coleeau/VMC/Software/3rd Party Software/CO2-Pocket-SBC-2.5-main/Software/DOS65/Core OS/C02Constants.asm

;**************************************************************************************************
;*                                                                                                *
;*              C02 Constants used for the 4.0x releases of C02BIOS4 and C02Monitor4              *
;*                                                                                                *
;*                                                                                                *
;*                                  15/02/2023 (Day/Month/Year)                                   *
;*                                                                                                *
;**************************************************************************************************
; C02BIOS / C02Monitor Version is now at 4.02                                                     *
; - All Constants and Variables are now defined in a single source file (this one) for assembling *
; - both the C02BIOS4 and the C02Monitor4. It is also used for the Template for writing code to   *
; - be used for the C02 Pocket SBC and Adapters.                                                  *
;                                                                                                 *
; - Be sure to include this file at the start of any source file that needs it.                   *
;                                                                                                 *
;**************************************************************************************************
;                                                                                                 *
;          - Page Zero locations $00 to $9F (160 bytes) reserved for user applications            * 
;                                                                                                 *
;**************************************************************************************************
;
PGZERO_ST       .EQU    $A0                     ;Start of Monitor Page 0 use ($A0-$CF, 48 bytes)
;
BUFF_PG0        .EQU    PGZERO_ST+00            ;Default Page zero location for Monitor buffers
;
INBUFF          .EQU    BUFF_PG0+00             ;Input Buffer - 4 bytes ($A0-$A3)
DATABUFF        .EQU    BUFF_PG0+04             ;Data Buffer - 6 bytes ($A4-$A9)
;
;       - 16-bit variables:
HEXDATAH        .EQU    PGZERO_ST+10            ;Hexadecimal input
HEXDATAL        .EQU    PGZERO_ST+11
BINVALL         .EQU    PGZERO_ST+12            ;Binary Value for HEX2ASC
BINVALH         .EQU    PGZERO_ST+13
COMLO           .EQU    PGZERO_ST+14            ;User command address
COMHI           .EQU    PGZERO_ST+15
INDEXL          .EQU    PGZERO_ST+16            ;Index for address - multiple routines
INDEXH          .EQU    PGZERO_ST+17
TEMP1L          .EQU    PGZERO_ST+18            ;Index for word temp value used by Memdump
TEMP1H          .EQU    PGZERO_ST+19
TEMP2L          .EQU    PGZERO_ST+20            ;Index for Text entry
TEMP2H          .EQU    PGZERO_ST+21
PROMPTL         .EQU    PGZERO_ST+22            ;Prompt string address
PROMPTH         .EQU    PGZERO_ST+23
SRCL            .EQU    PGZERO_ST+24            ;Source address for memory operations
SRCH            .EQU    PGZERO_ST+25
TGTL            .EQU    PGZERO_ST+26            ;Target address for memory operations
TGTH            .EQU    PGZERO_ST+27
LENL            .EQU    PGZERO_ST+28            ;Length address for memory operations
LENH            .EQU    PGZERO_ST+29
;
;       - 8-bit variables and constants:
BUFIDX          .EQU    PGZERO_ST+30            ;Buffer index
BUFLEN          .EQU    PGZERO_ST+31            ;Buffer length
IDX             .EQU    PGZERO_ST+32            ;Temp Indexing
IDY             .EQU    PGZERO_ST+33            ;Temp Indexing
TEMP1           .EQU    PGZERO_ST+34            ;Temp - Code Conversion routines
TEMP2           .EQU    PGZERO_ST+35            ;Temp - Memory/EEPROM/SREC routines - Disassembler
TEMP3           .EQU    PGZERO_ST+36            ;Temp - EEPROM/SREC routines
CMDFLAG         .EQU    PGZERO_ST+37            ;Command Flag, bit specific, used by many routines
OPXMDM          .EQU    PGZERO_ST+38            ;Saved Opcode/Xmodem Flag variable
;
;       - Xmodem transfer variables
CRCHI           .EQU    PGZERO_ST+39            ;CRC hi byte  (two byte variable)
CRCLO           .EQU    PGZERO_ST+40            ;CRC lo byte - Operand in Disassembler
CRCCNT          .EQU    PGZERO_ST+41            ;CRC retry count - Operand in Disassembler
PTRL            .EQU    PGZERO_ST+42            ;Data pointer lo byte - Mnemonic in Disassembler
PTRH            .EQU    PGZERO_ST+43            ;Data pointer hi byte - Mnemonic in Disassembler
BLKNO           .EQU    PGZERO_ST+44            ;Block number
;
;        - Macro Loop Counter variables
LPCNTL          .EQU    PGZERO_ST+45            ;Loop Count low byte
LPCNTH          .EQU    PGZERO_ST+46            ;Loop Count high byte
;
;       - Spare Monitor byte for future use
SPARE_M0        .EQU    PGZERO_ST+47            ;Spare Monitor page zero byte
;
;       - BIOS variables, pointers, flags located at top of Page Zero
BIOS_PG0        .EQU    PGZERO_ST+48            ;Start of BIOS page 0 use ($D0-$FF, 48 bytes)
;
;       - BRK handler routine
PCL             .EQU    BIOS_PG0+00             ;Program Counter Low index
PCH             .EQU    BIOS_PG0+01             ;Program Counter High index
PREG            .EQU    BIOS_PG0+02             ;Temp Status Reg
SREG            .EQU    BIOS_PG0+03             ;Temp Stack ptr
YREG            .EQU    BIOS_PG0+04             ;Temp Y Reg
XREG            .EQU    BIOS_PG0+05             ;Temp X Reg
AREG            .EQU    BIOS_PG0+06             ;Temp A Reg
;
;       - 28L92 IRQ handler pointers and status
ICNT_A          .EQU    BIOS_PG0+07             ;Input buffer count
IHEAD_A         .EQU    BIOS_PG0+08             ;Input buffer head pointer
ITAIL_A         .EQU    BIOS_PG0+09             ;Input buffer tail pointer
OCNT_A          .EQU    BIOS_PG0+10             ;Output buffer count
OHEAD_A         .EQU    BIOS_PG0+11             ;Output buffer head pointer
OTAIL_A         .EQU    BIOS_PG0+12             ;Output buffer tail pointer
;
ICNT_B          .EQU    BIOS_PG0+13             ;Input buffer count
IHEAD_B         .EQU    BIOS_PG0+14             ;Input buffer head pointer
ITAIL_B         .EQU    BIOS_PG0+15             ;Input buffer tail pointer
OCNT_B          .EQU    BIOS_PG0+16             ;Output buffer count
OHEAD_B         .EQU    BIOS_PG0+17             ;Output buffer head pointer
OTAIL_B         .EQU    BIOS_PG0+18             ;Output buffer tail pointer
UART_IRT        .EQU    BIOS_PG0+19             ;SC28L92 Interrupt Status byte
;
;       - Real-Time Clock variables
; These are repurposed for adding a Realtime clock chip (DS1501/DS1511)
; The Ticks, Seconds, Minutes and Hours remain the same in function.
; The 16-bit Days variable is replaced however.
; - The DAY_DATE is a new variable. To minimize Page Zero usage, it has two functions
;       Bits 0-4 represent the days of the Month 1-31
;       Bits 5-7 represent the Day of the Week, 1-7 (Saturday=1)
; The Months are handled by the upper 4 bits of the MONTH_YEAR variable
; The Century is handled by a the Year (0-255) and the lower 4 bits of the MONTH_YEAR variable
;
TICKS           .EQU    BIOS_PG0+20             ;Number of timer countdowns = 1 second (100)
SECS            .EQU    BIOS_PG0+21             ;Seconds: 0-59
MINS            .EQU    BIOS_PG0+22             ;Minutes: 0-59
HOURS           .EQU    BIOS_PG0+23             ;Hours: 0-23
DAY_DATE        .EQU    BIOS_PG0+24             ;Day: (bits 5-7) Date: (bits 0-4)
MONTH_CENTURY   .EQU    BIOS_PG0+25             ;Month: (bits 4-7) Century: (bits 0-3)
YEAR            .EQU    BIOS_PG0+26             ;Century 0-255 plus 4 bits as noted above
RTC_TEMP        .EQU    BIOS_PG0+27             ;Temp work byte for updating shared variables
;
;       - Delay Timer variables
MSDELAY         .EQU    BIOS_PG0+28             ;Timer delay countdown byte (255 > 0)
SETMS           .EQU    BIOS_PG0+29             ;Set timeout for delay routines - BIOS use only
DELLO           .EQU    BIOS_PG0+30             ;Delay value BIOS use only
DELHI           .EQU    BIOS_PG0+31             ;Delay value BIOS use only
;
;       - Count variables for 10ms benchmark timing
MS10_CNT        .EQU    BIOS_PG0+32             ;10ms Count variable
SECL_CNT        .EQU    BIOS_PG0+33             ;Seconds Low byte count
SECH_CNT        .EQU    BIOS_PG0+34             ;Seconds High byte count
;
;       - Address and pointers for IDE Interface
LBA_ADDR_LOW    .EQU    BIOS_PG0+35             ;LBA Transfer Address low byte
LBA_ADDR_HIGH   .EQU    BIOS_PG0+36             ;LBA Transfer Address high byte
;
LBA_XFER_CNT    .EQU    BIOS_PG0+37             ;LBA Transfer Count 1-xx (check RAM space!)
LBA_LOW_BYTE    .EQU    BIOS_PG0+38             ;LBA Block number bits 0-7
LBA_HIGH_BYTE   .EQU    BIOS_PG0+39             ;LBA Block number bits 8-15
LBA_EXT_BYTE    .EQU    BIOS_PG0+40             ;LBA Block number bits 16-23
;
BIOS_XFERL      .EQU    BIOS_PG0+41             ;BIOS Move Routine low byte
BIOS_XFERH      .EQU    BIOS_PG0+42             ;BIOS Move Routine high byte
BIOS_XFERC      .EQU    BIOS_PG0+43             ;BIOS Block Count moved (needs to be set)
;
IDE_STATUS_RAM  .EQU    BIOS_PG0+44             ;IDE RAM-Based Status
;
SPARE_B0        .EQU    BIOS_PG0+45             ;Spare byte 0
SPARE_B1        .EQU    BIOS_PG0+46             ;Spare byte 1
;
;       - Timer/Counter Match flag for Delay/Benchmark
MATCH           .EQU    BIOS_PG0+47             ;Bit7 used for Delay, Bit6 used for Benchmark
                                                ;Bits 3,2,1 used for IDE Interrupt Handler
;
;       - Default for RTC tick count - number of IRQs for 1 second
DF_TICKS        .EQU    100                     ;Timer is 10 milliseconds (100 x 10ms = 1 second)
;
;**************************************************************************************************
IBUF_A          .EQU    $0200                   ;Console Input Buffer - 128 bytes
OBUF_A          .EQU    $0280                   ;Console Output Buffer - 128 bytes
;
IBUF_B          .EQU    $0400                   ;Alternate Input Buffer - 128 bytes
OBUF_B          .EQU    $0480                   ;Alternate Output Buffer - 128 bytes
;**************************************************************************************************
SOFTVEC         .EQU    $0300                   ;Start of soft vectors
;The Interrupt structure is vector based. During startup, Page $03 is loaded from ROM.
; The soft vectors are structured to allow inserting additional routines either before
; or after the ROM based routines. This allows flexibility and changing of routine priority.
;
;The main set of vectors occupy the first 16 bytes of Page $03. The ROM handler for
; NMI, BRK and IRQ jump to the first 3 vectors. The following 3 vectors are loaded with
; return addresses to the ROM handler for each. The following 2 vectors are the cold and
; warm entry points for the Monitor. After the basic initialization, the monitor is entered.
;
;The following vector set allows inserts, pre or post for NMI/BRK/IRQ. There a total of 8 inserts
; which occupy 16 bytes. They can be used as required.
; Currently, VECINSRT0 will be used if an IDE Controller is detected.
;
NMIVEC0         .EQU    SOFTVEC+00              ;NMI Vector Entry 0
BRKVEC0         .EQU    SOFTVEC+02              ;BRK Vector Entry 0
IRQVEC0         .EQU    SOFTVEC+04              ;IRQ Vector Entry 0
;
NMIRTVEC0       .EQU    SOFTVEC+06              ;NMI Vector Return 0
BRKRTVEC0       .EQU    SOFTVEC+08              ;BRK Vector Return 0
IRQRTVEC0       .EQU    SOFTVEC+10              ;IRQ Vector Return 0
;
CLDMNVEC0       .EQU    SOFTVEC+12              ;Monitor Cold Entry Vector 0
WRMMNVEC0       .EQU    SOFTVEC+14              ;Monitor Warm Entry Vector 0
;
VECINSRT0       .EQU    SOFTVEC+16              ;1st Vector Insert
VECINSRT1       .EQU    SOFTVEC+18              ;2nd Vector Insert
VECINSRT2       .EQU    SOFTVEC+20              ;3rd Vector Insert
VECINSRT3       .EQU    SOFTVEC+22              ;4th Vector Insert
VECINSRT4       .EQU    SOFTVEC+24              ;5th Vector Insert
VECINSRT5       .EQU    SOFTVEC+26              ;6th Vector Insert
VECINSRT6       .EQU    SOFTVEC+28              ;7th Vector Insert
VECINSRT7       .EQU    SOFTVEC+30              ;8th Vector Insert
;
;**************************************************************************************************
;
;Soft Config values below are loaded from ROM and are the default I/O setup Configuration data that
; the INIT_x routines use. As a result, you can write a routine to change the I/O Configuration
; data and use the standard ROM routines to initialize the I/O without restarting or changing ROM
; A Reset (HW or coded) will reinitialize the I/O with the ROM default I/O Configuration.
;
;There are a total of 32 Bytes Configuration data reserved starting at $0320,
; - 22 bytes are reserved for the NXP SC28L92 DUART.
;
SOFTCFG         .EQU    SOFTVEC+32              ;Start of hardware Config parameters
;
LOAD_28L92      .EQU    SOFTCFG+00              ;SC28L92 Soft Config Data
;
; The configuration for the DUART consists of 14 parameters/commands stored in the following
; - memory locations. Note that these are sent in reverse, i.e., $32E thru $320.
;
;       $320    .DB     %00000011       $03     ;Enable OP0/1 for RTS control Port A/B
;       $321    .DB     %00001010       $A0     ;Disable Receiver/Disable Transmitter B
;       $322    .DB     %00001001       $09     ;Enable Receiver/Disable Transmitter A
;       $323    .DB     %00001111       $0F     ;Interrupt Mask Register setup
;       $324    .DB     %11100000       $E0     ;Aux Register setup for Counter/Timer
;       $325    .DB     %01001000       $48     ;Counter/Timer Upper Preset (18432 decimal)
;       $326    .DB     %00000000       $00     ;Counter/Timer Lower Preset
;       $327    .DB     %11001100       $CC     ;Baud Rate clock for B Rcv/Xmt - 115.2K
;       $328    .DB     %11001100       $CC     ;Baud Rate clock for A Rcv/Xmt - 115.2K
;       $329    .DB     %00110000       $30     ;Reset Transmitter B
;       $32A    .DB     %00100000       $20     ;Reset Receiver B
;       $32B    .DB     %00110000       $30     ;Reset Transmitter A
;       $32C    .DB     %00100000       $20     ;Reset Receiver A
;       $32D    .DB     %00000000       $00     ;Interrupt Mask Register setup (clear)
;       $32E    .DB     %11110000       $F0     ;Command Register A - Disable Power Down
;       $32F    .DB     %11111111       $FF     ;Spare Byte
;
; The MR registers of the DUART also have soft config data loaded here, but is separate from the
; - main register config data, as these are all accessed via a single I/O port (auto-indexed).
; - These are also sent in reverse order as above.
;
;       $330    .DB     %00010111       $17     ;Mode Register 2 data
;       $331    .DB     %11010011       $D3     ;Mode Register 1 Data
;       $332    .DB     %11111001       $F9     ;Mode Register 0 Data
;
;       $333    .DB     %00010111       $17     ;Mode Register 2 data
;       $334    .DB     %11010011       $D3     ;Mode Register 1 Data
;       $335    .DB     %11000001       $C1     ;Mode Register 0 Data
;
;       10 additional bytes all reserved as $FF fill up the remaining soft configuration data.
;
; The Microdrive is initialized and the total LBA count is save here during startup.
;  It is used by various utilities and allows drive capacity sensing without sending additional
;  commands to the Microdrive. A total of 4 bytes are used for a 32-bit LBA count. These are saved
;  at addresses $33C - $33F. Order is low-word/high-word. Each word is low-byte/high/byte.
;
LOAD_IDE        .EQU    SOFTCFG+28              ;IDE/CF-Card Soft Config Data
;
;       $33C    .DW                             ;Low order LBA count
;       $33E    .DW                             ;High order LBA count
;
;Search Buffer is 16 bytes in length. Used to hold search string for text or hex data
SRCHBUFF        .EQU    SOFTCFG+32              ;Located in Page $03 following Hardware Config data
;       $340                                    ;Start of search buffer (16 bytes)
;
;Xmodem/CRC Loader also provides Motorola S19 Record sense and load. Designed to handle the S19
; records from the WDC Assembler/Linker package. This requires a 44 byte buffer to parse each valid
; S1 record, located just before the 132 Byte Xmodem frame buffer. Total Buffer space for the
; Xmodem/CRC Loader is 176 bytes
;
;Valid S-record headers are "S1" and "S9". For S1, the maximum length is "$19" hex. The last S1
; record can be less. S9 record is always the last record with no data. WDC Linker also appends
; a CR/LF to the end of each record for a total of 44 bytes.
;
SRBUFF          .EQU    SOFTCFG+48              ;S-Record buffer, up to 44 bytes in length
;       $350                                    ;Start of S-Record buffer
;
;Xmodem frame buffer. The entire Xmodem frame is buffered here and then checked for proper header
; and frame number, CRC-16 on the data, then moved to user RAM.
RBUFF           .EQU    SOFTCFG+92              ;Xmodem temp 132 byte receive buffer
;       $37C                                    ;Start of Receive buffer for Xmodem
;
;Page $03 is completely allocated for Buffers, Config Data and Vector pointers.
; Some of the buffer space can be used as needed, provided any required Monitor functions are NOT
; being used concurrently.
;
;**************************************************************************************************
;
;Page $05 is used for the Realtime Clock NVRAM read and write routines
NVRAM_DATA      .EQU    $0500                   ;NVRAM Data Buffer address
;
;**************************************************************************************************
;
;Pages $06 - $07 are used for the IDE device Block Buffer (512 bytes)
LBA_BUFFER      .EQU    $0600                   ;Default IDE Block Buffer address
BOOT_BUFFER     .EQU    $0800                   ;Default IDE Boot Buffer address
; 
;**************************************************************************************************
;XMODEM Control Character Constants
SOH             .EQU    $01                     ;Start of Block Header
EOT             .EQU    $04                     ;End of Text marker
ACK             .EQU    $06                     ;Good Block Acknowledge
NAK             .EQU    $15                     ;Bad Block Acknowledged
CAN             .EQU    $18                     ;Cancel character
;
;**************************************************************************************************
;RAM location used for the EEPROM Byte Write routine
; EEPROM is the address offset of the AT28BV256 in the hardware memory map and added to the
; EEPROM address locations required to unlock the AT28BV256 for insitu programming. For more
; information, refer to the AT28BV256 Datasheet.
;
BURN_BYTE       .EQU    $0070                   ;Page 0 RAM for EEPROM BYTE write routine
EEPROM          .EQU    $8000                   ;Offset to EEPROM in hardware
;**************************************************************************************************
;DOS/65 can be called from the Monitor via the Ctrl-B command.
;The start location is just added here for convenience, but should be changed if needed.
;
DOS_65          .EQU    $D630                   ;Default location to Boot DOS/65 (optional)
;**************************************************************************************************
IOPAGE          .EQU    $FE00                   ;I/O Page Base Start Address
;**************************************************************************************************
SC28L92_BASE    .EQU    IOPAGE+$80              ;Beginning of Console UART address
;
UART_MODEREG_A  .EQU    SC28L92_BASE+$00        ;MR0/MR1/MR2 Port A sequential (Read/Write)
UART_STATUS_A   .EQU    SC28L92_BASE+$01        ;UART Status Register Port A (READ)
UART_CLKSEL_A   .EQU    SC28L92_BASE+$01        ;UART Clock Select Port A (WRITE)
UART_RES_A      .EQU    SC28L92_BASE+$02        ;UART Reserved Port A (READ)
UART_COMMAND_A  .EQU    SC28L92_BASE+$02        ;UART Command Register Port A (WRITE)
UART_RECEIVE_A  .EQU    SC28L92_BASE+$03        ;UART Receive Register Port A (READ)
UART_TRANSMIT_A .EQU    SC28L92_BASE+$03        ;UART Transmit Register Port A (WRITE)
;
UART_PORT_CHG   .EQU    SC28L92_BASE+$04        ;UART Input Port Change Register (READ)
UART_AUXCR      .EQU    SC28L92_BASE+$04        ;UART Aux Command Register (WRITE)
UART_ISR        .EQU    SC28L92_BASE+$05        ;UART Interrupt Status Register (READ)
UART_IMR        .EQU    SC28L92_BASE+$05        ;UART Interrupt Mask Register (WRITE)
;
UART_CNTU       .EQU    SC28L92_BASE+$06        ;Counter/Timer Upper Register (READ)
UART_CNTUP      .EQU    SC28L92_BASE+$06        ;Counter/Timer Upper Preset Register (WRITE)
UART_CNTL       .EQU    SC28L92_BASE+$07        ;Counter/Timer Lower Register (READ)
UART_CNTLP      .EQU    SC28L92_BASE+$07        ;Counter/Timer Lower Preset Register (WRITE)
;
UART_MODEREG_B  .EQU    SC28L92_BASE+$08        ;MR0/MR1/MR2 Port B sequential Read/Write
UART_STATUS_B   .EQU    SC28L92_BASE+$09        ;UART Status Register Port B (READ)
UART_CLKSEL_B   .EQU    SC28L92_BASE+$09        ;UART Clock Select Port B (WRITE)
UART_RES_B      .EQU    SC28L92_BASE+$0A        ;UART Reserved Port B (READ)
UART_COMMAND_B  .EQU    SC28L92_BASE+$0A        ;UART Command Register Port B (WRITE)
UART_RECEIVE_B  .EQU    SC28L92_BASE+$0B        ;UART Receive Register Port B (READ)
UART_TRANSMIT_B .EQU    SC28L92_BASE+$0B        ;UART Transmit Register Port B (WRITE)
;
UART_MISC       .EQU    SC28L92_BASE+$0C        ;UART Miscellaneous Register Intel (Read/Write)
UART_INPUT_PORT .EQU    SC28L92_BASE+$0D        ;UART Input Port Register (READ)
UART_OUT_CFG    .EQU    SC28L92_BASE+$0D        ;UART Ouput Port Config Register (WRITE)
UART_START_CNT  .EQU    SC28L92_BASE+$0E        ;UART Start Counter Command (READ)
UART_SOPR_CMD   .EQU    SC28L92_BASE+$0E        ;UART Set Output Port Bits Register (WRITE)
UART_STOP_CNT   .EQU    SC28L92_BASE+$0F        ;UART Stop Counter Command (READ)
UART_ROPR_CMD   .EQU    SC28L92_BASE+$0F        ;UART Reset Output Port Bits Register (WRITE)
;
;Additional Hardware
; Adding BIOS definitions for Realtime Clock chip - DS1511
; uses the first 16 addresses for RTC registers and basic operation
; uses two addresses for extended RAM of 256 bytes
;
; upper addresses are used for a 16-bit IDE interface (below)
; NOTE: offset $11 and $12 are unused (reserved per the datasheet).
;
RTC_IDE_BASE    .EQU    IOPAGE+$60              ;Beginning of Realtime Clock address
;
RTC_SECONDS     .EQU    RTC_IDE_BASE+$00        ;Seconds in BCD 00-59
RTC_MINUTES     .EQU    RTC_IDE_BASE+$01        ;Minutes in BCD 00-59
RTC_HOURS       .EQU    RTC_IDE_BASE+$02        ;Hours in BCD 00-23
RTC_DAY         .EQU    RTC_IDE_BASE+$03        ;Day in BCD 1-7
RTC_DATE        .EQU    RTC_IDE_BASE+$04        ;Date in BCD 1-31
RTC_MONTH       .EQU    RTC_IDE_BASE+$05        ;Month in BCD 1-12
RTC_YEAR        .EQU    RTC_IDE_BASE+$06        ;Year in BCD 00-99
RTC_CENTURY     .EQU    RTC_IDE_BASE+$07        ;Century in BCD 00-39
;
RTC_ALARM_SEC   .EQU    RTC_IDE_BASE+$08        ;Alarm Seconds in BCD 00-59
RTC_ALARM_MIN   .EQU    RTC_IDE_BASE+$09        ;Alarm Minutes in BCD 00-59
RTC_ALARM_HRS   .EQU    RTC_IDE_BASE+$0A        ;Alarm Hours in BCD 00-23
RTC_ALARM_DYDT  .EQU    RTC_IDE_BASE+$0B        ;Alarm Day/Date in BCD 0-7 1-31
RTC_WTCHDOG_01  .EQU    RTC_IDE_BASE+$0C        ;Watchdog 0.1 / 0.01 Seconds in BCD 00-99
RTC_WTCHDOG_10  .EQU    RTC_IDE_BASE+$0D        ;Watchdog 10 / 1 Seconds in BCD 00-99
;
RTC_CONTROL_A   .EQU    RTC_IDE_BASE+$0E        ;Control A
RTC_CONTROL_B   .EQU    RTC_IDE_BASE+$0F        ;Control B
RTC_RAM_ADDR    .EQU    RTC_IDE_BASE+$10        ;Extended RAM address
RTC_RAM_DATA    .EQU    RTC_IDE_BASE+$13        ;Extended RAM data
;
; Adding BIOS definitions for 16-bit IDE interface
; uses two addresses for Upper Byte Latch read / write
; uses eight addresses for Command Block Registers
; uses two addresses for Control Block Registers
;
IDE_16_READ     .EQU    RTC_IDE_BASE+$14        ;Upper byte Read address
IDE_16_WRITE    .EQU    RTC_IDE_BASE+$15        ;Upper byte Write address
;
; Adding BIOS definitions for IDE Controller (HARD DISK, Flash Module, etc.)
; Hardware Adapter provides a 16-bit IDE Port per:
;  Seagate ATA Interface Reference Manual 36111-001, Rev. C (21st May 1993)
;
; Control Block Registers
IDE_ALT_STATUS  .EQU    RTC_IDE_BASE+$16        ;Alternate Status Register (READ)
IDE_DEV_CTRL    .EQU    RTC_IDE_BASE+$16        ;Device Control Register (WRITE)
IDE_DRV_ADDR    .EQU    RTC_IDE_BASE+$17        ;Drive Address Register (READ)
;
; Command Block Registers
IDE_DATA        .EQU    RTC_IDE_BASE+$18        ;Data Register (R/W)
IDE_ERROR       .EQU    RTC_IDE_BASE+$19        ;Error Register (READ)
IDE_FEATURE     .EQU    RTC_IDE_BASE+$19        ;Feature Register (WRITE)
IDE_SCT_CNT     .EQU    RTC_IDE_BASE+$1A        ;Sector Count Register
IDE_SCT_NUM     .EQU    RTC_IDE_BASE+$1B        ;Sector Number Register
IDE_CYL_LOW     .EQU    RTC_IDE_BASE+$1C        ;Cylinder Low Register
IDE_CYL_HIGH    .EQU    RTC_IDE_BASE+$1D        ;Cylinder High Register
IDE_DRV_HEAD    .EQU    RTC_IDE_BASE+$1E        ;Drive/Head Register
IDE_STATUS      .EQU    RTC_IDE_BASE+$1F        ;Status Register (READ)
IDE_COMMAND     .EQU    RTC_IDE_BASE+$1F        ;Command Register (WRITE)
;
;**************************************************************************************************
        .END
