coleeau/VMC/Software/3rd Party Software/CO2-Pocket-SBC-2.5-main/Software/ROM Code/BIOS/C02BIOS4.asm

;**************************************************************************************************
;*    C02BIOS 4.02 - Release version for Pocket SBC  (c)2013-2023 by Kevin E. Maier 03/04/2023    *
;*                                                                                                *
;* BIOS Version 4.02 supports the following 3.3V hardware specification:                          *
;*                                                                                                *
;*  - W65C02S with clock rate up to 8.0 MHz                                                       *
;*  - AS6C66256 32KB Static RAM                                                                   *
;*  - AT28BV256 32KB EEPROM ROM                                                                   *
;*  - ATF22LV10C Single Glue Logic                                                                *
;*  - NXP SC28L92 DUART for Console Port / Aux Serial Port / Timer                                *
;*  - TL7533 Reset Circuit (positive & negative Reset signals)                                    *
;*  - DS1233A Reset Circuit for NMI Panic Trigger                                                 *
;*                                                                                                *
;* Hardware map is flexible via Glue logic                                                        *
;*  - 5 I/O selects @ 32-bytes wide             $FE00 - $FE9F                                     *
;*  - 1 I/O select used by SC28L92 DUART        $FE80 - $FE9F                                     *
;*  - 4 I/O selects available on expansion bus  $FE00 - $FE7F                                     *
;*                                                                                                *
;* Additional Hardware support:                                                                   *
;* - Modified CF-Card/RTC adapter card                                                            *
;*  - ATF16LV8C Glue Logic used for I/O decoding and Latch Selection                              *
;*  - MicroDrive IDE PATA interface                                                               *
;*    - 16-bit upper latch for data read/write                                                    *
;*  - DS15x1W Realtime Clock/Calendar                                                             *
;*                                                                                                *
;* BIOS Functions are divided into groups as follows:                                             *
;*                                                                                                *
;* SC28L92 DUART functions:                                                                       *
;* - Full duplex interrupt-driven/buffered I/O for both DUART Channels                            *
;* - Precision timer services with 10ms accuracy                                                  *
;* - RTC based Jiffy Clock, Sec, Min, Hour, Date                                                  *
;* - Accurate delays from 10ms to ~46 hours                                                       *
;* - 10ms Benchmark Timing to 65535.99 seconds                                                    *
;*                                                                                                *
;* IDE Controller Functions supporting PATA 16-bit Data Transfers:                                *
;* - Multiple Block transfers are now supported for Read/Write/Verify Block commands              *
;* - Reset IDE (recalibrate command)                                                              *
;* - Get IDE Status and Extended Error codes                                                      *
;* - Get IDE Identification Block                                                                 *
;* - Read a Block from IDE device                                                                 *
;* - Write a Block to IDE device                                                                  *
;* - Verify the last Block from IDE device                                                        *
;* - Set the LBA Block ID for Read/Write/Verify                                                   *
;* - Set the Memory Address to transfer Block data to/from                                        *
;* - Enable the Write Cache on IDE controller                                                     *
;* - Disable the Write Cache on IDE controller                                                    *
;*                                                                                                *
;* Maxim Realtime Clock functions:                                                                *
;* - Detect RTC (signature in NVRAM) and Load software RTC variables                              *
;* - Read and Write NVRAM block                                                                   *
;*                                                                                                *
;* BIOS Features:                                                                                 *
;* - Extendable BIOS structure with soft vectors                                                  *
;* - Soft config parameters for I/O devices                                                       *
;* - Monitor cold/warm start soft vectored                                                        *
;* - Panic Routine to restore Vectors and Reinitialize Console                                    *
;* - Fully relocatable code (sans page $FF)                                                       *
;* - JUMP Table at $FF00 - 32 functions                                                           *
;* - Default memory allocation of 2KB (includes 160 bytes of I/O mapping)                         *
;**************************************************************************************************
        PL      66      ;Page Length
        PW      132     ;Page Width (# of char/line)
        CHIP    W65C02S ;Enable WDC 65C02 instructions
        PASS1   OFF     ;Set ON when used for debug
        INCLIST ON      ;Set ON for listing Include files
;**************************************************************************************************
;
; C02BIOS Version 4.0x is based on C02BIOS Version 3.04.
;
; - Main changes are to support the NXP SC28L92 DUART.
; - Minor changes to Page Zero to include required pointers, etc. for the second serial port.
; - IDE support now focused on IBM/Hitachi Microdrive with 35-pin PATA interface.
; - Removal of Compact Flash specific code, as no longer required for standard IDE.
; - Minor change for testing IDE busy, no more JSR, integrated test into each routine.
;
;**************************************************************************************************
;
; This BIOS and Monitor version also use a common source file for constants and variables used by
; both. This just simplifies keeping both code pieces in sync.
;
        INCLUDE         C02Constants4.asm
;
;**************************************************************************************************
;       - Monitor JUMP table: 32 JUMP calls are Defined, with one Call (02) currently Reserved.
;
M_COLD_MON      .EQU    $E000           ;Call 00        Monitor Cold Start
M_WARM_MON      .EQU    $E003           ;Call 01        Monitor Warm Start
;
M_RESERVE2      .EQU    $E006           ;Call 02        Reserved
;
M_MOVE_RAM      .EQU    $E009           ;Call 03        Move Memory
M_FILL_LP       .EQU    $E00C           ;Call 04        Fill Memory
M_BSOUT         .EQU    $E00F           ;Call 05        Send Backspace
M_XMDM_SAVE     .EQU    $E012           ;Call 06        Xmodem Save Entry
M_XMDM_LOAD     .EQU    $E015           ;Call 07        Xmodem Load Entry
M_BENCH         .EQU    $E018           ;Call 08        Benchmark Start
M_QUITB         .EQU    $E01B           ;Call 09        Benchmark Stop/End
M_TIME          .EQU    $E01E           ;Call 10        System Date/Time
M_PRSTAT1       .EQU    $E021           ;Call 11        CPU Status Display
M_DIS_LINE      .EQU    $E024           ;Call 12        Disassemble Line of Code
M_INCINDEX      .EQU    $E027           ;Call 13        Increment Index by 1
M_DECINDEX      .EQU    $E02A           ;Call 14        Decrement Index by 1
M_RDLINE        .EQU    $E02D           ;Call 15        Read Line from Terminal
M_RDCHAR        .EQU    $E030           ;Call 16        Read Character from Terminal
M_HEXIN2        .EQU    $E033           ;Call 17        Hex input 2 characters
M_HEXIN4        .EQU    $E036           ;Call 18        Hex input 4 characters
M_HEX2ASC       .EQU    $E039           ;Call 19        Convert Hex to ASCII
M_BIN2ASC       .EQU    $E03C           ;Call 20        Convert Binary to ASCII
M_ASC2BIN       .EQU    $E03F           ;Call 21        Convert ASCII to Binary
M_BEEP          .EQU    $E042           ;Call 22        Send BEEP to Terminal
M_DOLLAR        .EQU    $E045           ;Call 23        Send $ to Terminal
M_CROUT         .EQU    $E048           ;Call 24        Send C/R to Terminal
M_SPC           .EQU    $E04B           ;Call 25        Send ASCII Space to Terminal
M_PRBYTE        .EQU    $E04E           ;Call 26        Print Byte to Terminal
M_PRWORD        .EQU    $E051           ;Call 27        Print Word to Terminal
M_PRASC         .EQU    $E054           ;Call 28        Print ASCII to Terminal
M_PROMPT        .EQU    $E057           ;Call 29        Send Message by number to Terminal
M_PROMPTR       .EQU    $E05A           ;Call 30        Send Message by address to Terminal
M_CONTINUE      .EQU    $E05D           ;Call 31        Y/N Prompt to Continue Command
;
;**************************************************************************************************
        .ORG    $F800   ;2KB reserved for BIOS, I/O device selects (160 bytes)                    *
;**************************************************************************************************
;                               START OF BIOS CODE                                                *
;**************************************************************************************************
;C02BIOS version used here is 4.02 (updated release)
; Contains the base BIOS routines in top 2KB of EEPROM
; - Input/Feedback from "BDD" - modified CHRIN/CHROUT I/O routines - saves 12 bytes
; - $F800 - $F9FF 512 bytes for BIOS SC28L92, NMI Panic routine
; - $FA00 - $FDFF reserved for BIOS expansion (1KB)
; - $FE00 - $FE7F reserved for HW (4-I/O selects, 32 bytes wide)
; - $FE80 - $FE9F SC28L92 DUART (32 bytes wide, only 16 bytes used)
; - $FEA0 - $FEFF used for Vector and Hardware configuration data
; - $FF00 - $FFFF JMP table, CPU startup, NMI/BRK/IRQ pre-post routines, Page $03 init, BIOS msg
;
; UPDATES:
; Note: C02BIOS 3.04 is the base for 4.0x.
;
; Fixed IRQ enable for IDE controller. Also streamlined some startup routines. 11th Oct 2020
; Eliminates IDE byte swapping to ensure compatibility with standard formats. 20th January 2021
; Allocate $0400-$04FF for second UART buffer space. 5th February 2021
; Default RTC NVRAM buffer space at $0500-$05FF. 5th February 2021
; Default IDE Block buffer at $0600-$07FF. 5th February 2021
; Panic Routine changed, no longer saves multiple pages, just restores system. 5th February 2021
; New routine to Start Benchmark Counter. Allows counter Start/Stop (pause). 5th February 2021
; Some minor cleanup and fixed a few bugs in the RTC and IDE routines. 14th May 2021
; Update Init and ISR routines to support NXP SC28L92 DUART, both ports and timer. 31st August 2021
; Update Character I/O routines for Serial Ports. Supports on-chip FIFOs Rcv/Xmt. 14th October 2021
; Updates to support IDE as Hitachi MicroDrive (3.3V prototype). 9th August 2021
; Bios 4.00 and later now support multiple block transfers to/from IDE device. 13th September 2021
; Removed Extended Delay (XLdelay) routine, not ever used except for testing. 
;
; Note: C02BIOS 4.01 Updates 17th October, 2021
;
; Streamlined IDE Detection, Initialize and Reset routines.
; - Recalibrate Command removed from Detection, Diagnostics only are run.
; - Likewise, Diagnositcs removed from Reset command, Recalibrate only is done.
; - Removed detection for LBA support, as the Hitachi 3K8 Microdrive supports this natively.
;
; Added support for Receive/Transmit FIFOs for SC28L92 DUART.
;
; Note: C02BIOS 4.02 Updates 31st May, 2022
;
; Rearranged the ISR for the DUART, the two comm ports are now shorter handlers by a few clock
; cycles and the code itself is 12 bytes shorter. The Counter/Timer handler is increased by
; 3 clock cycles. Minor change to RTC ISR, saves a byte and 2 clock cycles ;-)
;
; Minor change to RTC/IDE Inits... saves another 4 bytes ;-)

; NOTE: C02BIOS 4.02 Updates 15th August, 2022
; - No actual code changes!
; - Slight restructuring of routines to minimze any page boundary impacts on clock cycles!
;
; NOTE: C02BIOS 4.02 Updates 15th February, 2023
; - No actual code changes!
; - Slight changes in Page Zero locations. As two bytes were freed up for the SC28L92 BIOS,
;   the two free locations have been moved and labeled near the top of Page Zero, now marked as:
;   SPARE_B0 and SPARE_B1
;**************************************************************************************************
; The following 32 functions are provided by BIOS via the JMP Table
; $FF48 - Reserved for future expansion (1 available)
;
; $FF00 IDE_RESET       ;Reset IDE Controller (Recalibrate Command)
; $FF03 IDE_GET_STAT    ;Get Status and Error code
; $FF06 IDE_IDENTIFY    ;Load IDE Identity Data at $0600
; $FF09 IDE_READ_LBA    ;Read LBA into memory
; $FF0C IDE_WRITE_LBA   ;Write LBA from memory
; $FF0F IDE_VERFY_LBA   ;Verify LBA from last Read/Write
; $FF12 IDE_SET_LBA     ;Set LBA number (24-bit support only)
; $FF15 IDE_SET_ADDR    ;Set LBA transfer address (16-bit plus block count)
; $FF18 IDE_EN_CACHE    ;Enable IDE Write Cache
; $FF1B DIS_CACHE JMP   ;Disable IDE Write Cache
;
; $FF1E RTC_NVRD        ;Read NVRAM (256 bytes) from RTC to memory (16-bit)
; $FF21 RTC_NVWR        ;Write NVRAM (256 bytes) from memory to RTC (16-bit)
; $FF24 RTC_INIT        ;Initialize software RTC from hardware RTC
;
; $FF27 CHRIN2          ;Data input from aux port
; $FF2A CHROUT2         ;Data output to aux port
;
; $FF2D CNT_INIT        ;Reset Benchmark timing counters/Start 10ms benchmark timer
; $FF30 CNT_STRT        ;Start 10ms benchmark timing counter
; $FF33 CNT_STOP        ;Stop 10ms benchmark timing counter
;
; $FF36 CHRIN_NW        ;Data input from console, no waiting, clear carry if none
; $FF39 CHRIN           ;Data input from console
; $FF3C CHROUT          ;Data output to console
;
; $FF3F SET_DLY         ;Set delay value for milliseconds and 16-bit counter
; $FF42 EXE_MSDLY       ;Execute millisecond delay 1-256 * 10 milliseconds
; $FF45 EXE_LGDLY       ;Execute long delay; millisecond delay * 16-bit count

; $FF48 Reserved        ;Reserved for future expansion
;
; $FF4B INIT_VEC        ;Initialize soft vectors at $0300 from ROM
; $FF4E INIT_CFG        ;Initialize soft config values at $0320 from ROM
;
; $FF51 INIT_28L92      ;Initialize SC28L92 - Port A as console at 115.2K, 8-N-1 RTS/CTS
; $FF54 RESET_28L92     ;Reset SC28L92 - called before INIT_28L92
;
; $FF57 MONWARM         ;Monitor warm start - jumps to page $03
; $FF5A MONCOLD         ;Monitor cold start - jumps to page $03
; $FF5D COLDSTRT        ;System cold start - RESET vector for 65C02
;**************************************************************************************************
;               Data In and Out routines for Console I/O buffer                                   *
;**************************************************************************************************
;Data Input A routines
;CHRIN_NW uses CHRIN, returns if data is not available from the buffer with carry flag clear,
; else returns with data in A Reg and carry flag set. CHRIN waits for data to be in the buffer,
; then returns with carry flag set. Receive is IRQ driven/buffered with a size of 128 bytes.
; Note: CHRIN_NW is only on Port A, which is used for a Console.
;
CHRIN_NW        CLC                     ;Clear Carry flag for no data (2)
                LDA     ICNT_A          ;Get buffer count (4)
                BNE     GET_CH          ;Branch if buffer is not empty (2/3)
                RTS                     ;Or return to caller (6)
;
CHRIN           LDA     ICNT_A          ;Get data count (3)
                BEQ     CHRIN           ;If zero (no data, loop back) (2/3)
;
GET_CH          PHY                     ;Save Y Reg (3)
                LDY     IHEAD_A         ;Get the buffer head pointer (3)
                LDA     IBUF_A,Y        ;Get the data from the buffer (4)
                INC     IHEAD_A         ;Increment head pointer (5)
                RMB7    IHEAD_A         ;Strip off bit 7, 128 bytes only (5)
                DEC     ICNT_A          ;Decrement the buffer count (5)
;
                PLY                     ;Restore Y Reg (4)
                SEC                     ;Set Carry flag for data available (2)
                RTS                     ;Return to caller with data in A Reg (6)
;
;Data Output A routine: puts the data in the A Reg into the xmit buffer, data in
; A Reg is preserved on exit. Transmit is IRQ driven/buffered with a size of 128 bytes.
;
CHROUT          PHY                     ;Save Y Reg (3)
OUTCH           LDY     OCNT_A          ;Get data output count in buffer (3)
                BMI     OUTCH           ;Check buffer full, if yes, check Xmit on (2/3)
;
                LDY     OTAIL_A         ;Get the buffer tail pointer (3)
                STA     OBUF_A,Y        ;Place data in the buffer (5)
                INC     OTAIL_A         ;Increment Tail pointer (5)
                RMB7    OTAIL_A         ;Strip off bit 7, 128 bytes only (5)
                INC     OCNT_A          ;Increment data count (5)
;
                LDY     #%00000100      ;Get mask for xmit on (2)
                STY     UART_COMMAND_A  ;Turn on xmit (4)
;
                PLY                     ;Restore Y Reg (4)
                RTS                     ;Return to caller (6)
;
;Data Input B routine
; CHRIN waits for data to be in the buffer, then returns with data in A reg.
; Receive is IRQ driven/buffered with a size of 128 bytes.
;
CHRIN2          LDA     ICNT_B          ;Get data count (3)
                BEQ     CHRIN2          ;If zero (no data, loop back) (2/3)
;
                PHY                     ;Save Y Reg (3)
                LDY     IHEAD_A         ;Get the buffer head pointer (3)
                LDA     IBUF_B,Y        ;Get the data from the buffer (4)
                INC     IHEAD_B         ;Increment head pointer (5)
                RMB7    IHEAD_B         ;Strip off bit 7, 128 bytes only (5)
                DEC     ICNT_B          ;Decrement the buffer count (5)
;
                PLY                     ;Restore Y Reg (4)
                RTS                     ;Return to caller with data in A Reg (6)
;
;Data Output B routine: puts the data in the A Reg into the xmit buffer, data in
; A Reg is preserved on exit. Transmit is IRQ driven/buffered with a size of 128 bytes.
;
CHROUT2         PHY                     ;Save Y Reg (3)
OUTCH2          LDY     OCNT_B          ;Get data output count in buffer (3)
                BMI     OUTCH2          ;Check against limit, loop back if full (2/3)
;
                LDY     OTAIL_B         ;Get the buffer tail pointer (3)
                STA     OBUF_B,Y        ;Place data in the buffer (5)
                INC     OTAIL_B         ;Increment Tail pointer (5)
                RMB7    OTAIL_B         ;Strip off bit 7, 128 bytes only (5)
                INC     OCNT_B          ;Increment data count (5)
;
                LDY     #%00000100      ;Get mask for xmit on (2)
                STY     UART_COMMAND_B  ;Turn on xmit (4)
;
                PLY                     ;Restore Y Reg (4)
                RTS                     ;Return to caller (6)
;
;**************************************************************************************************
;START of IDE Routines for Hitachi 3K8 MicroDrive                                                 *
;**************************************************************************************************
;
IDE_READ_LBA                            ;Read a Block of data from IDE device
;
; This routine requires loading the requested LBA into the appropriate registers and
; issuing the READ command 20h. The LBA limit supported for the BIOS are bits 0-23,
; so bits 24-27 are always set to 0. This provides access to IDE devices up to 8GB.
;
; Once the registers/parameters are setup, the Read Block command is issued.
; This results in an interrupt being generated. The ISR handles the transfer of LBA
; data from the IDE Drive to memory.
;
; BIOS 4.00 and later supports multiple block transfers, increasing performance.
;
; The registers used are the same for read/write/verify. These are:
;
;       IDE_COMMAND = function requested (20h = READ LBA command)
;       IDE_DRV_HEAD = (Upper 4 bits) used as:
;               bit 7 = 1 per Seagate documentation
;               bit 6 = 1 for LBA mode
;               bit 5 = 1 per Seagate documentation
;               bit 4 = 0 for Drive 0
;       IDE_DRV_HEAD = LBA Address bits 27-24 (lower 4 bits) - not used, always 0000
;       IDE_CYL_HIGH = LBA Address bits 23-16
;       IDE_CYL_LOW = LBA Address bits 15-8
;       IDE_SCT_NUM = LBA Address bits 7-0
;       IDE_SCT_CNT = number of blocks to read
;
                JSR     IDE_SET_PARMS   ;Setup required parameters (6)
                LDA     #$20            ;Get Read LBA command (2)
IDENT_READ                              ;Identify Command jumps here to complete
                SMB3    MATCH           ;Set Read LBA bit (5)
                STA     IDE_COMMAND     ;Send command to IDE Controller (4)
;
LBA_RD_CMD
                LDA     IDE_ALT_STATUS  ;Get IDE Alternate Status register (4)
                BMI     LBA_RD_CMD      ;Loop until IDE controller not Busy (2/3)
;
LBA_RD_WAIT
                LDA     IDE_ALT_STATUS  ;Get IDE Alternate Status register (4)
                CMP     #$50            ;Compare for ready (2)
                BNE     LBA_RD_ERR      ;If not, check for error condition (2/3)
LBA_RD_OK
                BBS3    MATCH,LBA_RD_OK ;Wait for Read completed via ISR (5/6)
                RTS                     ;Return to caller (status in A Reg) (6)
LBA_RD_ERR
                LSR     A               ;Shift error bit to carry (2)
                BCC     LBA_RD_WAIT     ;If clear, loop back and continue waiting (2/3)
;
                RMB3    MATCH           ;Reset Read LBA bit (no ISR invoked) (5)
IDE_RWV_FIN
                LDA     IDE_ALT_STATUS  ;Get IDE Alternate Status register (4)
                STA     IDE_STATUS_RAM  ;Update RAM Status Register (3)
                RTS                     ;Return to caller (6)
;
IDE_WRITE_LBA                           ;Write a block of data to LBA
;
; This routine requires loading the requested LBA into the appropriate registers and
; issuing the WRITE command 30h. The LBA limit supported for the BIOS are bits 0-23,
; so bits 24-27 are always set to 0. This provides access to IDE devices up to 8GB.
;
; The registers used are the same for read/write/verify. These are:
;
;       IDE_COMMAND = function requested (30h = WRITE LBA command)
;       IDE_DRV_HEAD = (Upper 4 bits) used as:
;               bit 7 = 1 per Seagate documentation
;               bit 6 = 1 for LBA mode
;               bit 5 = 1 per Seagate documentation
;               bit 4 = 0 for Drive 0
;       IDE_DRV_HEAD = LBA Address bits 27-24 (lower 4 bits) - not used, always 0000
;       IDE_CYL_HIGH = LBA Address bits 23-16
;       IDE_CYL_LOW = LBA Address bits 15-8
;       IDE_SCT_NUM = LBA Address bits 7-0
;       IDE_SCT_CNT = number of blocks to write
;
                JSR     IDE_SET_PARMS   ;Setup required parameters (6)
;
                SMB2    MATCH           ;Set Write LBA bit (5)
                LDA     #$30            ;Get Write LBA command (2)
                STA     IDE_COMMAND     ;Send command to IDE Controller (4)
LBA_WR_CMD
                LDA     IDE_ALT_STATUS  ;Get IDE Alternate Status register (4)
                BMI     LBA_WR_CMD      ;Loop until IDE controller not Busy (2/3)
                LSR     A               ;Shift Error bit into Carry flag (2)
                BCS     IDE_WRITE_ERR   ;If Carry set, IDE error (2/3)
;
; Write Block routine integrated into IDE_WRITE_LBA
;
; - High byte needs to be loaded into the latch before the
;   low byte is loaded into the Data Register!
;
IDE_WRITE_BLK                           ;Write a block of data
                PHY                     ;Save Y reg (3)
                LDY     #$01            ;Set offset for high byte latch (2)
;
IDE_WRITE_LOOP
                LDA     IDE_ALT_STATUS  ;Get IDE Alternate Status register (4)
                AND     #%00001000      ;Check for DRQ active (2)
                BEQ     IDE_WR_FIN      ;If not active, exit (below) (2/3)
IDE_WR_WBLK
                LDA     (BIOS_XFERL),Y  ;Get first byte of buffer+1 (5)
                STA     IDE_16_WRITE    ;Place into high byte latch (4)
                LDA     (BIOS_XFERL)    ;Get first byte of buffer (5)
                STA     IDE_DATA        ;Write buffer to IDE (writes a word) (4)
;
; - Buffer index needs to be incremented twice
;
                INC     BIOS_XFERL      ;Increment pointers once (5)
                BNE     IDE_WR_BLK1     ; (2/3)
                INC     BIOS_XFERH      ; (5)
IDE_WR_BLK1
                INC     BIOS_XFERL      ;Increment pointers again (5)
                BNE     IDE_WRITE_LOOP  ; (2/3)
                INC     BIOS_XFERH      ; (5)
                BRA     IDE_WRITE_LOOP  ;Loop back for 256 words (3)
;
IDE_WR_FIN
; when DRQ ends, 512 bytes have been sent to IDE controller. Controller then sets BUSY,
; when finished processing data, controller clears BUSY and generates an interrupt.
; So, we test for BUSY first and wait until the block is written.
;
                LDA     IDE_ALT_STATUS  ;Get IDE Alternate Status register (4)
                BMI     IDE_WR_FIN      ;Loop until BUSY bit is clear (2/3)
;
                DEC     BIOS_XFERC      ;Decrement Block Count to transfer (5)
                BNE     IDE_WRITE_LOOP  ;If not zero, branch back to write next LBA (2/3)
;
WR_WAIT
                BBS2    MATCH,WR_WAIT   ;Wait for Write completed via ISR (5,6)
                PLY                     ;Restore Y reg (4)
                RTS                     ;Return to caller (6)
IDE_WRITE_ERR
                RMB2    MATCH           ;Reset Write LBA bit (no ISR) (5)
                BRA     IDE_RWV_FIN     ;Branch and finish up (3)
;
IDE_VERIFY_LBA                          ;Verify LBA after write
;
; This routine requires loading the requested LBA into the appropriate registers and
; issuing the VERIFY command 40h. The LBA limit supported for the BIOS are bits 0-23,
; so bits 24-27 are always set to 0. This provides access to IDE devices up to 8GB.
;
; It is identical to a Read Block command except no Data is transferred, only verified.
; Also, no DRQ is set, but an interrupt is generated after the Verify is completed.
;
; The registers used are the same for read/write/verify. These are:
;
;       IDE_COMMAND = function requested (40h = Verify LBA command)
;       IDE_DRV_HEAD = (Upper 4 bits) used as:
;               bit 7 = 1 per Seagate documentation
;               bit 6 = 1 for LBA mode
;               bit 5 = 1 per Seagate documentation
;               bit 4 = 0 for Drive 0
;       IDE_DRV_HEAD = LBA Address bits 27-24 (lower 4 bits) - not used, always 0000
;       IDE_CYL_HIGH = LBA Address bits 23-16
;       IDE_CYL_LOW = LBA Address bits 15-8
;       IDE_SCT_NUM = LBA Address bits 7-0
;       IDE_SCT_CNT = number of blocks to verify
;
                JSR     IDE_SET_PARMS   ;Setup required parameters (6)
;
                SMB1    MATCH           ;Set Verify LBA bit (5)
                LDA     #$40            ;Get Verify LBA command (2)
                STA     IDE_COMMAND     ;Send command to IDE Controller (4)
LBA_VF_CMD
                LDA     IDE_ALT_STATUS  ;Get IDE Alternate Status register (4)
                BMI     LBA_VF_CMD      ;Loop until IDE controller not Busy (2/3)
                LSR     A               ;Shift Error bit into Carry flag (2)
                BCC     VF_FINISH       ;If Carry clear, no error (2/3)
;
                RMB1    MATCH           ;Reset Verify LBA bit (no ISR) (5)
                BRA     IDE_RWV_FIN     ;Branch and finish up (3)
;
VF_FINISH
                JSR     TST_IDE_RDY     ;Wait for IDE Controller ready (6)
VF_WAIT
                BBS1    MATCH,VF_WAIT   ;Wait for Verify to complete via ISR (5,6)
                RTS                     ;Return to caller (6)
;
IDE_SET_ADDRESS                         ;Set Address for LBA (read/write)
;
; This routine uses the A,Y,X registers to setup the address in memory that a block
; will be read to or written from (16-bit address), along with the block count.
; The Register usage is as follows:
;       A Register = Memory address low byte
;       Y Register = Memory address high byte
;       X Register = Block count to transfer (device dependent)
                STA     LBA_ADDR_LOW    ;Set LBA low byte address (3)
                STY     LBA_ADDR_HIGH   ;Set LBA high byte address (3)
                STX     LBA_XFER_CNT    ;Set LBA Block count for xfer (3)
                RTS                     ;Return to caller (6)
;
IDE_SET_LBA                             ;Set LBA block for transfer (read/write)
;
; This routine sets the variables used to select the starting LBA for transfer.
; The Register usage is as follows:
;       A Register = LBA Address bits 7-0
;       Y Register = LBA Address bits 15-8
;       X Register = LBA Address bits 23-16
                STA     LBA_LOW_BYTE    ;Store Address bits 0-7 (3)
                STY     LBA_HIGH_BYTE   ;Store Address bits 8-15 (3)
                STX     LBA_EXT_BYTE    ;Store Address bits 16-23 (3)
                RTS                     ;Return to caller (6)
;
IDE_SET_PARMS                           ;Set All parameters for LBA transfers
;
; This routine sets the LBA number used for all transfers.
; - The IDE Controller is checked first to ensure it's ready to receive parameters
; - then the requested LBA (stored in Page Zero variables) are loaded into the
; - IDE Controller registers, followed by the required Mode parameters.
; - Last, the transfer address is setup which points to the location in memory that
; - will be used to transfer Data to or from.
;
                LDA     IDE_ALT_STATUS  ;Get IDE Alternate Status register (4)
                BMI     IDE_SET_PARMS   ;Loop until BUSY bit is clear (2/3)
;
; The following code loop saves space for transferring parameter data over to the
; working memory locations. However, the savings in ROM space incures a penalty in
; clock cycles (64 vs 28) for execution. This does impact the actual data transfer
; rate acheived. It's commented out here and can be used if ROM space becomes
; too tight, otherwise just use the inline code below to set the parameters.
;
;                PHX                     ;Save X register (3)
;                LDX     #$04            ;Set Index count for 4 (2)
;PARM_XFER_LP
;                LDA     LBA_XFER_CNT-1,X        ;Get the parameters (4)
;                STA     IDE_SCT_CNT-1,X ;Store to IDE registers (5)
;                DEX                     ;Decrement count (2)
;                BNE     PARM_XFER_LP    ;Loop back till done (2/3)
;                PLX                     ;Restore X register (4)
;
; Fastest code to transfer parameters to working memory!
;
                LDA     LBA_EXT_BYTE    ;Set LBA bits 23-16 (3)
                STA     IDE_CYL_HIGH    ;Send to IDE (4)
                LDA     LBA_HIGH_BYTE   ;Set LBA bits 15-8 (3)
                STA     IDE_CYL_LOW     ;Send to IDE (4)
                LDA     LBA_LOW_BYTE    ;Get LBA bits 7-0 (3)
                STA     IDE_SCT_NUM     ;Send to IDE (4)
                LDA     LBA_XFER_CNT    ;Get Block count to read (3)
                STA     IDE_SCT_CNT     ;Send to IDE (4)
;
IDE_SET_PARMS2                          ;Set partial parameters (non LBA xfer commands)
;
                LDA     #%11100000      ;Set Drive 0, LBA mode, LBA bits 27-24 as 0 (2)
                STA     IDE_DRV_HEAD    ;Send to IDE controller (4)
;
                LDA     LBA_ADDR_LOW    ;Setup buffer address (3)
                STA     BIOS_XFERL      ;Store low byte (3)
                LDA     LBA_ADDR_HIGH   ;Block Buffer Address (3)
                STA     BIOS_XFERH      ;Store high byte (3)
                LDA     LBA_XFER_CNT    ;Get Block count to read (3)
                STA     BIOS_XFERC      ;Set BIOS Block count to Xfer (3)
                STZ     IDE_STATUS_RAM  ;Clear RAM Status Register, ISR updates it (3)
                RTS                     ;Return to caller (6)
;
TST_IDE_RDY
;
;Test for IDE Controller Ready
; This routine tests that the IDE Controller is ready and can accept a command for execution.
; There are two bits in the status to qualify this:
; Bit 6 is for Ready and bit 4 is for Seek Complete. Both should be active to qualify the
; drive as being ready (per Hitachi Microdrive documentation).
; Note: It's also possible that bit 0 might be set, which indicates an error condition.
; If an error has occurred, we should test for this as well, and set the carry flag to
; ensure proper drive sensing.
;
                LDA     IDE_ALT_STATUS  ;Get IDE Alternate Status register (4)
                CMP     #$51            ;Test for Ready and Error bits on (2)
                BEQ     TST_IDE_ERR     ;If yes, branch to exit (2/3)
                CMP     #$50            ;Test for Ready bits on (2)
                BNE     TST_IDE_RDY     ;If not, loop back until ready (2/3)
                CLC                     ;Safety to ensure Carry is not set (2)
                RTS                     ;Return to Caller (6)
TST_IDE_ERR     SEC                     ;Set Carry to indicate Error bit set (2)
                RTS                     ;Return to Caller (6)
;
;**************************************************************************************************
;Delay Routines: SET_DLY sets up the MSDELAY value and also sets the 16-bit Long Delay
; On entry, A Reg = 10-millisecond count, X Reg = High multiplier, Y Reg = Low multiplier
; these values are used by the EXE_MSDLY and EXE_LGDLY routines. Minimum delay is 10ms
; values for MSDELAY are $00-$FF ($00 = 256 times)
; values for Long Delay are $0000-$FFFF (0-65535 times MSDELAY)
; longest delay is 65,535*256*10ms = 16,776,960 * 0.01 = 167,769.60 seconds
;
;NOTE: All delay execution routines preserve registers (EXE_MSDLY, EXE_LGDLY, EXE_XLDLY)
;
SET_DLY         STA     SETMS           ;Save Millisecond count (3)
                STY     DELLO           ;Save Low multiplier (3)
                STX     DELHI           ;Save High multiplier (3)
                RTS                     ;Return to caller (6)
;
;EXE MSDELAY routine is the core delay routine. It sets the MSDELAY count value from the
; SETMS variable, enables the MATCH flag, then waits for the MATCH flag to clear.
;
EXE_MSDLY       PHA                     ;Save A Reg (3)
                SMB7    MATCH           ;Set MATCH flag bit (5)
                LDA     SETMS           ;Get delay seed value (3)
                STA     MSDELAY         ;Set MS delay value (3)
;
MATCH_LP        BBS7    MATCH,MATCH_LP  ;Test MATCH flag, loop until cleared (5,6)
                PLA                     ;Restore A Reg (4)
                RTS                     ;Return to caller (6)
;
;EXE LONG Delay routine is the 16-bit multiplier for the MSDELAY routine.
; It loads the 16-bit count from DELLO/DELHI, then loops the MSDELAY routine
; until the 16-bit count is decremented to zero.
;
EXE_LGDLY       PHX                     ;Save X Reg (3)
                PHY                     ;Save Y Reg (3)
                LDX     DELHI           ;Get high byte count (3)
                INX                     ;Increment by one (checks for $00 vs $FF) (2)
                LDY     DELLO           ;Get low byte count (3)
                BEQ     SKP_DLL         ;If zero, skip to high count (2/3)
DO_DLL          JSR     EXE_MSDLY       ;Call millisecond delay (6)
                DEY                     ;Decrement low count (2)
                BNE     DO_DLL          ;Branch back until done (2/3)
;
SKP_DLL         DEX                     ;Decrement high byte index (2)
                BNE     DO_DLL          ;Loop back to D0_DLL (will run 256 times) (2/3)
                PLY                     ;Restore Y Reg (4)
                PLX                     ;Restore X Reg (4)
                RTS                     ;Return to caller (6)
;
;**************************************************************************************************
;COUNTER BENCHMARK TIMING ROUTINES
; To enable a level of benchmarking, three routines are part of C02BIOS version 4.0x
; Using the existing 10ms Jiffy Clock, three bytes of Page zero are used to hold variables;
; MS10_CNT - a 10ms count variable for 0.01 resolution of timing - resets at 100 counts (1 second)
; SECL_CNT - a low byte seconds count
; SECH_CNT - a high byte seconds count
; This provides up to 65,535.99 seconds of timing with 0.01 seconds resolution
; - NOTE: the count variables reset to zero after 65,535.99 seconds!
;
;CNT_INIT is used to zero the timing pointers and start the benchmark timer
;CNT_STRT is used to start the timing by setting bit 6 of the MATCH flag
;CNT_STOP is used to stop the timing by clearing bit 6 of the MATCH flag
; the interrupt handler for the DUART timer increments the timing variables when bit 6 of the
; MATCH flag is active.
;
CNT_INIT        RMB6    MATCH           ;Clear bit 6 of MATCH flag, ensure timing is disabled (5)
                STZ     MS10_CNT        ;Zero 10ms timing count (3)
                STZ     SECL_CNT        ;Zero low byte of seconds timing count (3)
                STZ     SECH_CNT        ;Zero high byte of seconds timing count (3)
;
CNT_STRT        SMB6    MATCH           ;Set bit 6 of MATCH flag to enable timing (5)
                RTS                     ;Return to caller (6)
;
CNT_STOP        RMB6    MATCH           ;Clear bit 6 of MATCH flag to disable timing (5)
                RTS                     ;Return to caller (6)
;
;**************************************************************************************************
;START of Realtime Clock Routines to access NVRAM                                                 *
;**************************************************************************************************
;
;RTC Routines to Read and Write Non-Volatile RAM - 256 Bytes
; To use either routine, the starting memory address needs to be
; loaded into the A/Y registers. A reg = low byte, Y reg = high byte
;
RTC_NVRD        JSR     RTC_NVSET       ;Setup for transfer (6)
RTC_RD_LOOP     LDA     RTC_RAM_DATA    ;Get NVRAM Data (4)
                STA     (BIOS_XFERL),Y  ;Save into RAM (6)
                INY                     ;Increment Y Index (2)
                BNE     RTC_RD_LOOP     ;Loop back reading NVRAM (2/3)
                BRA     CLEAR_BMI       ;Clear Burst Mode, exit (3)
;
RTC_NVWR        JSR     RTC_NVSET       ;Setup for transfer (6)
RTC_WR_LOOP     LDA     (BIOS_XFERL),Y  ;Get RAM Data (5)
                STA     RTC_RAM_DATA    ;Write to NVRAM (4)
                INY                     ;Increment Y Index (2)
                BNE     RTC_WR_LOOP     ;Loop back writing NVRAM (2/3)
CLEAR_BMI       LDA     #%00100000      ;Get Burst Mode Increment bit (2)
                TRB     RTC_CONTROL_B   ;Clear Burst Mode for NVRAM (6)
                RTS                     ;Return to caller (6)
;
RTC_NVSET       STA     BIOS_XFERL      ;Save Low Address location (3)
                STY     BIOS_XFERH      ;Save High Address location (3)
                LDA     #%00100000      ;Get Burst Mode Increment bit (2)
                TSB     RTC_CONTROL_B   ;Set Burst Mode for NVRAM (6)
                STZ     RTC_RAM_ADDR    ;Set NVRAM Address to Zero (4)
                LDY     #$00            ;Zero Y reg - Index (2)
                RTS                     ;Return to caller (6)
;
;**************************************************************************************************
;Initializing the SC28L92 DUART as a Console.
;An anomaly in the W65C02 processor requires a different approach in programming the SC28L92
; for proper setup/operation. The SC28L92 uses three Mode Registers which are accessed at the same
; register in sequence. There is a command that Resets the Mode Register pointer (to MR0) that is
; issued first. Then MR0/1/2 are loaded in sequence. The problem with the W65C02 is a false read of
; the register when using indexed addressing (i.e., STA UART_REGISTER,X). This results in the Mode
; Register pointer being moved to the next register, so the write to next MRx never happens. While
; the indexed list works fine for all other register functions/commands, the loading of the
; Mode Registers need to be handled separately.
;
;NOTE: the W65C02 will function normally "if" a page boundary is crossed as part of the STA
; (i.e., STA $FDFF,X) where the value of the X Register is high enough to cross the page boundary.
; Programming in this manner would be confusing and require modification if the base I/O address
; is changed for a different hardware I/O map.
;
;There are two routines called to setup the 28L92 DUART:
;
;The first routine is a RESET of the DUART.
; It issues the following sequence of commands:
;  1- Reset Break Change Interrupts
;  2- Reset Receivers
;  3- Reset Transmitters
;  4- Reset All errors
;
;The second routine initializes the 28L92 DUART for operation. It uses two tables of data; one for
; the register offset and the other for the register data. The table for register offsets is
; maintained in ROM. The table for register data is copied to page $03, making it soft data. If
; needed, operating parameters can be altered and the DUART re-initialized via the ROM routine.
;
; Note: A hardware reset will reset the SC28L92 and the default ROM config will be initialized.
; Also note that the Panic routine invoked by a NMI trigger will also reset the DUART to the
; default ROM config.
;
INIT_IO         JSR     RESET_28L92     ;Reset of SC28L92 DUART (both channels) (6)
                LDA     #DF_TICKS       ;Get divider for jiffy clock (100x10ms = 1 second) (2)
                STA     TICKS           ;Preload TICK count (3)
;
;This routine sets the initial operating mode of the DUART
;
INIT_28L92      SEI                     ;Disable interrupts (2)
;
                LDX     #INIT_DUART_E-INIT_DUART ;Get the Init byte count (2)
28L92_INT       LDA     LOAD_28L92-1,X  ;Get Data for 28L92 Register (4)
                LDY     INIT_OFFSET-1,X ;Get Offset for 28L92 Register (4)
                STA     SC28L92_BASE,Y  ;Store Data to selected register (5)
                DEX                     ;Decrement count (2)
                BNE     28L92_INT       ;Loop back until all registers are loaded (2/3)
;
; Mode Registers are NOT reset to MR0 by above INIT_28L92!
; The following resets the MR pointers for both channels, then sets the MR registers
; for each channel. Note: the MR index is incremented to the next location after the write.
; NOTE: These writes can NOT be done via indexed addressing modes!
;
                LDA     #%10110000      ;Get mask for MR0 Reset (2)
                STA     UART_COMMAND_A  ;Reset Pointer for Port A (4)
                STA     UART_COMMAND_B  ;Reset Pointer for Port B (4)
;
                LDX     #$03            ;Set index for 3 bytes to xfer (2)
MR_LD_LP        LDA     LOAD_28L92+15,X ;Get MR data for Port A (4)
                STA     UART_MODEREG_A  ;Send to 28L92 Port A (4)
                LDA     LOAD_28L92+18,X ;Get MR data for Port B (4)
                STA     UART_MODEREG_B  ;Send to 28L92 Port B (4)
                DEX                     ;Decrement index to next data (2)
                BNE     MR_LD_LP        ;Branch back till done (2/3)
;
                CLI                     ;Enable interrupts (2)
;
; Start Counter/Timer
;
                LDA     UART_START_CNT  ;Read register to start counter/timer (4)
                RTS                     ;Return to caller (6)
;
; This routine does a Reset of the SC28L92
;
RESET_28L92     LDX     #UART_RDATAE-UART_RDATA1 ;Get the Reset commands byte count (2)
UART_RES1       LDA     UART_RDATA1-1,X ;Get Reset commands (4)
                STA     UART_COMMAND_A  ;Send to UART A CR (4)
                STA     UART_COMMAND_B  ;Send to UART B CR (4)
                DEX                     ;Decrement the command list index (2)
                BNE     UART_RES1       ;Loop back until all are sent (2/3)
                RTS                     ;Return to caller (6)
;
;**************************************************************************************************
;START OF PANIC ROUTINE
;The Panic routine is for debug of system problems, i.e., a crash. The hardware design requires a
; debounced NMI trigger button which is manually operated when the system crashes or malfunctions.
;
;User presses the NMI (panic) button. The NMI vectored routine will perform the following tasks:
; 1- Save CPU registers in page zero locations
; 2- Reset the MicroDrive and disable interrupts
; 3- Clear all Console I/O buffer pointers
; 4- Call the ROM routines to init the vectors and config data (page $03)
; 5- Call the ROM routines to reset/init the DUART (SC28L92)
; 6- Enter the Monitor via the warm start vector
;
; Note: The additional hardware detection (RTC/IDE) are NOT executed with the Panic routine!
; The interrupt vectors are restored without including the additional ISR for the IDE controller.
;
; Note: no memory is cleared except the required pointers/vectors to restore the system.
;
NMI_VECTOR      SEI                     ;Disable interrupts (2)
                STA     AREG            ;Save A Reg (3)
                STX     XREG            ;Save X Reg (3)
                STY     YREG            ;Save Y Reg (3)
                PLA                     ;Get Processor Status (4)
                STA     PREG            ;Save in PROCESSOR STATUS preset/result (3)
                TSX                     ;Get Stack pointer (4)
                STX     SREG            ;Save STACK POINTER (3)
                PLA                     ;Pull RETURN address from STACK (4)
                STA     PCL             ;Store Low byte (3)
                PLA                     ;Pull high byte (4)
                STA     PCH             ;Store High byte (3)
;
                LDA     #%00000110      ;Get mask for MicroDrive Reset/IRQ disable (2)
                STA     IDE_DEV_CTRL    ;Send to MicroDrive (4)
;
                STZ     UART_IMR        ;Disable ALL interrupts from UART (4)
;
                LDX     #$0C            ;Set count for 12 (2)
PAN_LP1         STZ     ICNT_A-1,X      ;Clear DUART I/O pointers (3)
                DEX                     ;Decrement index (2)
                BNE     PAN_LP1         ;Branch back till done (2/3)
;
                JSR     INIT_PG03       ;Xfer default Vectors/HW Config to $0300 (6)
                JSR     INIT_IO         ;Reset and Init the UART for Console (6)
;
                LDA     #%00000010      ;Get mask for MicroDrive Reset off (2)
                STA     IDE_DEV_CTRL    ;Send to MicroDrive (4)
;
DO_NMI0         JMP     (NMIRTVEC0)     ;Jump to NMI Return Vector (Monitor Warm Start) (6)
;
;**************************************************************************************************
;
;BRK/IRQ Interrupt service routines
;The pre-process routine located in page $FF soft-vectors to INTERUPT0/BRKINSTR0 below
;       These are the routines that handle BRK and IRQ functions
;       The BRK handler saves CPU details for register display
;       - A Monitor can provide a disassembly of the last executed instruction
;       - A Received Break is also handled here (ExtraPutty/Windows or Serial/OSX)
;
; SC28L92 handler
;       The 28L92 IRQ routine handles Transmit, Receive, Timer and Received-Break interrupts
;       - Transmit and Receive each have a 128 byte circular FIFO buffer in memory per channel
;       - Xmit IRQ is controlled (On/Off) by the handler and the CHROUT(2) routine
;
; The 28L92 Timer resolution is 10ms and used as a Jiffy Clock for RTC, delays and benchmarking
;
;**************************************************************************************************
;
;BIOS routines to handle interrupt-driven I/O for the SC28L92
;NOTE: IP0 Pin is used for RTS, which is automatically handled in the chip. As a result,
; the upper 2 bits of the ISR are not used in the handler. The Lower 5 bits are used, but
; the lower two are used to determine when to disable transmit after the buffer is empty.
;
;The DUART_ISR bits are defined as follows:

; Bit7          ;Input Change Interrupt
; Bit6          ;Change Break B Interrupt
; Bit5          ;RxRDY B Interrupt
; Bit4          ;TxRDY B Interrupt
; Bit3          ;Counter Ready Interrupt
; Bit2          ;Change Break A Interrupt
; Bit1          ;RxRDY A Interrupt
; Bit0          ;TxRDY A Interrupt
;
; SC8L92 uses all bits in the Status Register!
; - for Receive Buffer full, we set a bit in the SC28L92 Misc. Register, one for each Port.
; Note that the Misc. Register in the SC28L92 is a free byte for storing the flags, as it's
; not used when the DUART is configured in Intel mode! Freebie Register for us to use ;-)
;
; BOTE: The entry point for the BRK/IRQ handler is below at label INTERUPT0
;
;**************************************************************************************************
;
;ISR Routines for SC28L92 Port B
;
; The operation is the same as Port A below, sans the fact that the Break detection only resets
; the DUART channel and returns, while Port A uses Break detection for other functions within
; the BIOS structure, and processes the BRK routine shown further down.
;
UARTB_RCV       LDY     ICNT_B          ;Get input buffer count (3)
                BMI     BUFFUL_B        ;Check against limit ($80), branch if full (2/3)
;
UARTB_RCVLP     LDA     UART_STATUS_B   ;Get Status Register (4)
                BIT     #%00000001      ;Check RxRDY active (2)
                BEQ     UARTB_CXMT      ;If RxRDY not set, FIFO is empty, check Xmit (2/3)

                LDA     UART_RECEIVE_B  ;Else, get data from 28L92 (4)
                LDY     ITAIL_B         ;Get the tail pointer to buffer (3)
                STA     IBUF_B,Y        ;Store into buffer (5)
                INC     ITAIL_B         ;Increment tail pointer (5)
                RMB7    ITAIL_B         ;Strip off bit 7, 128 bytes only (5)
                INC     ICNT_B          ;increment data count (5)
                BPL     UARTB_RCVLP     ;If input buffer not full, check for more FIFO data (2/3)
;
UARTB_CXMT      LDA     UART_ISR        ;Get 28L92 ISR Reg (4)
                BIT     #%00010000      ;Check for Xmit B active (2)
                BEQ     REGEXT_B        ;Exit if inactive (2/3)
;
; To take advantage of the onboard FIFO, we test the TxRDY bit in the Status Register.
; If the bit is set, then there is more room in the FIFO. The ISR routine here will
; attempt to fill the FIFO from the Output Buffer. This saves processing time in the
; ISR itself.
;
UARTB_XMT       LDA     OCNT_B          ;Get output buffer count, any data to xmit? (3)
                BEQ     NODATA_B        ;If zero, no data left, turn off xmit (2/3)
;
UARTB_XMTLP     LDA     UART_STATUS_B   ;Get Status Register (4)
                BIT     #%00000100      ;Check TxRDY active (2)
                BEQ     REGEXT_B        ;If TxRDY not set, FIFO is full, exit ISR (2/3)
;
                LDY     OHEAD_B         ;Get the head pointer to buffer (3)
                LDA     OBUF_B,Y        ;Get the next data (4)
                STA     UART_TRANSMIT_B ;Send the data to 28L92 (4)
                INC     OHEAD_B         ;Increment head pointer (5)
                RMB7    OHEAD_B         ;Strip off bit 7, 128 bytes only (5)
                DEC     OCNT_B          ;Decrement counter (5)
                BNE     UARTB_XMTLP     ;If more data, loop back to send it (2/3)
;
;No more buffer data to send, check SC28L92 TxEMT and disable transmit if empty.
; Note: If the TxEMT bit is set, then the FIFO is empty and all data has been sent.
;
NODATA_B        LDY     #%00001000      ;Else, get mask for xmit off (2)
                STY     UART_COMMAND_B  ;Turn off xmit (4)
REGEXT_B        JMP     (IRQRTVEC0)     ;Return to Exit/ROM IRQ handler (6)
;
BUFFUL_B        LDY     #%00010000      ;Get Mask for Buffer full (2)
                STY     UART_MISC       ;Save into 28L92 Misc. Register (4)
                BRA     REGEXT_B        ;Exit IRQ handler (3)
;
;Received Break handler for Port B
;
UARTB_BRK       LDA     UART_STATUS_B   ;Get DUART Status Register (4)
                BMI     BREAKEY_B       ;If bit 7 set, received Break was detected (2/3)
;
; If a received Break was not the cause, we should reset the DUART Port as the cause
; could have been a receiver error, i.e., parity or framing
;
                LDX     #UART_RDATAE-UART_RDATA ;Get index count (2)
UARTB_RST1      LDA     UART_RDATA-1,X  ;Get Reset commands (4)
                STA     UART_COMMAND_B  ;Send to DUART CR (4)
                DEX                     ;Decrement the command list (2)
                BNE     UARTB_RST1      ;Loop back until all are sent (2/3)
                BRA     REGEXT_B        ;Exit (3)
;
; A received Break was the cause. Just reset the receiver and return.
;
BREAKEY_B       LDA     #%01000000      ;Get Reset Received Break command (2)
                STA     UART_COMMAND_B  ;Send to DUART to reset (4)
                LDA     #%01010000      ;Get Reset Break Interrupt command (2)
                STA     UART_COMMAND_B  ;Send to DUART to reset (4)
                BRA     REGEXT_B        ;Exit (3)
;
;**************************************************************************************************
;
;This is the IRQ handler entry point for the SC28L92 DUART.
; This is the first IRQ handler unless an IDE device is found during cold start.
; By default, it will take 25 clock cycles to arrive here after an interrupt is
; generated. If an IDE device is present, the IDE handler will be processed
; first. If no IDE interrupt is active, it will take an additional 33 cycles to
; arrive here.
;
; C02BIOS 4.02 has re-arranged the interrupt handler for the SC28L92 DUART.
; - The second port is checked first for active data, as it could be used for a
; - high-speed transfer from another device. The first port is used for the
; - console (which can also be used for data transfer) and is checked second.
; - The Counter/Timer is checked first, to maintain benchmark and delay accuracy.
;
INTERUPT0                               ;Interrupt 0 to handle the SC28L92 DUART
                LDA     UART_ISR        ;Get the UART Interrupt Status Register (4)
                BEQ     REGEXT_0        ;If no bits are set, exit handler (2/3)
;
                BIT     #%00001000      ;Test for Counter ready (RTC) (2)
                BNE     UART_RTC        ;If yes, go increment RTC variables (2/3)
;
                BIT     #%01000000      ;Test for Break on B (2)
                BNE     UARTB_BRK       ;If yes, Reset the DUART receiver (2/3)
;
                BIT     #%00100000      ;Test for RHR B having data (2)
                BNE     UARTB_RCV       ;If yes, put the data in the buffer (2/3)
;
                BIT     #%00010000      ;Test for THR B ready to receive data (2)
                BNE     UARTB_XMT       ;If yes, get data from the buffer (2/3)
;
                BIT     #%00000100      ;Test for Break on A (2)
                BNE     UARTA_BRK       ;If yes, Reset the DUART receiver (2/3)
;
                BIT     #%00000010      ;Test for RHR A having data (2)
                BNE     UARTA_RCV       ;If yes, put the data in the buffer (2/3)
;
                BIT     #%00000001      ;Test for THR A ready to receive data (2)
                BNE     UARTA_XMT       ;If yes, get data from the buffer (2/3)
;
; if none of the above bits caused the IRQ, the only bit left is the change input port.
; just save it in the temp IRT register in page zero and exit.
;
                STA     UART_IRT        ;Save the 28L92 ISR for later use (3)
REGEXT_0        JMP     (IRQRTVEC0)     ;Return to Exit/ROM IRQ handler (6)
;
UART_RTC        JMP     UART_RTC0       ;Jump to RTC handler (3)
;
;**************************************************************************************************
;
;ISR Routines for SC28L92 Port A
;
; The Receive Buffer is checked first to ensure there is open space in the buffer.
; By loadng the input count, bit7 will be set if it is full, which will set the "N"
; flag in the CPU status register. If this is the case, we exit to BUFFUL_A and set
; a bit the SC28L92 Misc. Register. If the buffer has space, we continue.
; 
; To take advantage of the onboard FIFO, we test the RxRDY bit in the Status Register.
; If the bit is set, the FIFO has data and the routine moves data from the FIFO into
; the Receive buffer. We loop back and contnue moving data from the FIFO to the buffer
; until the RxRDY bit is cleared (FIFO empty). If the FIFO is empty, we branch and
; check for a pending Transmit interrupt, just to save some ISR time.
;
; NOTE: the receiver is configured to use the Watchdog function. This will generate a
; receiver interrupt within 64 bit times once data is received (and the FIFO has not
; reached it's configured fill level). This provides the required operation for use
; as a console, as single character commands are common and would not fill the FIFO,
; which generates an interrupt based on the configured FIFO fill level.
;
UARTA_RCV       LDY     ICNT_A          ;Get input buffer count (3)
                BMI     BUFFUL_A        ;Check against limit ($80), branch if full (2/3)
;
UARTA_RCVLP     LDA     UART_STATUS_A   ;Get Status Register (4)
                BIT     #%00000001      ;Check RxRDY active (2)
                BEQ     UARTA_CXMT      ;If RxRDY not set, FIFO is empty, check Xmit (2/3)

                LDA     UART_RECEIVE_A  ;Else, get data from 28L92 (4)
                LDY     ITAIL_A         ;Get the tail pointer to buffer (3)
                STA     IBUF_A,Y        ;Store into buffer (5)
                INC     ITAIL_A         ;Increment tail pointer (5)
                RMB7    ITAIL_A         ;Strip off bit 7, 128 bytes only (5)
                INC     ICNT_A          ;Increment input bufffer count (5)
                BPL     UARTA_RCVLP     ;If input buffer not full, check for more FIFO data (2/3)
;
UARTA_CXMT      LDA     UART_ISR        ;Get 28L92 ISR Reg (4)
                BIT     #%00000001      ;Check for Xmit A active (2)
                BEQ     REGEXT_A        ;Exit if inactive, else drop into Xmit code (2/3)
;
;To take advantage of the onboard FIFO, we test the TxRDY bit in the Status Register.
; If the bit is set, then there is more room in the FIFO. The ISR routine here will
; attempt to fill the FIFO from the Output Buffer. This saves processing time in the
; ISR itself.
;
UARTA_XMT       LDA     OCNT_A          ;Get output buffer count, any data to xmit? (3)
                BEQ     NODATA_A        ;If zero, no data left, turn off xmit (2/3)
;
UARTA_XMTLP     LDA     UART_STATUS_A   ;Get Status Register (4)
                BIT     #%00000100      ;Check TxRDY active (2)
                BEQ     REGEXT_A        ;If TxRDY not set, FIFO is full, exit ISR (2/3)
;
                LDY     OHEAD_A         ;Get the head pointer to buffer (3)
                LDA     OBUF_A,Y        ;Get the next data (4)
                STA     UART_TRANSMIT_A ;Send the data to 28L92 (4)
                INC     OHEAD_A         ;Increment head pointer (5)
                RMB7    OHEAD_A         ;Strip off bit 7, 128 bytes only (5)
                DEC     OCNT_A          ;Decrement output buffer count (5)
                BNE     UARTA_XMTLP     ;If more data, loop back to send it (2/3)
;
;No more buffer data to send, check SC28L92 TxEMT and disable transmit if empty.
; Note: If the TxEMT bit is set, then the FIFO is empty and all data has been sent.
;
NODATA_A        LDY     #%00001000      ;Else, get mask for xmit off (2)
                STY     UART_COMMAND_A  ;Turn off xmit (4)
REGEXT_A        JMP     (IRQRTVEC0)     ;Return to Exit/ROM IRQ handler (6)
;
BUFFUL_A        LDY     #%00000001      ;Get Mask for Buffer full (2)
                STY     UART_MISC       ;Save into 28L92 Misc. Register (4)
                BRA     REGEXT_A        ;Exit IRQ handler (3)
;
;Received Break handler for Port A
;
UARTA_BRK       LDA     UART_STATUS_A   ;Get DUART Status Register (4)
                BMI     BREAKEY_A       ;If bit 7 set, received Break was detected (2/3)
;
; If a received Break was not the cause, we should reset the DUART Port as the cause
; could have been a receiver error, i.e., parity or framing
;
                LDX     #UART_RDATAE-UART_RDATA ;Get index count (2)
UARTA_RST1      LDA     UART_RDATA-1,X  ;Get Reset commands (4)
                STA     UART_COMMAND_A  ;Send to DUART CR (4)
                DEX                     ;Decrement the command list (2)
                BNE     UARTA_RST1      ;Loop back until all are sent (2/3)
                BRA     REGEXT_A        ;Exit (3)
;
; A received Break was the cause. Reset the receiver and process the BRK routine.
;
BREAKEY_A       LDA     #%01000000      ;Get Reset Received Break command (2)
                STA     UART_COMMAND_A  ;Send to DUART to reset (4)
                LDA     #%01010000      ;Get Reset Break Interrupt command (2)
                STA     UART_COMMAND_A  ;Send to DUART to reset (4)
;
BREAKEY         CLI                     ;Enable IRQ, drop into BRK handler (2)
;
;**************************************************************************************************
;
; BRK Vector defaults to here
;
BRKINSTR0       PLY                     ;Restore Y Reg (4)
                PLX                     ;Restore X Reg (4)
                PLA                     ;Restore A Reg (4)
                STA     AREG            ;Save A Reg (3)
                STX     XREG            ;Save X Reg (3)
                STY     YREG            ;Save Y Reg (3)
                PLA                     ;Get Processor Status (4)
                STA     PREG            ;Save in PROCESSOR STATUS preset/result (3)
                TSX                     ;Xfer STACK pointer to X Reg (2)
                STX     SREG            ;Save STACK pointer (3)
;
                PLX                     ;Pull Low RETURN address from STACK then save it (4)
                STX     PCL             ;Store program counter Low byte (3)
                STX     INDEXL          ;Seed Indexl for DIS_LINE (3)
                PLY                     ;Pull High RETURN address from STACK then save it (4)
                STY     PCH             ;Store program counter High byte (3)
                STY     INDEXH          ;Seed Indexh for DIS_LINE (3)
                BBR4    PREG,DO_NULL    ;Check for BRK bit set (5,6)
;
; The following three subroutines are contained in the base C02 Monitor code. These calls
; do a register display and disassembles the line of code that caused the BRK to occur
;
                JSR     M_PRSTAT1       ;Display CPU status (6)
                JSR     M_DECINDEX      ;Decrement Index to BRK ID Byte (6)
                JSR     M_DECINDEX      ;Decrement Index to BRK instruction (6)
                JSR     M_DIS_LINE      ;Disassemble BRK instruction (6)
;
; Note: This routine only clears Port A, as it is used for the Console
;
DO_NULL         LDA     #$00            ;Clear all Processor Status Register bits (2)
                PHA                     ;Push it to Stack (3)
                PLP                     ;Pull it to Processor Status (4)
                STZ     ITAIL_A         ;Clear input buffer pointers (3)
                STZ     IHEAD_A         ; (3)
                STZ     ICNT_A          ; (3)
                JMP     (BRKRTVEC0)     ;Done BRK service process, re-enter monitor (6)
;
;**************************************************************************************************
;
;Entry for ISR to service the timer/counter interrupt.
;
; NOTE: Stop timer cmd resets the interrupt flag, counter continues to generate interrupts.
; NOTE: 38 clock cycles to here from INTERUPT0 - 68 in total
;
UART_RTC0       LDA     UART_STOP_CNT   ;Get Command mask for stop timer (4)
;
; Check the MATCH flag bit7 to see if a Delay is active. If yes, decrement the MSDELAY
; variable once each pass until it is zero, then clear the MATCH flag bit7
;
                BBR7    MATCH,SKIP_DLY  ;Skip Delay if bit7 is clear (5,6)
                DEC     MSDELAY         ;Decrement Millisecond delay variable (5)
                BNE     SKIP_DLY        ;If not zero, skip (2/3)
                RMB7    MATCH           ;Else clear MATCH flag (5)
;
; Check the MATCH flag bit6 to see if Benchmarking is active. If yes, increment the
; variables once each pass until the MATCH flag bit6 is inactive.
;
SKIP_DLY        BBR6    MATCH,SKIP_CNT  ;Skip Count if bit6 is clear (5,6)
                INC     MS10_CNT        ;Else, increment 10ms count (5)
                LDA     MS10_CNT        ;Load current value (3)
                CMP     #100            ;Compare for 1 second elapsed time (2)
                BCC     SKIP_CNT        ;If not, skip to RTC update (2/3)
                STZ     MS10_CNT        ;Else, zero 10ms count (3)
                INC     SECL_CNT        ;Increment low byte elapsed seconds (5)
                BNE     SKIP_CNT        ;If no overflow, skip to RTC update (2/3)
                INC     SECH_CNT        ;Else, increment high byte elapsed seconds (5)
;
SKIP_CNT        DEC     TICKS           ;Decrement RTC tick count (5)
                BNE     REGEXT_RTC      ;Exit if not zero (2/3)
                LDA     #DF_TICKS       ;Get default tick count (2)
                STA     TICKS           ;Reset tick count (3)
;
                INC     SECS            ;Increment seconds (5)
                LDA     SECS            ;Load it to A reg (3)
                CMP     #60             ;Check for 60 seconds (2)
                BCC     REGEXT_RTC      ;If not, exit (2/3)
                STZ     SECS            ;Else, reset seconds, inc Minutes (3)
;
                INC     MINS            ;Increment Minutes (5)
                LDA     MINS            ;Load it to A reg (3)
                CMP     #60             ;Check for 60 minutes (2)
                BCC     REGEXT_RTC      ;If not, exit (2/3)
                STZ     MINS            ;Else, reset Minutes, inc Hours (3)
;
                INC     HOURS           ;Increment Hours (5)
                LDA     HOURS           ;Load it to A reg (3)
                CMP     #24             ;Check for 24 hours (2)
                BCC     REGEXT_RTC      ;If not, exit (2/3)
                STZ     HOURS           ;Else, reset hours, inc Days (3)
;
;This is the tricky part ;-)
; One variable holds the Day of the week and the Date of the Month!
; First, update the Day of the Week, which is the upper 3 bits of the variable
; Valid days are 1 to 7. Mask off the upper 3 bits, and add #%00100000 to it,
; if the result is zero, it was #%11100000, so start over by making the Day
; #%00100000, then save it to RTC_TEMP variable.
;
;Once that's done, load the variable again, mask off the Date and increase by
; one, then check against days of the month, update as required and check for
; Leap year and February 29th stuff. When all updated, OR in the Day from the
; RTC_TEMP variable and finish updating the DAY_DATE variable.
;
                LDA     DAY_DATE        ;Get Day and Date variable (3)
                AND     #%11100000      ;Mask off for Day of Week (1-7) (2)
                CLC                     ;Clear carry for add (2)
                ADC     #%00100000      ;Add effective "1" to Day of week (2)
                BNE     NO_DAY_ADD      ;If non-zero, don't reset to "1" (2/3)
                LDA     #%00100000      ;Else, reset Day to "1" (2)
NO_DAY_ADD      STA     RTC_TEMP        ;Store the updated Day into temp (3)
;
;Get the Month and Year variable, move the upper 4-bits down to get the
; current Month. Xfer it the X reg, then get the Date, increment by one
; and check against the number of days in that month.
;
                LDA     MONTH_CENTURY   ;Get Month and Year variable (3)
                LSR     A               ;Shift Month to lower 4 bits (2)
                LSR     A               ; (2)
                LSR     A               ; (2)
                LSR     A               ; (2)
                TAX                     ;Move to X reg (2)
                LDA     DAY_DATE        ;Get Day and Date variable (3)
                AND     #%00011111      ;Mask off for Date of Month (1-31) (2)
                INC     A               ;Increment by one (2)
                CMP     MAX_DATE-1,X    ;Check for Max Day per Month+1 (4)
                BCS     MONTH_ADD       ;Branch if we need to update the Month (2/3)
DO_29           ORA     RTC_TEMP        ;Else OR in updated Day to updated Date (3)
                STA     DAY_DATE        ;Update Day and Date variable (3)
REGEXT_RTC      JMP     (IRQRTVEC0)     ;Then exit IRQ handler (6)
;
MONTH_ADD       CPX     #$02            ;Check for Month = February (2)
                BNE     MONTH_INC       ;If not, increment Month (2/3)
                LDA     YEAR            ;Else, Get current year low byte (3)
                AND     #%00000011      ;Mask off lower 2 bits (2)
                BNE     MONTH_INC       ;If not a Leap Year, continue on (2/3)
                LDA     DAY_DATE        ;Get Day and Date variable (3)
                AND     #%00011111      :Mask off Date (2)
                INC     A               ;Increment by one (2)
                CMP     #30             ;Check for 29th+1 Day for Leap Year (2)
                BCC     DO_29           ;Save Date as 29th and exit IRQ handler (2/3)
;
MONTH_INC       LDA     RTC_TEMP        ;Get updated Day (Date is effective zero) (3)
                ORA     #%00000001      ;OR in the 1st Day of the Month (2)
                STA     DAY_DATE        ;Save updated Day and Date of the Month (3)
;
                LDA     MONTH_CENTURY   ;Get Month and Year variable (3)
                CLC                     ;Clear Carry for add (2)
                ADC     #$10            ;Add "1" to Month (upper 4 bits) (2)
                STA     RTC_TEMP        ;Save it to work temp (3)
                AND     #%11110000      ;Mask off Century (lower 4 bits) (2)
                CMP     #$D0            ;Check for "13" (December + 1) (2)
                BCS     YEAR_ADD        ;If 13 go add to YEAR (2/3)
                LDA     RTC_TEMP        ;Else, Get updated Month and Century (3)
                STA     MONTH_CENTURY   ;Save it (3)
                BRA     REGEXT_RTC      ;Exit IRQ Handler (3)
;
YEAR_ADD        LDA     MONTH_CENTURY   ;Get Month and Century (3)
                AND     #%00001111      ;Mask off old month (2)
                ORA     #%00010000      ;OR in $10 for January (2)
                STA     MONTH_CENTURY   ;Save updated Month and existing upper 4 bits (3)
                INC     YEAR            ;Increment Year low byte (0-255) (5)
                BNE     REGEXT_RTC      ;If no rollover, exit ISR (2/3)
                LDA     MONTH_CENTURY   ;Get Month and Year variable (3)
                TAX                     ;Save to X reg (2)
                AND     #%11110000      ;Mask off upper 4-bits for year (2)
                STA     RTC_TEMP        ;Save it in the temp area (3)
                TXA                     ;Get the Month and Year back (2)
                AND     #%00001111      ;Mask off the month (2)
                CLC                     ;Clear carry for add (2)
                ADC     #$01            ;Add 1 to upper 4 bits (2)
                ORA     RTC_TEMP        ;OR in the Month (3)
                STA     MONTH_CENTURY   ;Update Month and Century variable (3)
                BRA     REGEXT_RTC      ;If no rollover, then exit IRQ handler (3)
;
;**************************************************************************************************
;
;Core routines that are used to detect and configure additional I/O devices.
; The I/O adapter supported by the 4.0x Release of C02BIOS contains two I/O devices:
; - A Maxim DS15x1 Realtime Clock
; - An IDE Device, i.e., IBM/Hitachi MicroDrive
;
; The first routine is to detect the DS15x1 RTC. This is done by reading the NVRAM section
; and testing for the Signature at the end of NVRAM. Obviously, this is something that needs
; to be setup before it can be detected. There is a separate utility that is used to configure
; the RTC for Time/Date, NVRAM usage and the two-byte signature. This utility must be run first
; to properly configure the RTC. Once completed, the BIOS will detect the RTC and read the
; Date and Time to set the BIOS variables accordingly.
;
; The second routine is to detect the IDE device. This can be a bit tricky...
; The first step is to load the status register and check it's contents. If there is no device
; attached, the contents will be a "phantom" I/O address, which is $FE.
; If this happens, simply bypass any additional testing and setup.
; If the contents are other than the "phantom" I/O address, we take additional steps to sense
; the IDE Controller, run Diagnostics, initialize it and add it's ISR into the chain.
;
;**************************************************************************************************
;
;This routine detects the DS15x1 RTC.
; While there's really no standard method to detect the RTC, the NVRAM is initialized
; during the configuration for Date, Time, etc. The last two bytes of the NVRAM will
; contain a 2-byte signature of "KM", in honor of the author ;-)
; If the signature is found, the INIT_RTC routine is called, which will setup the
; RTC variables in Page Zero, where the current Date and Time will be maintained.
;
DETECT_RTC
                LDX     #$FF            ;Load NVRAM Offset (2)
                STX     RTC_RAM_ADDR    ;Set index to 2nd byte of signature (4)
                LDA     RTC_RAM_DATA    ;Get NVRAM Data (4)
                CMP     #"M"            ;Check for "M" (2)
                BNE     SET_EPOCH       ;If not found, set EPOCH as default (2/3)
                DEC     RTC_RAM_ADDR    ;Decrement index to 1st signature byte (5)
                LDA     RTC_RAM_DATA    ;Get NVRAM Data (4)
                CMP     #"K"            ;Check for "K" (2)
                BEQ     FOUND_RTC       ;If good, go Init RTC and return (2/3)
;
;If RTC not found, preload Date variables as EPOCH time (Thursday, 1st January, 1970)
; Note: all Time variables default to zero from a cold start.
;
SET_EPOCH
                LDX     #$03            ;Get Index of 3 (2)
EPOCH_LP        LDA     EPOCH-1,X       ;Get Preload data (4)
                STA     DAY_DATE-1,X    ;Store in RTC variables (4)
                DEX                     ;Decrement Index (2)
                BNE     EPOCH_LP        ;Loop back until done (2/3)
                RTS                     ;Return, no RTC found (6)
;
FOUND_RTC
                INX                     ;Increment Index ($FF -> $00) (2)
                LDA     RTC_MSG,X       ;Get BIOS init msg (4)
                BEQ     INIT_RTC        ;If zero, msg done, go Init RTC (2/3)
                JSR     CHROUT          ;Send to console (6)
                BRA     FOUND_RTC       ;Loop back until done (3)
;
;This routine reads the BCD registers from the DS15x1 RTC, converts BCD to Binary and loads the
; BIOS RTC variables. Note that some of the variables are shared to conserve Page Zero space.
; Note: Buffer area used for init is also used by C02 Monitor for hex input and code conversion,
; but is initialized as needed before usage, so we can clobber it here when configuring the BIOS.
;
;As there is a period of time required to get the data from the RTC, convert from BCD, then format
; into the Page Zero locations used, we need to manage the existing Timer/Counter status to ensure
; the best accuracy in time once the routine finishes. In short, the best we can manage accuracy
; is within one second, as the RTC internal update of the registers we read are halted.
;
;To help minimize the timing transfer, we first set the BIOS tick count to it's default value
; to ensure that the software RTC values are not updated during loading from the hardware RTC.
;
; The time to detect and load the current time/date is less than 5000 clock cycles. However, the
; overall accuracy can only be within one second. After the RTC values are transferred, the
; software RTC tick count will not have reached zero, as the entire timing is less than 1ms to
; to read the RTC, convert the BCD data and load the software clock variable in Page Zero. This
; results in software RTC timing starting a 1 second countdown from when the RTC is detected.
; - Note: A Coldstart wouldn't need to reset the Tick Count, but this routine can also be called
;         via the BIOS JMP table, so we reset it here as a safety.
;
INIT_RTC
                LDX     #DF_TICKS       ;Get BIOS default Tick count (2)
                STX     TICKS           ;Reset the Tick count (3)
                LDX     #$00            ;Set X reg to zero for indexing below (2)
                LDA     #%10000000      ;Get TE Bit mask (2)
                TRB     RTC_CONTROL_B   ;Turn off TE Bit to disable update (6)
;
RTC_LOAD_LOOP
                LDA     RTC_SECONDS,X   ;Get Data from RTC (4)
                STA     BUFF_PG0,X      ;Store into RAM (4)
                INX                     ;Increment register count (2)
                CPX     #$08            ;Check for all 8 moved (2)
                BNE     RTC_LOAD_LOOP   :Loop back until all registers are read (2/3)
;
                LDA     #%10000000      ;Get TE Bit mask (2)
                TSB     RTC_CONTROL_B   ;Turn on TE Bit to enable update (6)
;
;Now convert BCD to Binary (X reg = $08)
;
BCD_LOOP        LDA     BUFF_PG0-1,X    ;Get BCD Data from Buffer (4)
;
                TAY                     ;Save BCD value (2)
                AND     #$F0            ;Mask for high nibble (2)
                LSR     A               ;Shift right (/2) (2)
                STA     RTC_TEMP        ;Save in temp (3)
                LSR     A               ;Shift over (/4) (2)
                LSR     A               ;Shift over (/8) -Carry is clear (2)
                ADC     RTC_TEMP        ;Add in temp (3)
                STA     RTC_TEMP        ;Store it back (3)
                TYA                     ;Get BCD back (2)
                AND     #$0F            ;Mask for low nibble (2)
                ADC     RTC_TEMP        ;Add in temp (upper converted nibble) (3)
;
                STA     BUFF_PG0-1,X    ;Save Binary Data back to Buffer (4)
                DEX                     ;Decrement Index (2)
                BNE     BCD_LOOP        ;Loop back until done (2/3)
;
;Now take the binary data for the RTC, and format it for the BIOS RTC variables:
; Seconds, Minutes and Hours are fine as they are, so they simply move over.
; The Day (of the week) and the Date (of the Month) are combined into a single variable.
; Note: Day (of the week) is variable and decided by the user. In honor of my past, I'm
; declaring Saturday as the 1st day of the week, an IBM tradition.
; The Month is also kept in the upper 4 bits of the Century variable.
; Note: The Century and Year are two BCD digits each. As 4 BCD digits, these need to be
; converted to a 16-bit binary integer. Only 12-bits are needed, which frees the upper
; 4-bits to be used for the Month.
;
                LDA     BUFF_PG0+3      ;Get the Day count (3)
                ASL     A               ;Shift to upper 3 bits (2)
                ASL     A               ; (2)
                ASL     A               ; (2)
                ASL     A               ; (2)
                ASL     A               ; (2)
                ORA     BUFF_PG0+4      ;OR in the Date variable (3)
                STA     BUFF_PG0+3      ;Save to the Day variable (3)
;
                LDA     BUFF_PG0+5      ;Get the Month variable (3)
                ASL     A               ;Shift to upper 4 bits (2)
                ASL     A               ; (2)
                ASL     A               ; (2)
                ASL     A               ; (2)
                STA     BUFF_PG0+4      ;Save it (lower nibble = 0) (3)
;
; The easiest way to create the 16-bit Year is to take the high binary digit
; and multiply it by 100, then add the low binary digit. We do the multiply
; by adding it to the 16-bit variable 100 times ;-)
;
                LDX     #100            ;Get the index count for 100 (2)
                STZ     BUFF_PG0+8      ;Zero Temp low byte (3)
                STZ     BUFF_PG0+9      ;Zero Temp high byte (3)
;
RTC_ADD         LDA     BUFF_PG0+7      ;Get Year value (3)
                JSR     ADD_16          ;Go add it... (6)
                DEX                     ;Decrement count (2)
                BNE     RTC_ADD         ;Loop back until done (2/3)
;
                LDA     BUFF_PG0+6      ;Get Year lower digit (3)
                JSR     ADD_16          ;Add it into the Temp (6)
;
                LDA     BUFF_PG0+8      ;Get lower byte for year (3)
                STA     BUFF_PG0+5      ;Save it (3)
                LDA     BUFF_PG0+9      ;Get upper byte for year (3)
                ORA     BUFF_PG0+4      ;OR in Month (upper 4 bits) (3)
                STA     BUFF_PG0+4      ;Save it (3)
;
; Now transfer the buffer contents to the Page Zero RTC variables
;
                LDX     #$06            ;Set count for 6 (2)
RTC_XFER        LDA     BUFF_PG0-1,X    ;Get the buffer data (4)
                STA     SECS-1,X        ;Save to RTC variables (4)
                DEX                     ;Decrement count (2)
                BNE     RTC_XFER        ;Loop back till done (2/3)
                RTS                     ;Return to caller (6)
;
ADD_16          CLC                     ;Clear carry flag (2)
                ADC     BUFF_PG0+8      ;Add to Temp low byte (3)
                STA     BUFF_PG0+8      ;And save it (3)
                LDA     BUFF_PG0+9      ;Get high byte (3)
                ADC     #$00            ;Add carry to Temp high byte (2)
                STA     BUFF_PG0+9      ;And save it (3)
                RTS                     ;Return to caller (6)
;
;**************************************************************************************************
;
;This routine detects the IDE Port
; To detect the IDE controller, it can be a bit tricky. It might take several seconds
; from a physical Reset of the IDE Controller before the Busy flag goes off.
; During this time, any commands sent to the IDE controller will fail. As I like to say,
; "timing is everything". After quite a bit of testing, the easy way to detect the IDE
; controller present is to load the IDE_STATUS register. If an IDE Controller is not
; present, the A Reg will show a phantom address of $FE (high order IDE hardware address)
; and any initialization can be bypassed.
;
; If the IDE controller is present, the IDE_STATUS read may be invalid, so it's necessary
; to test the BUSY flag of the status register. Once the IDE Controller is no longer busy,
; the controller can be initialized. This does create an obvious pause in the startup, but
; ensures that the IDE controller can be reliably detected and initialized at boot time.
;
; A change has been made in the IDE_SETUP routine. As the interrupts were disabled on the
; IDE Controller initially, it needs to be re-enabled before the setup is completed. The short
; bit of code that does this is also called by the Reset-Diag function (JMP $FF00).
;
DETECT_IDE
                LDA     IDE_STATUS      ;Get the IDE Status (4)
                CMP     #$FE            ;Check for an empty (phantom) address (2)
                BNE     IDE_INIT        ;If not #$FE, try to Init the IDE controller (2/3)
NO_IDE          RTS                     ;Return to caller, no IDE controller found (6)
;
;Init the IDE controller
; First, test for the IDE controller ready. If that works, execute the IDE device
; Diagnostics and check for successful completion. If it fails, exit without linking
; the IDE controller into the IRQ chain. Else, link IRQ chain and show message that
; the IDE device is found.
;
IDE_INIT
                LDA     IDE_ALT_STATUS  ;Get IDE Alternate Status register (4)
                BMI     IDE_INIT        ;Loop until BUSY bit is clear (2/3)

                JSR     IDE_DIAG        ;Run the self diagnostic (6)
                CMP     #$50            ;Check for $50 on A reg (drive ready) (2)
                BNE     NO_IDE          ;If not, no IDE present (2/3)
                CPX     #$01            ;X Reg will show #$01 if diags successful (2)
                BNE     NO_IDE          ;If failed, exit (2/3)
;
; IDE Controller found and passed initial self diagnostics test.
; Send IDE Found message to terminal, note: X reg = $01.
;
IDE_MSG_LP      LDA     IDE_MSG-1,X     ;Get BIOS init msg (minus 1 for X reg=1) (4)
                BEQ     IDE_SETUP       ;If zero, msg done, go setup IDE (2/3)
                JSR     CHROUT          ;Send to console (6)
                INX                     ;Increment Index (2)
                BRA     IDE_MSG_LP      ;Loop back until done (3)
;
;IDE Setup
; This will insert the IDE Controller ISR into the Interrupt Handler chain.
;
; First, disable interrupts, capture the current IRQ exit vector address
; and save it to the first Insert Vector. Second, load the IDE ISR routine
; address and store it to the main IRQ exit vector, then re-enable interrupts.
;
; Second, this routine will execute an Identify IDE command to load the Soft
; Config Data for the maximum LBA Count accessible by the current IDE device.
;
; Note: Two routines are below, use only one! They allow a choice to insert
; the IDE ISR before or after the main Interrupt Handler. By default, loading
; is before the main ISR. Despite the high speed of the data transfers, the
; interrupt rate is not that high.
;
IDE_SETUP       SEI                     ;Disable interrupts (2)
;
; To load the IDE ISR Handler BEFORE the existing DUART ISR Handler:
;
                LDA     IRQVEC0         ;Get low byte of current IRQ Exit (4)
                LDY     IRQVEC0+1       ;Get high byte of current IRQ Exit (4)
                STA     VECINSRT0       ;Save low byte of IRQ Exit to insert 0 (4)
                STY     VECINSRT0+1     ;Save high byte of IRQ Exit to insert 0 (4)
;
                LDA     #<INTERUPT1     ;Get low byte of IDE ISR (2)
                LDY     #>INTERUPT1     ;Get high byte of IDE ISR (2)
                STA     IRQVEC0         ;Save low byte of IRQ Exit (4)
                STY     IRQVEC0+1       ;Save high byte of IRQ Exit (4)
;
; To load the IDE ISR Handler AFTER the existing DUART ISR Handler:
;
;                LDA     IRQRTVEC0       ;Get low byte of IRQ Exit
;                LDY     IRQRTVEC0+1     ;Get high byte of IRQ Exit
;                STA     VECINSRT0       ;Save low byte of IRQ Exit
;                STY     VECINSRT0+1     ;Save high byte of IRQ Exit
;
;                LDA     #<INTERUPT1     ;Get low byte of IDE ISR
;                LDY     #>INTERUPT1     ;Get high byte of IDE ISR
;                STA     IRQRTVEC0       ;Save low byte of IRQ Exit
;                STY     IRQRTVEC0+1     ;Save high byte of IRQ Exit
;
                CLI                     ;Enable interrupts (2)
                JSR     IDE_EN_IRQ      ;Enable IDE Controller interrupt (6)
;
; Drop into Identify Drive routine
;
IDE_IDENTIFY                            ;Identify Device
;
; This requests a 512-byte block of data that shows capabilities, CHS (not used), LBA Count, etc.
; The format is similar to Read LBA, except no LBA parameter is required. It effectively works as
; a Read Block operation and the data transferred is handled by the ISR for a Read Block.
; NOTE: The Identify Command is coded to load into LBA_BUFFER (address $0600).
;
                LDA     #<LBA_BUFFER    ;Set Address low byte (2)
                LDY     #>LBA_BUFFER    ;Set Address high byte (2)
                LDX     #$01            ;Set Block count to 1 (2)
                JSR     IDE_SET_ADDRESS ;Set Xfer address and block count (6)
IDENT_WAIT
                LDA     IDE_ALT_STATUS  ;Get IDE Alternate Status register (4)
                BMI     IDENT_WAIT      ;Loop until BUSY bit is clear (2/3)


                JSR     IDE_SET_PARMS2  ;Setup required parameters (no LBA parameter) (6)
;
                LDA     #$EC            ;Get Identify Command (2)
                JSR     IDENT_READ      ;Use READ_LBA routine to finish (6)
;
; Identify data loaded in buffer. Now extract LBA count and store to Soft Config Data for usage
; by access routines (Read/Write/Verify). Four bytes are used and the format from the Identify
; Command are Low-order Word / High-order Word, where each word is in Big Endian. We will store
; the LBA count as Little Endian, Low-order Word / High-order Word.
; The offset from the buffer are Words 60-61 (decimal).
;
; A table is used to index the offset of bytes to move into consecutive soft data.
;
                LDX     #$04            ;Set count for 4 bytes (2)
LBA_SIZE        LDY     LBA_OFFSET-1,X  ;Get Offset to LBA count (4)
                LDA     (LBA_ADDR_LOW),Y        ;Load LBA Data (5)
                STA     LOAD_IDE-1,X    ;Store to Soft Config Data (5)
                DEX                     ;Decrement count (2)
                BNE     LBA_SIZE        ;Loop back until done (2/3)
;
; Enable Write Cache for Microdrive, performance improvement ;-)
IDE_EN_CACHE
                LDA     #$02            ;Get Enable Write Cache Feature (2)
IDE_CACHE_CMD
                STA     IDE_FEATURE     ;Send to IDE controller (4)
                LDA     #%11100000      ;Get Drive 0, LBA. mode, etc. (2)
                STA     IDE_DRV_HEAD    ;Send to IDE controller (4)
                LDA     #$EF            ;Get Set Features Command (2)
                STA     IDE_COMMAND     ;Send Command to set feature (4)
                JSR     TST_IDE_RDY     ;Test for Drive ready (6)
                LDA     IDE_STATUS      ;Get Status (4)
                LDX     IDE_ERROR       ;Get Error (if any) (4)
                RTS                     ;Return to Caller (6)
;
; Disable Write Cache for Microdrive, NO performance improvement;-(
IDE_DIS_CACHE
                LDA     #$82            ;Get Disable Write Cache Feature (2)
                BRA     IDE_CACHE_CMD   ;Finish Command above (3)
;
; Reset IDE Controller and run Diagnostics
; The RECAL routine disables the IRQ function, so the routine to enable the IRQ
; is called, then drops into the get status routine before returning.
;
IDE_RESET                               ;Do a Reset of IDE device
                JSR     IDE_RECAL       ;Call IDE_RESET (set LBA mode) (6)
                JSR     IDE_EN_CACHE    ;Enable Write Cache (6)
                JSR     TST_IDE_RDY     ;Wait until Drive ready (6)
                JSR     IDE_EN_IRQ      ;Re-enable IDE Controller interrupt (6)
;
; Drop into Get Status routine after Diagnostics are run
;
IDE_GET_STATUS                          ;Get Status/Error registers from the IDE controller
;
; This routine gets the current status of the IDE Controller and can be issued at any time.
; It does not rely on any interrupt capability as it's a simple read of the Status and the
; Error registers from the IDE Controller.
;
; Note: This routine should be called whenever an Error has occurred, as it returns the
; contents of the Error Register in the X Register and the contents of the Status Register
; in the A Register.
;
; Details for the Registers are:
;
; Error Register:
;Bit 7 - CRC Error or Bad Block error
;Bit 6 - Uncorrectable Data Error
;Bit 5 - 0 (not used) MC (used for Removable-Media drives)
;Bit 4 - ID Not Found
;Bit 3 - 0 (not used) MCR (used for Removable-Media drives)
;Bit 2 - Aborted Command error
;Bit 1 - Track Zero not found error
;Bit 0 - Data Address Mark Not Found
;
; Status Register:
;Bit 7 - Busy - IDE Controller is Busy (all other bits invalid)
;Bit 6 - Drive Ready (IDE Controller Ready to accept Commands)
;Bit 5 - Drive Write Fault - Write Fault error has occurred
;Bit 4 - Drive Seek Complete - is active when the drive is not seeking
;Bit 3 - Data Request - bit set when the IDE Controller has Data to transfer (R/W)
;Bit 2 - Correctable Data - bit set when bad data was found and corrected (ECC)
;Bit 1 - Index - bit toggled from 0 to 1 once per disk revolution
;Bit 0 - Error - bit set when previous command ended with some sort of error
;
                LDA     IDE_ALT_STATUS  ;Get IDE Alternate Status register (4)
                BMI     IDE_GET_STATUS  ;Loop until BUSY bit is clear (2/3)

                LDA     IDE_STATUS      ;Get IDE Status Register (4)
                LDX     IDE_ERROR       ;Get IDE Error Register (4)
                RTS                     ;Return to Caller (6)
;
IDE_DIAG                                ;Run internal Diagnostics on the IDE controller
;
; This is a basic self test within the IDE controller.
; This runs some internal tests for the IDE controller and returns with drive ready bits
; active ($50) and the error register as $01 if successful.
; For Diagnostics, the Error Register contains unique codes as follows:
;
;01h - No error Detected
;02h - Formatter device error
;03h - Sector Buffer error
;04h - ECC Circuitry error
;05h - Controller Microprocessor error
;8xH - Device 1 failed (not valid with a single drive system)
;       Note: 80h OR’ed in for the Slave Drive, lower bit definitions are the same!
;
; To send this command, a common routine is used to save ROM space.
;
                LDA     #$90            ;Get Diagnostic Command (2)
                BRA     IDE_SEND_CMD    ;Branch and send Command to IDE (3)
;
IDE_RECAL                               ;Recalibrate Command
;
;This is the Recalibrate Command ($1x). Upon issue the IDE controller will move the heads to
; Cylinder 0 and read Head 0, Sector 1. If unsuccessful, an error will be posted.
;
                LDA     #$10            ;Get Recalibrate Command (2)
;
; Drop into Send Command routine
;
IDE_SEND_CMD                            ;Send a Command to the IDE controller
;
;Accepts a Command code via the A reg and sets up the necessary IDE Controller
; registers to accept it. It also tests to ensure the controller is ready
; to accept the command and get the Status and Error registers on return.
;
; NOTE: this routine turns off the interrupt capability as it is called
; during initial setup, where the interrupt handler has not been setup yet.
; A separate routine is called to enable the interrupt capability.
;
                SEI                     ;Disable Interrupts (2)
                TAX                     ;Save Command to X Reg (2)
                JSR     TST_IDE_RDY     ;Wait for IDE to be ready (6)
                LDA     #%00001010      ;Get Mask to disable IRQ (2)
                STA     IDE_DEV_CTRL    ;Send to control register (4)
                LDA     #%11100000      ;Get Select Mask (LBA Mode, Drive 0) (2)
                STA     IDE_DRV_HEAD    ;Select Drive 0 (4)
;
                STX     IDE_COMMAND     ;Send command to IDE (4)
SEND_CMD_LP
                LDA     IDE_ALT_STATUS  ;Get IDE Alternate Status register (4)
                BMI     SEND_CMD_LP     ;Loop until BUSY bit is clear (2/3)
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
