coleeau/VMC/Software/3rd Party Software/CO2-Pocket-SBC-2.5-main/Software/ROM Code/Monitor/C02Monitor4.asm

;**************************************************************************************************
;*   C02Monitor 4.02 - Release version for Pocket SBC  (c)2013-2023 by Kevin E. Maier 15/02/2023  *
;*                                                                                                *
;*  Monitor Functions are divided into groups as follows:                                         *
;*   1. Memory Operations:                                                                        *
;*      - Fill Memory: Source, Length, Value (prompts for commit)                                 *
;*      - Move Memory: Source, Target, Length (prompts for commit)                                *
;*      - Compare Memory: Source, Target, Length                                                  *
;*      - Examine/Edit: Address, Data (edit) sequential memory                                    *
;*      - Input ASCII Text into memory: Address, Data (ESC quits)                                 *
;*      - Hex Data Search: Hex data up to 16 bytes                                                *
;*      - Text String Search: ASCII data up to 16 characters                                      *
;*      - Display Memory as Hex/ASCII: Address start - 256 consecutive bytes displayed            *
;*      - Execute from Memory: Start address                                                      *
;*                                                                                                *
;*   2. Register Operations:                                                                      *
;*      - Display All Registers                                                                   *
;*      - Display/Edit A, X, Y, (S)tack Pointer, (P)rocessor Status                               *
;*                                                                                                *
;*   3. Timer/Counter Functions:                                                                  *
;*      - Set delay time: 8-bit 10-millisecond count and 16-bit multiplier count                  *
;*      - Execute Millisecond Delay 1-256 times 10ms (Jiffy Clock)                                *
;*      - Execute Millisecond Delay times 16-bit multiplier count (0-65535)                       *
;*      - RTC function based on 10ms Jiffy Clock: Ticks, Seconds, Minutes, Hours, Date            *
;*      - Benchmark timing up to 65535.99 seconds with 10ms resolution                            *
;*                                                                                                *
;*   4. Keyboard Macro Facility:                                                                  *
;*      - Provides up to 127 byte keyboard buffer loop capability                                 *
;*      - Optional 16-bit Loop Counter (1-65,535)                                                 *
;*      - Send Break command (from Terminal program) exits Macro function                         *
;*                                                                                                *
;*   5. Control-Key Functions:                                                                    *
;*      - CTRL-A: Starts Assembler for simple code entry based on Mnemonics (not completed yet)   *
;*      - CTRL-B: Starts Rich Leary's DOS/65 ROM Version 3                                        *
;*      - CTRL-D: Table-Driven Disassembler - Supports Full WDC Opcodes/Addressing modes          *
;*      - CTRL-E: Edit single byte in the EEPROM - uses BurnByte routine to ensure proper write   *
;*      - CTRL-L: Xmodem Loader w/CRC-16 Support, auto detect S19 Records from WDC Linker         *
;*      - CTRL-P: Program EEPROM - Source, Target, Length (Source must be RAM based)              *
;*      - CTRL-Q: Query Commands - Shows all available Monitor functions                          *
;*      - CTRL-R: Reset System - Initiates Cold Start of BIOS and Monitor                         *
;*      - CTRL-S: Xmodem Save w/CRC-16 Support                                                    *
;*      - CTRL-T: Date and Time - values loaded during boot from RTC                              *
;*      - CTRL-V: Shows Version for BIOS and Monitor                                              *
;*      - CTRL-Z: Zeros out ALL RAM and initiates Cold Start of BIOS and Monitor                  *
;*                                                                                                *
;*   6. Panic Button (NMI Support Routine in C02BIOS)                                             *
;*      - Re-initializes Vector and Configuration Data in Page $03                                *
;*      - Clears Console Buffer pointers in Page $00 and restarts Console only                    *
;**************************************************************************************************
        PL      66      ;Page Length
        PW      132     ;Page Width (# of char/line)
        CHIP    W65C02S ;Enable WDC 65C02 instructions
        PASS1   OFF     ;Set ON for debugging
        INCLIST ON      ;Set ON for listing Include files
;**************************************************************************************************
; Page Zero definitions $00 to $9F reserved for user routines
; NOTES:- Locations $00 and $01 are used to zero RAM (calls CPU reset)
;       - EEPROM Byte Write routine loaded into Page Zero at $88-$9C
;       - Enhanced Basic uses locations $00 - $85
;**************************************************************************************************
;
; This BIOS and Monitor version also use a common source file for constants and variables used by
; both. This just simplifies keeping both code pieces in sync.
;
        INCLUDE         C02Constants4.asm
;
;**************************************************************************************************
;
; Note: No code changes, just updated version and date to mimic the recent BIOS changes/updates.
;
; The Assembler is not yet implemented.... but there is some initial development code included.
; - this does some pre-processing and then JUMPs to $0800 to the current development code.
; - Needless to say, don't get excited thinking it works... sorry ;-)
;
; Note: The hardware configuration has been changed to increase the available RAM in the system!
;       This change (PLD reconfig) results in 56KB of RAM and reduced EEPROM to 8KB. This is done
;       to provide a larger TEA for the bootable RAM version of DOS/65. This change results in the
;       code to write to the EEPROM insitu no longer working. This is due to the unlock sequence
;       needed, as it requires a minimum of 22KB addressable memory space. For now, any EEPROM
;       changes required must be done by using a programmer.
;**************************************************************************************************
;The following 32 functions are provided by BIOS via the JMP Table below
; $FF48 is Reserved for future expansion (1 available)
;
; $FF00 IDE_RES_DIAG    ;Reset IDE and Run Diagnostics
; $FF03 IDE_GET_STATUS  ;Get IDE Status and Extended Error codes
; $FF06 IDE_IDENTIFY    ;Get IDE Identification Block
; $FF09 IDE_READ_LBA    ;Read a Block from IDE device
; $FF0C IDE_WRITE_LBA   ;Write a Block to IDE device
; $FF0F IDE_VERIFY_LBA  ;Verify the last Block from IDE device
; $FF12 IDE_SET_LBA     ;Set the LBA Block ID for Read/Write/Verify
; $FF15 IDE_SET_ADDRESS ;Set the Memory Address to transfer Block data to/from
; $FF18 IDE_EN_CACHE    ;Enable the Write Cache on IDE controller
; $FF1B IDE_DIS_CACHE   ;Disable the Write Cache on IDE controller
;
; $FF1E RTC_NVRD        ;Read the NVRAM from the RTC
; $FF21 RTC_NVWR        ;Write the NVRAM to the RTC
; $FF24 RTC_INIT        ;Initialize the Software RTC from the hardware RTC
;
; $FF27 CHRIN2          ;Data input from serial port (Port B)
; $FF2A CHROUT2         ;Data output to serial port (Port B)
;
; $FF2D CNT_INIT        ;Reset counters and Start Benchmark Counter
; $FF30 CNT_STRT        ;Start Benchmark Counter
; $FF33 CNT_STOP        ;Stop Benchmark Counter
;
; $FF36 CHRIN_NW        ;Data input from console, no waiting, clear carry if none
; $FF39 CHRIN           ;Data input from console, carry set if data
; $FF3C CHROUT          ;Data output to console, sent data preserved
;
; $FF3F SET_DLY         ;Set delay value for milliseconds and 16-bit counter
; $FF42 EXE_MSDLY       ;Execute millisecond delay 1-256 * 10 milliseconds
; $FF45 EXE_LGDLY       ;Execute long delay; millisecond delay * 16-bit count
;
; $FF48 Reserved        ;Reserved BIOS call for future expansion
;
; $FF4B INIT_VEC        ;Initialize soft vectors at $0300 from ROM
; $FF4E INIT_CFG        ;Initialize soft config values at $0320 from ROM
; $FF51 INIT_28L92      ;Initialize SC28L92 console 115.2K, 8-N-1 RTS/CTS
; $FF54 RESET_28L92     ;Reset SC28L92 - called before INIT_28L92
;
; $FF57 MON_WARM        ;Monitor warm start - jumps to page $03
; $FF5A MON_COLD        ;Monitor cold start - jumps to page $03
; $FF5D COLDSTRT        ;System cold start - RESET vector for 65C02
;
;**************************************************************************************************
;BIOS JUMP Table starts here:
;       - BIOS calls are listed below - total of 32
;       - Reserved calls are for future hardware support
;
B_IDE_RESET             .EQU    $FF00   ;Call 00
B_IDE_GET_STAT          .EQU    $FF03   ;Call 01
B_IDE_IDENTIFY          .EQU    $FF06   ;Call 02
B_IDE_READ_LBA          .EQU    $FF09   ;Call 03
B_IDE_WRITE_LBA         .EQU    $FF0C   ;Call 04
B_IDE_VERFY_LBA         .EQU    $FF0F   ;Call 05
B_IDE_SET_LBA           .EQU    $FF12   ;Call 06
B_IDE_SET_ADDR          .EQU    $FF15   ;Call 07
B_IDE_EN_CACHE          .EQU    $FF18   ;Call 08
B_IDE_DIS_CACHE         .EQU    $FF1B   ;Call 09
;
B_RTC_NVRD              .EQU    $FF1E   ;Call 10
B_RTC_NVWR              .EQU    $FF21   ;Call 11
B_RTC_INIT              .EQU    $FF24   ;Call 12
;
B_CHRIN2                .EQU    $FF27   ;Call 13
B_CHROUT2               .EQU    $FF2A   ;Call 14
;
B_CNT_INIT              .EQU    $FF2D   ;Call 15
B_CNT_STRT              .EQU    $FF30   ;Call 16
B_CNT_STOP              .EQU    $FF33   ;Call 17
;
B_CHRIN_NW              .EQU    $FF36   ;Call 18
B_CHRIN                 .EQU    $FF39   ;Call 19
B_CHROUT                .EQU    $FF3C   ;Call 20
;
B_SET_DLY               .EQU    $FF3F   ;Call 21
B_EXE_MSDLY             .EQU    $FF42   ;Call 22
B_EXE_LGDLY             .EQU    $FF45   ;Call 23
;
B_RESERVE               .EQU    $FF48   ;Call 24
;
B_INIT_VEC              .EQU    $FF4B   ;Call 25
B_INIT_CFG              .EQU    $FF4E   ;Call 26
B_INIT_28L92            .EQU    $FF51   ;Call 27
B_RESET_28L92           .EQU    $FF54   ;Call 28
;
B_WRMMNVEC0             .EQU    $FF57   ;Call 29
B_CLDMNVEC0             .EQU    $FF5A   ;Call 30
B_COLDSTRT              .EQU    $FF5D   ;Call 31
;
BIOS_MSG                .EQU    $FFD0   ;BIOS Startup Message is hard-coded here
;**************************************************************************************************
        .ORG $E000                      ;6KB reserved for Monitor ($E000 through $F7FF)
;**************************************************************************************************
;Monitor JUMP Table starts here:
;       - Monitor calls are listed below - total of 32
;       - Reserved calls are for future Monitor functions
;
M_COLD_MON      JMP     COLD_MON        ;Call 00 $E000
M_WARM_MON      JMP     WARM_MON        ;Call 01 $E003
;
M_RESERVE2      JMP     RESERVED        ;Call 02 $E006
;
M_MOVE_RAM      JMP     MOVER+3         ;Call 03 $E009
M_FILL_LP       JMP     FILL_LP         ;Call 04 $E00C
M_BSOUT         JMP     BSOUT           ;Call 05 $E00F
M_XMDM_SAVE     JMP     XMDM_SAVE       ;Call 06 $E012
M_XMDM_LOAD     JMP     XMDM_LOAD       ;Call 07 $E015
M_BENCH         JMP     BENCH           ;Call 08 $E018
M_QUITB         JMP     QUITB           ;Call 09 $E01B
M_TIME          JMP     TIME            ;Call 10 $E01E
M_PRSTAT1       JMP     PRSTAT1         ;Call 11 $E021
M_DIS_LINE      JMP     DIS_LINE        ;Call 12 $E024
M_INCINDEX      JMP     INCINDEX        ;Call 13 $E027
M_DECINDEX      JMP     DECINDEX        ;Call 14 $E02A
M_RDLINE        JMP     RDLINE          ;Call 15 $E02D
M_RDCHAR        JMP     RDCHAR          ;Call 16 $E030
M_HEXIN2        JMP     HEXIN2          ;Call 17 $E033
M_HEXIN4        JMP     HEXIN4          ;Call 18 $E036
M_HEX2ASC       JMP     HEX2ASC         ;Call 19 $E039
M_BIN2ASC       JMP     BIN2ASC         ;Call 20 $E03C
M_ASC2BIN       JMP     ASC2BIN         ;Call 21 $E03F
M_BEEP          JMP     BEEP            ;Call 22 $E042
M_DOLLAR        JMP     DOLLAR          ;Call 23 $E045
M_CROUT         JMP     CROUT           ;Call 24 $E048
M_SPC           JMP     SPC             ;Call 25 $E04B
M_PRBYTE        JMP     PRBYTE          ;Call 26 $E04E
M_PRWORD        JMP     PRWORD          ;Call 27 $E051
M_PRASC         JMP     PRASC           ;Call 28 $E054
M_PROMPT        JMP     PROMPT          ;Call 29 $E057
M_PROMPTR       JMP     PROMPTR         ;Call 30 $E05A
M_CONTINUE      JMP     CONTINUE        ;Call 31 $E05D
;
;START OF MONITOR CODE
;**************************************************************************************************
;*                      This is the Monitor Cold start vector                                     *
;**************************************************************************************************
COLD_MON        LDA     #$15            ;Get version msg
                JSR     PROMPT          ;Send to Console
                LDA     #$14            ;Get intro msg / BEEP
                JSR     PROMPT          ;Send to Console
;
;**************************************************************************************************
;*                              Command input loop                                                *
;**************************************************************************************************
;*                      This is the Monitor Warm start vector                                     *
;**************************************************************************************************
WARM_MON        LDX     #$FF            ;Initialize Stack pointer
                TXS                     ;Xfer to stack
                RMB7    CMDFLAG         ;Clear bit7 of command flag
                LDA     #$16            ;Get prompt msg
                JSR     PROMPT          ;Send to terminal
;
CMON            JSR     RDCHAR          ;Wait for keystroke (converts to upper-case)
                LDX     #MONTAB-MONCMD-1        ;Get command list count
CMD_LP          CMP     MONCMD,X        ;Compare to command list
                BNE     CMD_DEC         ;Check for next command and loop
                PHA                     ;Save keystroke
                TXA                     ;Xfer Command index to A Reg
                ASL     A               ;Multiply keystroke value by 2 (command offset)
                TAX                     ;Xfer Command offset address to table MONTAB
                PLA                     ;Restore keystroke (some commands send to terminal)
                JSR     DOCMD           ;Call Monitor command processor as a subroutine
                BRA     WARM_MON        ;Command processed, branch / wait for next command
DOCMD           JMP     (MONTAB,X)      ;Execute command from Table
;
CMD_DEC         DEX                     ;Decrement index count
                BPL     CMD_LP          ;If more to check, loop back
                JSR     BEEP            ;Beep for error, not valid command character
                BRA     CMON            ;Branch back and re-enter Monitor
;
;**************************************************************************************************
;*                      Basic Subroutines used by multiple routines                               *
;**************************************************************************************************
;
;ASC2BIN subroutine: Convert 2 ASCII HEX digits to a binary (byte) value
; Enter: A Register = high digit, Y Register = low digit
; Return: A Register = binary value
; Updated routine via Mike Barry... saves 3 bytes, 10 clock cycles
ASC2BIN         STZ     TEMP1           ;Clear TEMP1
                JSR     BINARY          ;Convert high digit to 4-bit nibble
                ASL     A               ;Shift to high nibble
                ASL     A
                ASL     A
                ASL     A
                STA     TEMP1           ;Store it in temp area
                TYA                     ;Get Low digit
;
BINARY          EOR     #$30            ;ASCII -> HEX nibble
                CMP     #$0A            ;Check for result < 10
                BCC     BNOK            ;Branch if 0-9
                SBC     #$67            ;Else subtract for A-F
BNOK            ORA     TEMP1           ;OR into temp value
RESERVED        RTS                     ;Return to caller
;
;BIN2ASC subroutine: Convert single byte to two ASCII HEX digits
; Enter: A Register contains byte value to convert
; Return: A Register = high digit, Y Register = low digit
BIN2ASC         PHA                     ;Save A Reg on stack
                AND     #$0F            ;Mask off high nibble
                JSR     ASCII           ;Convert nibble to ASCII HEX digit
                TAY                     ;Move to Y Reg
                PLA                     ;Get character back from stack
                LSR     A               ;Shift high nibble to lower 4 bits
                LSR     A
                LSR     A
                LSR     A
;
ASCII           CMP     #$0A            ;Check for 10 or less
                BCC     ASCOK           ;Branch if less than 10
                ADC     #$06            ;Add $06+CF ($07) for A-F
ASCOK           ADC     #$30            ;Add $30 for ASCII
                RTS                     ;Return to caller
;
;HEX8ASC - Accepts 8-bit Hexadecimal value (00-99 decimal) and converts to ASCII numeric values.
; A Register contains the single byte value on entry and outputs the two ASCII numeric values.
; leading zero is output as it is used for showing hundredths of a second after a decimal point.
HEX8ASC         LDY     #$FF            ;Load Y Reg with "-1"
                SEC                     ;Set carry for subtraction
HEX8LP1         INY                     ;Increment 10's count (starts at zero)
                SBC     #10             ;Subtract 10 decimal
                BCS     HEX8LP1         ;Branch back if >10
                ADC     #$3A            ;Add the last 10 back plus $30 (ASCII "0")
                PHA                     ;Save 1's count to the Stack
                TYA                     ;Get the 10's count
                CLC                     ;Clear carry for add
                ADC     #$30            ;Add $30 for ASCII digit
                JSR     B_CHROUT        ;Print the first digit (10's)
                PLA                     ;Get 1's count from the Stack
                JMP     B_CHROUT        ;Print the second digit, return
;
;HEX2ASC - Accepts 16-bit Hexadecimal value and converts to an ASCII decimal string. Input is
; via the A and Y Registers and output is up to 5 ASCII digits in DATABUFF. The High Byte is in
; the Y Register and Low Byte is in the A Register. Output data is placed in variable DATABUFF
; and terminated with a null character.
; Note: leading zeros are suppressed. PROMPTR routine is used to print the ASCII decimal value.
; Core routine based on Michael Barry's code. Saves many bytes with two updates/changes ;-)
HEX2ASC         STA     BINVALL         ;Save Low byte
                STY     BINVALH         ;Save High byte
                LDX     #5              ;Get ASCII buffer offset
                STZ     DATABUFF,X      ;Zero last buffer byte for null end
;
CNVERT          LDA     #$00            ;Clear remainder
                LDY     #16             ;Set loop count for 16-bits
;
DVLOOP          CMP     #$05            ;Partial remainder >= 10/2
                BCC     DVLOOP2         ;Branch if less
                SBC     #$05            ;Update partial (carry set)
;
DVLOOP2         ROL     BINVALL         ;Shift carry into dividend
                ROL     BINVALH         ;Which will be quotient
                ROL     A               ;Rotate A Reg
                DEY                     ;Decrement count
                BNE     DVLOOP          ;Branch back until done
                ORA     #$30            ;OR in $30 for ASCII
;
                DEX                     ;Decrement buffer offset
                STA     DATABUFF,X      ;Store digit into buffer
;
                LDA     BINVALL         ;Get the Low byte
                ORA     BINVALH         ;OR in the High byte (check for zero)
                BNE     CNVERT          ;Branch back until done
;
;Conversion is complete, get the string address, add offset, then call prompt routine and return
; note DATABUFF is fixed location in Page 0, carry flag need not be cleared as result can never
; set flag after ADC instruction.
                TXA                     ;Get buffer offset
                ADC     #<DATABUFF      ;Add Low byte address
                LDY     #>DATABUFF      ;Get High byte address
                BRA     PROMPTR         ;Branch to PROMPTR to Print numeric string
;
;PROMPT routine: Send indexed text string to terminal. Index is contained in A Reg.
; String buffer address is stored in variable PROMPTL/PROMPTH.
PROMPT          ASL     A               ;Multiply by two for msg table index
                TAX                     ;Xfer to X Reg - index
                LDA     MSG_TABLE,X     ;Get low byte address
                LDY     MSG_TABLE+1,X   ;Get high byte address
;
;PROMPTR routine: takes message address in Y/A and prints via PROMPT2 routine
PROMPTR         STA     PROMPTL         ;Store low byte
                STY     PROMPTH         ;Store high byte
;
;PROMPT2 routine: prints message at address (PROMPTL) till null character found
PROMPT2         LDA     (PROMPTL)       ;Get string data (5)
                BEQ     HINEXIT         ;If null character, exit (borrowed RTS) (2/3)
                JSR     B_CHROUT        ;Send character to terminal (6)
                INC     PROMPTL         ;Increment low byte index (5)
                BNE     PROMPT2         ;Loop back for next character (2/3)
                INC     PROMPTH         ;Increment high byte index (5)
                BRA     PROMPT2         ;Loop back and continue printing (3)
;
;SETUP subroutine: Request HEX address input from terminal
SETUP           JSR     B_CHROUT        ;Send command keystroke to terminal
                JSR     SPC             ;Send [SPACE] to terminal
                BRA     HEXIN4          ;Request a 0-4 digit HEX address input from terminal
;
;HEX input subroutines: Request 1 to 4 ASCII HEX digits from terminal, then convert digits into
; a binary value. For 1 to 4 digits entered, HEXDATAH and HEXDATAL contain the output.
; Variable BUFIDX will contain the number of digits entered
; HEXIN2 - returns value in A Reg and Y Reg only (Y Reg always $00)
; HEXIN4 - returns values in A Reg, Y Reg and INDEXL/INDEXH
; HEX2 - Prints MSG# in A Reg then calls HEXIN2, HEX4 - Prints MSG# in A Reg then calls HEXIN4
HEX4            JSR     PROMPT          ;Print MSG # from A Reg
HEXIN4          LDX     #$04            ;Set for number of characters allowed
                JSR     HEXINPUT        ;Convert digits
                STY     INDEXH          ;Store to INDEXH
                STA     INDEXL          ;Store to INDEXL
                RTS                     ;Return to caller
;
HEX2            JSR     PROMPT          ;Print MSG # from A Reg
HEXIN2          LDX     #$02            ;Set for number of characters allowed
;
;HEXINPUT subroutine: request 1 to 4 HEX digits from terminal, then convert ASCII HEX to HEX
; minor update from Mike Barry, saves a byte.
; Setup RDLINE subroutine parameters:
HEXINPUT        JSR     DOLLAR          ;Send "$" to console
                JSR     RDLINE          ;Request ASCII HEX input from terminal
                BEQ     HINEXIT         ;Exit if none (Z flag already set)
                STZ     HEXDATAH        ;Clear Upper HEX byte, Lower HEX byte will be updated
                LDY     #$02            ;Set index for 2 bytes
ASCLOOP         PHY                     ;Save it to stack
                LDA     INBUFF-1,X      ;Read ASCII digit from buffer
                TAY                     ;Xfer to Y Reg (LSD)
                DEX                     ;Decrement input count
                BEQ     NO_UPNB         ;Branch if no upper nibble
                LDA     INBUFF-1,X      ;Read ASCII digit from buffer
                BRA     DO_UPNB         ;Branch to include upper nibble
NO_UPNB         LDA     #$30            ;Load ASCII "0" (MSD)
DO_UPNB         JSR     ASC2BIN         ;Convert ASCII digits to binary value
                PLY                     ;Get index from stack
                STA     HEXDATAH-1,Y    ;Write byte to indexed buffer location
                TXA                     ;Check for zero, (no digits left)
                BEQ     HINDONE         ;If not, exit
                DEY                     ;Else, decrement to next byte set
                DEX                     ;Decrement index count
                BNE     ASCLOOP         ;Loop back for next byte
HINDONE         LDY     HEXDATAH        ;Get High Byte
                LDA     HEXDATAL        ;Get Low Byte
                LDX     BUFIDX          ;Get input count (set Z flag)
HINEXIT         RTS                     ;And return to caller
;
;RDLINE subroutine: Store keystrokes into buffer until [RETURN] key is struck
; Used for Hex entry, so only (0-9,A-F) are accepted entries. Lower-case alpha characters
; are converted to upper-case. On entry, X Reg = buffer length. On exit, X Reg = buffer count
; [BACKSPACE] key removes keystrokes from buffer. [ESCAPE] key aborts then re-enters monitor.
RDLINE          STX     BUFLEN          ;Store buffer length
                STZ     BUFIDX          ;Zero buffer index
RDLOOP          JSR     RDCHAR          ;Get character from terminal, convert LC2UC
                CMP     #$1B            ;Check for ESC key
                BEQ     RDNULL          ;If yes, exit back to Monitor
NOTESC          CMP     #$0D            ;Check for C/R
                BEQ     EXITRD          ;Exit if yes
                CMP     #$08            ;Check for Backspace
                BEQ     RDBKSP          ;If yes handle backspace
                CMP     #$30            ;Check for '0' or higher
                BCC     INPERR          ;Branch to error if less than '0'
                CMP     #$47            ;Check for 'G' ('F'+1)
                BCS     INPERR          ;Branch to error if 'G' or higher
                LDX     BUFIDX          ;Get the current buffer index
                CPX     BUFLEN          ;Compare to length for space
                BCC     STRCHR          ;Branch to store in buffer
INPERR          JSR     BEEP            ;Else, error, send Bell to terminal
                BRA     RDLOOP          ;Branch back to RDLOOP
STRCHR          STA     INBUFF,X        ;Store keystroke in buffer
                JSR     B_CHROUT        ;Send keystroke to terminal
                INC     BUFIDX          ;Increment buffer index
                BRA     RDLOOP          ;Branch back to RDLOOP
RDBKSP          LDA     BUFIDX          ;Check if buffer is empty
                BEQ     INPERR          ;Branch if yes
                DEC     BUFIDX          ;Else, decrement buffer index
                JSR     BSOUT           ;Send Backspace to terminal
                BRA     RDLOOP          ;Loop back and continue
EXITRD          LDX     BUFIDX          ;Get keystroke count (Z flag)
                BNE     UCOK            ;If data entered, normal exit
                BBS7    CMDFLAG,UCOK    ;Branch if bit7 of command flag active
RDNULL          JMP     (WRMMNVEC0)     ;Quit to Monitor warm start
;
;RDCHAR subroutine: Waits for a keystroke to be entered.
; if keystroke is a lower-case alphabetical, convert it to upper-case
RDCHAR          JSR     B_CHRIN         ;Request keystroke input from terminal
                CMP     #$61            ;Check for lower case value range
                BCC     UCOK            ;Branch if < $61, control code/upper-case/numeric
                SBC     #$20            ;Subtract $20 to convert to upper case
UCOK            RTS                     ;Character received, return to caller
;
;Routines to update pointers for memory operations. UPD_STL subroutine: Increments Source
; and Target pointers. UPD_TL subroutine: Increments Target pointers only, then drops into
; decrement Length pointer. Used by multiple Memory operation commands.
UPD_STL         INC     SRCL            ;Increment source low byte
                BNE     UPD_TL          ;Check for rollover
                INC     SRCH            ;Increment source high byte
UPD_TL          INC     TGTL            ;Increment target low byte
                BNE     DECLEN          ;Check for rollover
                INC     TGTH            ;Increment target high byte
;
;DECLEN subroutine: decrement 16-bit variable LENL/LENH
DECLEN          LDA     LENL            ;Get length low byte
                BNE     SKP_LENH        ;Test for LENL = zero
                DEC     LENH            ;Else decrement length high byte
SKP_LENH        DEC     LENL            ;Decrement length low byte
                RTS                     ;Return to caller
;
;DECINDEX subroutine: decrement 16 bit variable INDEXL/INDEXH
DECINDEX        LDA     INDEXL          ;Get index low byte
                BNE     SKP_IDXH        ;Test for INDEXL = zero
                DEC     INDEXH          ;Decrement index high byte
SKP_IDXH        DEC     INDEXL          ;Decrement index low byte
                RTS                     ;Return to caller
;
;INCINDEX subroutine: increment 16 bit variable INDEXL/INDEXH
INCINDEX        INC     INDEXL          ;Increment index low byte
                BNE     SKP_IDX         ;If not zero, skip high byte
                INC     INDEXH          ;Increment index high byte
SKP_IDX         RTS                     ;Return to caller
;
;Output routines for formatting, backspace, CR/LF, BEEP, etc.
; all routines preserve the A Reg on exit.
;
;BEEP subroutine: Send ASCII [BELL] to terminal
BEEP            PHA                     ;Save A Reg on Stack
                LDA     #$07            ;Get ASCII [BELL] to terminal
                BRA     SENDIT          ;Branch to send
;
;BSOUT subroutine: send a Backspace to terminal
BSOUT           JSR     BSOUT2          ;Send an ASCII backspace
                JSR     SPC             ;Send space to clear out character
BSOUT2          PHA                     ;Save character in A Reg
                LDA     #$08            ;Send another Backspace to return
BRCHOUT         BRA     SENDIT          ;Branch to send
;
BSOUT3T         JSR     BSOUT2          ;Send a Backspace 3 times
BSOUT2T         JSR     BSOUT2          ;Send a Backspace 2 times
                BRA     BSOUT2          ;Send a Backspace and return
;
;SPC subroutines: Send a Space to terminal 1,2 or 4 times
SPC4            JSR     SPC2            ;Send 4 Spaces to terminal
SPC2            JSR     SPC             ;Send 2 Spaces to terminal
SPC             PHA                     ;Save character in A Reg
                LDA     #$20            ;Get ASCII Space
                BRA     SENDIT          ;Branch to send
;
;DOLLAR subroutine: Send "$" to terminal
DOLLAR          PHA                     ;Save A Reg on STACK
                LDA     #$24            ;Get ASCII "$"
                BRA     SENDIT          ;Branch to send
;
;Send 2 CR/LFs to terminal
CR2             JSR     CROUT           ;Send CR/LF to terminal
;Send CR/LF to terminal
CROUT           PHA                     ;Save A Reg
                LDA     #$0D            ;Get ASCII Return
                JSR     B_CHROUT        ;Send to terminal
                LDA     #$0A            ;Get ASCII Linefeed
SENDIT          JSR     B_CHROUT        ;Send to terminal
                PLA                     ;Restore A Reg
                RTS                     ;Return to caller
;
;GLINE subroutine: Send a horizontal line to console used by memory display only.
GLINE           LDX     #$4F            ;Load index for 79 decimal
                LDA     #$7E            ;Get "~" character
GLINEL          JSR     B_CHROUT        ;Send to terminal (draw a line)
                DEX                     ;Decrement count
                BNE     GLINEL          ;Branch back until done
                RTS                     ;Return to caller
;
;Routines to output 8/16-bit Binary Data and ASCII characters
; PRASC subroutine: Print A-Reg as ASCII (Printable ASCII values = $20 - $7E), else print "."
PRASC           CMP     #$7F            ;Check for first 128
                BCS     PERIOD          ;If = or higher, branch
                CMP     #$20            ;Check for control characters
                BCS     ASCOUT          ;If space or higher, branch and print
PERIOD          LDA     #$2E            ;Else, print a "."
ASCOUT          JMP     B_CHROUT        ;Send byte in A-Reg, then return
;
;PRBYTE subroutine: Converts a single Byte to 2 HEX ASCII characters and sends to console on
; entry, A Reg contains the Byte to convert/send. Register contents are preserved on entry/exit.
PRBYTE          PHA                     ;Save A Register
                PHY                     ;Save Y Register
PRBYT2          JSR     BIN2ASC         ;Convert A Reg to 2 ASCII Hex characters
                JSR     B_CHROUT        ;Print high nibble from A Reg
                TYA                     ;Transfer low nibble to A Reg
                JSR     B_CHROUT        ;Print low nibble from A Reg
                PLY                     ;Restore Y Register
                PLA                     ;Restore A Register
                RTS                     ;Return to caller
;
;PRINDEX subroutine: Prints a $ sign followed by INDEXH/L
PRINDEX         JSR     DOLLAR          ;Print a $ sign
                LDA     INDEXL          ;Get Index Low byte
                LDY     INDEXH          ;Get Index High byte
;
;PRWORD subroutine: Converts a 16-bit word to 4 HEX ASCII characters and sends to console. On
; entry, A Reg contains Low Byte, Y Reg contains High Byte. Registers are preserved on entry/exit.
; NOTE: Routine changed for consistency; A Reg = Low byte, Y Reg = High byte on 2nd May 2020
PRWORD          PHA                     ;Save A Register (Low)
                PHY                     ;Save Y Register (High)
                PHA                     ;Save Low byte again
                TYA                     ;Xfer High byte to A Reg
                JSR     PRBYTE          ;Convert and print one HEX character (00-FF)
                PLA                     ;Get Low byte value
                BRA     PRBYT2          ;Finish up Low Byte and exit
;
;Continue routine: called by commands to confirm execution, when No is confirmed, return address
;is removed from stack and the exit goes back to the Monitor input loop.
;Short version prompts for (Y/N) only.
CONTINUE        LDA     #$00            ;Get msg "cont? (Y/N)" to terminal
                BRA     SH_CONT         ;Branch down
CONTINUE2       LDA     #$01            ;Get short msg "(Y/N)" only
SH_CONT         JSR     PROMPT          ;Send to terminal
TRY_AGN         JSR     RDCHAR          ;Get keystroke from terminal
                CMP     #$59            ;"Y" key?
                BEQ     DOCONT          ;If yes, continue/exit
                CMP     #$4E            ;If "N", quit/exit
                BEQ     DONTCNT         ;Return if not ESC
                JSR     BEEP            ;Send Beep to console
                BRA     TRY_AGN         ;Loop back, try again
DONTCNT         PLA                     ;Else remove return address
                PLA                     ;and discard it
                STZ     CMDFLAG         ;Clear all bits in command flag
DOCONT          RTS                     ;Return
;
;**************************************************************************************************
;*                              Monitor Command Processors                                        *
;**************************************************************************************************
;
;**************************************************************************************************
;*                              Timer/Counter based Monitor functions                             *
;**************************************************************************************************
;
;[,] Delay Setup Routine: This routine gets hex input via the console
;  - first is a hex byte ($00-$FF) for the 10-millisecond count
;  - second is a hex word ($0000-$FFFF) for the delay multiplier
;  - these are stored in variables SETMS, DELLO/DELHI
SET_DELAY       LDA     #$17            ;Get millisecond delay message
                JSR     HEX2            ;Use short cut version for print and input
                STA     SETMS           ;Else store millisecond count in variable
GETMULT         LDA     #$18            ;Get Multiplier message
                JSR     HEX4            ;Use short cut version for print and input
                STA     DELLO           ;Store Low byte
                STY     DELHI           ;Store High byte
                RTS                     ;Return to caller
;
;[B] Benchmark Timer: Starts the benchmark timer.
; This routine displays a message to the console. A (y/n) prompt
; allows exit if required. Else it calls the BIOS routine at $FF30. This routine will
; clear the counters in page zero and enable the benchmark count routine.
; NOTE: The Benchmark counter is handled in BIOS and provides a 16-bit count of seconds
; along with a jiffy count with 10ms accuracy.
;
; The companion Q command quits the Benchmark count and displays the elapsed time as
; xxxxx.xx seconds.
BENCH           LDA     #$29            ;Get message for Bench startup
                JSR     PROMPT          ;Send message to console
                JSR     CONTINUE2       ;Prompt user (y/n)
                JMP     B_CNT_INIT      ;Call BIOS routine to Init and start count, return
;
;[Q] Quit Benchmark timer: Quits the Benchmark timer.
; Benchmark timer is stopped by calling the BIOS routine. Once the Benchmark counter is
; is stopped, the HEX2ASC routine to print the 16-bit seconds count, followed by a period
; and then the HEX8ASC routine prints the hundreds count followed by the "Seconds" message.
QUITB           JSR     B_CNT_STOP      ;Stop Benchmark counter
                LDA     SECL_CNT        ;Get seconds low count
                LDY     SECH_CNT        ;Get seconds high count
                JSR     HEX2ASC         ;Print ASCII number
                JSR     PERIOD          ;Send "." to console
                LDA     MS10_CNT        ;Get hundreds of seconds
                JSR     HEX8ASC         ;Print hundreds of seconds
                LDA     #$48            ;Get message for " Seconds"
                JSR     PROMPT          ;Send to console
                JMP     CROUT           ;Send CR/LF and return
;
;**************************************************************************************************
;*                              Macro functions for testing/looping                               *
;**************************************************************************************************
;
;[(] INIMACRO command: Initialize keystroke input buffer
; initializes buffer head/tail pointers and resets buffer count to zero
; input buffer appears empty so command macro starts at the head of the buffer
INIMACRO        STZ     LPCNTL          ;Zero Loop count low byte
                STZ     LPCNTH          ;Zero Loop count high byte
                RMB6    CMDFLAG         ;Clear Loop Count flag Bit6
;
LP_CNT_FL       LDA     #$20            ;Get Loop Count msg
                JSR     PROMPT          ;Send to console
                LDA     #$01            ;Get short msg "(Y/N)" only
                JSR     PROMPT          ;Send to terminal
                JSR     RDCHAR          ;Get keystroke from terminal
                CMP     #$59            ;"Y" key?
                BEQ     DOLOOPS         ;If yes, set loop flag
                CMP     #$4E            ;"N" key?
                BEQ     NOLOOPS         ;If yes, don't set loop flag
                JSR     BEEP            ;Neither (Y/N) selected, sound bell
                BRA     LP_CNT_FL       ;Branch back, try again
;
DOLOOPS         SMB6    CMDFLAG         ;Set Loop Count flag Bit6
NOLOOPS         STZ     ICNT_A          ;Zero Input buffer count
                STZ     ITAIL_A         ;Zero Input buffer tail pointer
MACINI          STZ     IHEAD_A         ;Zero Input buffer head pointer
DONEFILL        RTS                     ;Return to caller
;
;[)] RUNMACRO command: Run Monitor command macro. This will indicate that there are 128 keystrokes
; in the keystroke input buffer. The Monitor will process these as if they were received from the
; terminal (typed-in by the user). Because the last keystroke stored in the keystroke buffer was
; ")", this will loop continuously. Use [SEND BREAK] to exit Macro
RUNMACRO        LDA     #$7F            ;Get keystroke buffer max length-1
                STA     ITAIL_A         ;Push tail pointer to end
                INC     A               ;Increment to $80 for buffer count (full)
                STA     ICNT_A          ;Make count show as full ($80)
                BBR6    CMDFLAG,NOLP_CNT        ;If Loop flag clear, branch around it
                INC     LPCNTL          ;Increment loops low byte
                BNE     SKP_LPC         ;If not zero, skip high byte
                INC     LPCNTH          ;Increment loops high byte
SKP_LPC         LDA     #$21            ;Get Loops msg
                JSR     PROMPT          ;Send to console
                LDA     LPCNTL          ;Get Loop count low
                LDY     LPCNTH          ;Get Loop count high
                JSR     HEX2ASC         ;Print Loop count
                JSR     CROUT           ;Send C/R to console
NOLP_CNT        BRA     MACINI          ;Zero Head pointer and exit
;
;**************************************************************************************************
;*                      Basic Memory Operations (includes Ctrl-P)                                 *
;**************************************************************************************************
;
;[C] Compare routine: one memory range to another and display any addresses which do not match
;[M] Move routine: uses this section for parameter input, then branches to MOVER below
;[F] Fill routine: uses this section for parameter input but requires a fill byte value
;[CTRL-P] Program EEPROM: uses this section for parameter input and to write the EEPROM
;Uses source, target and length input parameters. Errors in compare are shown in target space.
;
; NOTE: If the PLD memory configuration is changed to increase RAM and decrease EEPROM,
;       the unlock code will not work correctly, as the minimum addressable EEPROM is
;       22KB. This is the case with the current configuration used here... 56KB of RAM
;       and 8KB of EEPROM.
;
FM_INPUT        LDA     #$05            ;Send "val: " to terminal
                JSR     HEX2            ;Use short cut version for print and input
                STA     TEMP2           ;Save fill byte to temp
                JSR     CONTINUE        ;Handle continue prompt
;
;Memory fill routine: parameter gathered below with Move/Fill,
; then a jump to here TEMP2 contains fill byte value
FILL_LP         LDA     LENL            ;Get length low byte
                ORA     LENH            ;OR in length high byte
                BEQ     DONEFILL        ;Exit if zero
                LDA     TEMP2           ;Get fill byte from TEMP2
                STA     (TGTL)          ;Store in target location
                JSR     UPD_TL          ;Update Target/Length pointers
                BRA     FILL_LP         ;Loop back until done
;
; Compare/Move/Fill Memory operations ENTER HERE!!
;
;Compare/Move/Fill memory operations
CPMVFL          STA     TEMP2           ;Save command character
                JSR     B_CHROUT        ;Print command character (C/M/F)
                CMP     #$46            ;Check for F - fill memory
                BNE     PRGE_E          ;If not, continue normal parameter input
                LDA     #$03            ;Get msg " addr:"
                BRA     F_INPUT         ;Branch to handle parameter input
;
;EEPROM write operation ENTERS HERE!!
PROGEE          LDA     #$1B            ;Get PRG_EE msg
                JSR     PROMPT          ;Send to terminal
                STZ     TEMP2           ;Clear (Compare/Fill/Move)/error flag
;
PRGE_E          LDA     #$06            ;Get " src:" msg
                JSR     HEX4            ;Use short cut version for print and get input
                STA     SRCL            ;Else, store source address in variable SRCL,SRCH
                STY     SRCH            ;Store high address
                LDA     #$07            ;Get " tgt:" msg
F_INPUT         JSR     HEX4            ;Use short cut version for print and get input
                STA     TGTL            ;Else, store target address in variable TGTL,TGTH
                STY     TGTH            ;Store high address
                LDA     #$04            ;Get " len:" msg
                JSR     HEX4            ;Use short cut version for print and get input
                STA     LENL            ;ELSE, store length address in variable LENL,LENH
                STY     LENH            ;Store high address
;
; All input parameters for Source, Target and Length entered
                LDA     TEMP2           ;Get Command character
                CMP     #$46            ;Check for fill memory
                BEQ     FM_INPUT        ;Handle the remaining input
                CMP     #$43            ;Test for Compare
                BEQ     COMPLP          ;Branch if yes
                CMP     #$4D            ;Check for Move
                BEQ     MOVER           ;Branch if yes
;
; Command is to Program EEPROM
PROG_EE         LDA     #$1C            ;Get warning msg
                JSR     PROMPT          ;Send to console
                JSR     CONTINUE2       ;Prompt for (Y/N)
;
;Programming of the EEPROM is now confirmed by user. This routine will copy the core move and test
; routine from ROM to RAM, then call COMPLP to write and compare. As I/O can generate interrupts
; which point to ROM routines, all interrupts must be disabled during the program sequence.
;
;Send message to console for writing EEPROM
                LDA     #$1D            ;Get write message
                JSR     PROMPT          ;Send to console
OC_LOOP         LDA     OCNT_A          ;Check output buffer count
                BNE     OC_LOOP         ;Loop back until buffer sent
;
;Xfer byte write code to RAM for execution
                JSR     XFER_BYTE_WRT   ;Xfer byte write code to Page Zero
;
;Wait for 1/2 second for RAM/ROM access to settle
                LDA     #$32            ;Set milliseconds to 50(*10 ms)
                JSR     B_SET_DLY       ;Set Delay parameters
                JSR     B_EXE_MSDLY     ;Call delay for 1/2 second
;
PROG_EEP        SMB7    TEMP2           ;Set EEPROM write active mask
                JSR     COMPLP          ;Call routine to write/compare
                BBR6    TEMP2,PRG_GOOD  ;Skip down if no error
                LDA     #$1F            ;Get Prog failed message
                BRA     BRA_PRMPT       ;Branch to Prompt routine
;
PRG_GOOD        LDA     #$1E            ;Get completed message
BRA_PRMPT       JMP     PROMPT          ;Send to console and exit
;
COMPLP          LDA     LENL            ;Get low byte of length
                ORA     LENH            ;OR in High byte of length
                BEQ     QUITMV          ;If zero, nothing to compare/write
                BBR7    TEMP2,SKP_BURN  ;Skip burn if bit 7 clear
                JSR     BURN_BYTE       ;Else Burn a byte to EEPROM
SKP_BURN        LDA     (SRCL)          ;Load source byte
                CMP     (TGTL)          ;Compare to target byte
                BEQ     CMP_OK          ;If compare is good, continue
;
                SMB6    TEMP2           ;Set bit 6 of TEMP2 flag (compare error)
                JSR     SPC2            ;Send 2 spaces
                JSR     DOLLAR          ;Print $ sign
                LDA     TGTL            ;Get Low byte of address
                LDY     TGTH            ;Get High byte of address
                JSR     PRWORD          ;Print word
                JSR     SPC             ;Add 1 space for formatting
;
CMP_OK          JSR     UPD_STL         ;Update pointers
                BRA     COMPLP          ;Loop back until done
;
;Parameters for move memory entered and validated, now make decision on which direction
; to do the actual move, if overlapping, move from end to start, else from start to end.
MOVER           JSR     CONTINUE        ;Prompt to continue move
                SEC                     ;Set carry flag for subtract
                LDA     TGTL            ;Get target lo byte
                SBC     SRCL            ;Subtract source lo byte
                TAX                     ;Move to X Reg temporarily
                LDA     TGTH            ;Get target hi byte
                SBC     SRCH            ;Subtract source hi byte
                TAY                     ;Move to Y Reg temporarily
                TXA                     ;Xfer lo byte difference to A Reg
                CMP     LENL            ;Compare to lo byte length
                TYA                     ;Xfer hi byte difference to A Reg
                SBC     LENH            ;Subtract length lo byte
                BCC     RIGHT           ;If carry is clear, overwrite condition exists
;
;Move memory block first byte to last byte, no overlap condition
MVNO_LP         LDA     LENL            ;Get length low byte
                ORA     LENH            ;OR in length high byte
                BEQ     QUITMV          ;Exit if zero bytes to move
                LDA     (SRCL)          ;Load source data
                STA     (TGTL)          ;Store as target data
                JSR     UPD_STL         ;Update Source/Target/Length variables
                BRA     MVNO_LP         ;Branch back until length is zero
;
;Move memory block last byte to first byte avoids overwrite in source/target overlap
RIGHT           LDX     LENH            ;Get the length hi byte count
                CLC                     ;Clear carry flag for add
                TXA                     ;Xfer High page to A Reg
                ADC     SRCH            ;Add in source hi byte
                STA     SRCH            ;Store in source hi byte
                CLC                     ;Clear carry for add
                TXA                     ;Xfer High page to A Reg
                ADC     TGTH            ;Add to target hi byte
                STA     TGTH            ;Store to target hi byte
                INX                     ;Increment high page value for use below in loop
                LDY     LENL            ;Get length lo byte
                BEQ     MVPG            ;If zero no partial page to move
                DEY                     ;Else, decrement page byte index
                BEQ     MVPAG           ;If zero, no pages to move
MVPRT           LDA     (SRCL),Y        ;Load source data
                STA     (TGTL),Y        ;Store to target data
                DEY                     ;Decrement index
                BNE      MVPRT          ;Branch back until partial page moved
MVPAG           LDA     (SRCL),Y        ;Load source data
                STA     (TGTL),Y        ;Store to target data
MVPG            DEY                     ;Decrement page count
                DEC     SRCH            ;Decrement source hi page
                DEC     TGTH            ;Decrement target hi page
                DEX                     ;Decrement page count
                BNE     MVPRT           ;Loop back until all pages moved
QUITMV          RTS                     ;Return to caller
;
;Xfer byte write code to RAM for execution
XFER_BYTE_WRT   LDX     #BYTE_WRE-BYTE_WRS+1 ;Get length of byte write code
BYTE_XFER       LDA     BYTE_WRS-1,X    ;Get code
                STA     BURN_BYTE-1,X   ;Write code to RAM
                DEX                     ;Decrement index
                BNE     BYTE_XFER       ;Loop back until done
                RTS                     ;Return to caller
;
;Byte write code for EEPROM.
; Note: AT28BV256 requires an unlock sequence for all write operations.
;  This is different from earlier Atmel EEPROMs (i.e., AT28C256). The
;  sequence must be sent first to unlock the device, then data can be
;  sent for programming. Note that byte writes can be 1 to 64 bytes.
;  The EEPROM is defined in constants for the Offset of the EEPROM in
;  the hardware memory map.
;
; NOTE: If the PLD memory configuration is changed to increase RAM and decrease EEPROM,
;       the unlock code will not work correctly, as the minimum addressable EEPROM is
;       22KB. This is the case with the current configuration used here... 56KB of RAM
;       and 8KB of EEPROM.
;
BYTE_WRS        SEI                     ;Disable interrupts
;
                LDA     #$AA            ;Get code $AA
                STA     EEPROM+$5555    ;Send to EEPROM
                LDA     #$55            ;Get code $55
                STA     EEPROM+$2AAA    ;Send to EEPROM
                LDA     #$A0            ;Get code $A0
                STA     EEPROM+$5555    ;Send to EEPROM
;
                LDA     (SRCL)          ;Get source byte
                STA     (TGTL)          ;Write to target byte
                LDA     (TGTL)          ;Read target byte (EEPROM)
                AND     #%01000000      ;Mask off bit 6 - toggle bit
BYTE_WLP        STA     TEMP3           ;Store in Temp location
                LDA     (TGTL)          ;Read target byte again (EEPROM)
                AND     #%01000000      ;Mask off bit 6 - toggle bit
                CMP     TEMP3           ;Compare to last read (toggles if write mode)
                BNE     BYTE_WLP        ;Branch back if not done
                CLI                     ;Re-enable interrupts
BYTE_WRE        RTS                     ;Return to caller
;
;[D] HEX/TEXT DUMP command:
; Display in HEX followed by TEXT, the contents of 256 consecutive memory addresses
MDUMP           SMB7    CMDFLAG         ;Set bit7 of command flag
                JSR     SETUP           ;Request HEX address input from terminal
                BNE     LINED           ;Branch if new address entered (Z flag updated)
                LDA     TEMP1L          ;Else, point to next consecutive memory page
                STA     INDEXL          ;address saved during last memory dump
                LDA     TEMP1H          ;Xfer high byte of address
                STA     INDEXH          ;Save in pointer
LINED           JSR     DMPGR           ;Send address offsets to terminal
                JSR     GLINE           ;Send horizontal line to terminal
                JSR     CROUT           ;Send CR,LF to terminal
                LDX     #$10            ;Set line count for 16 rows
DLINE           JSR     SPC4            ;Send 4 Spaces to terminal
                JSR     PRINDEX         ;Print INDEX value
                JSR     SPC2            ;Send 2 Spaces to terminal
                LDY     #$00            ;Initialize line byte counter
GETBYT          JSR     SENGBYT         ;Use Search Engine Get Byte (excludes I/O)
                STA     SRCHBUFF,Y      ;Save in Search buffer (16 bytes)
                JSR     PRBYTE          ;Display byte as a HEX value
                JSR     SPC             ;Send Space to terminal
                JSR     INCINDEX        ;Increment Index to next byte location
                INY                     ;Increment index
                CPY     #$10            ;Check for all 16
                BNE     GETBYT          ;Loop back until 16 bytes have been displayed
                JSR     SPC             ;Send a space
                LDY     #$00            ;Reset index for SRCHBUFF
GETBYT2         LDA     SRCHBUFF,Y      ;Get buffered line (16 bytes)
                JSR     PRASC           ;Print ASCII character
                INY                     ;Increment index to next byte
                CPY     #$10            ;Check for 16 bytes
                BNE     GETBYT2         ;Loop back until 16 bytes have been displayed
                JSR     CROUT           ;Else, send CR,LF to terminal
                LDA     INDEXL          ;Get current index low
                STA     TEMP1L          ;Save to temp1 low
                LDA     INDEXH          ;Get current index high
                STA     TEMP1H          ;Save to temp1 high
                DEX                     ;Decrement line count
                BNE     DLINE           ;Branch back until all 16 done
                JSR     GLINE           ;Send horizontal line to terminal
;
;DMPGR subroutine: Send address offsets to terminal
DMPGR           LDA     #$02            ;Get msg for "addr:" to terminal
                JSR     PROMPT          ;Send to terminal
                JSR     SPC2            ;Add two additional spaces
                LDX     #$00            ;Zero index count
MDLOOP          TXA                     ;Send "00" thru "0F", separated by 1 Space, to terminal
                JSR     PRBYTE          ;Print byte value
                JSR     SPC             ;Add a space
                INX                     ;Increment the count
                CPX     #$10            ;Check for 16
                BNE     MDLOOP          ;Loop back until done
;
;Print the ASCII text header "0123456789ABCDEF"
                JSR     SPC             ;Send a space
                LDX     #$00            ;Zero X Reg for "0"
MTLOOP          TXA                     ;Xfer to A Reg
                JSR     BIN2ASC         ;Convert Byte to two ASCII digits
                TYA                     ;Xfer the low nibble character to A Reg
                JSR     B_CHROUT        ;Send least significant HEX to terminal
                INX                     ;Increment to next HEX character
                CPX     #$10            ;Check for 16
                BNE     MTLOOP          ;Branch back till done
                JMP     CROUT           ;Do a CR/LF and return
;
;[E] Examine/Edit command: Display in HEX then change the contents of a specified memory address
CHANGE          JSR     SETUP           ;Request HEX address input from terminal
CHNG_LP         LDA     INDEXH          ;Test high byte address for RAM (less than $80)
                CMP     #$E0            ;Check for Start of ROM at $E000
                BCS     NO_RAM          ;Address is in ROM, can not edit.
;                BMI     NO_RAM          ;Address not in RAM
                JSR     SPC2            ;Send 2 spaces
                LDA     (INDEXL)        ;Read specified address
                JSR     PRBYTE          ;Display HEX value read
                JSR     BSOUT3T         ;Send 3 Backspaces
                JSR     HEXIN2          ;Get input, result in A Reg
                STA     (INDEXL)        ;Save entered value at Index pointer
                CMP     (INDEXL)        ;Compare to ensure a match
                BEQ     CHOK            ;Branch if compare is good
                LDA     #$3F            ;Get "?" for bad compare
                JSR     B_CHROUT        ;Send to terminal
CHOK            JSR     INCINDEX        ;Increment Index
                BRA     CHNG_LP         ;Loop to continue command
NO_RAM          LDA     #$2B            ;Get address range message
                JSR     PROMPT          ;Send to console
                LDA     #$2D            ;Get RAM message
                JSR     PROMPT          ;Send to console
                BRA     CHANGE          ;Branch back and try again
;
;[G] GO command: Begin executing program code at a specified address.
; Prompts the user for a start address, places it in COMLO/COMHI. If no address entered,
; uses default address at COMLO/COMHI. Loads the A,X,Y,P Registers from presets and does
; a JSR to the routine. Upon return, Registers are saved back to presets for display later.
; Also saves the stack pointer and status Register upon return.
; Note: Stack pointer is not changed due to IRQ service routines.
GO              SMB7    CMDFLAG         ;Set bit7 of command flag
                JSR     SETUP           ;Get HEX address (A/Y Regs hold 16-bit value)
                BEQ     EXEC_GO         ;If not, setup Regs and execute (Z flag updated)
                STA     COMLO           ;Save entered address to pointer low byte
                STY     COMHI           ;Save entered address to pointer hi byte
;
;Preload all 65C02 MPU Registers from Monitor's preset/result variables
EXEC_GO         LDA     PREG            ;Load processor status Register preset
                PHA                     ;Push it to the stack
                LDA     AREG            ;Load A-Reg preset
                LDX     XREG            ;Load X-Reg preset
                LDY     YREG            ;Load Y-Reg preset
                PLP                     ;Pull the processor status Register
;
;Call user program code as a subroutine
                JSR     DOCOM           ;Execute code at specified address
;
;Store all 65C02 MPU Registers to Monitor's preset/result variables: store results
                PHP                     ;Save the processor status Register to the stack
                STA     AREG            ;Store A-Reg result
                STX     XREG            ;Store X-Reg result
                STY     YREG            ;Store Y-Reg result
                PLA                     ;Get the processor status Register
                STA     PREG            ;Store the result
                TSX                     ;Xfer stack pointer to X-Reg
                STX     SREG            ;Store the result
                CLD                     ;Clear BCD mode in case of sloppy user code ;-)
TXT_EXT         RTS                     ;Return to caller
DOCOM           JMP     (COMLO)         ;Execute the command
;
;[T] LOCATE TEXT STRING command: search memory for an entered text string
;Memory range scanned is $0800 through $FFFF (setup before SENGINE subroutine is invoked)
;SRCHTXT subroutine: request 1 - 16 character text string from terminal, followed by Return
;[ESCAPE] aborts, [BACKSPACE] erases last keystroke. String will be stored in SRCHBUFF
SRCHTXT         LDA     #$08            ;Get msg " find text:"
                JSR     PROMPT          ;Send to terminal
                LDX     #$00            ;Initialize index/byte counter
STLOOP          JSR     B_CHRIN         ;Get input from terminal
                CMP     #$0D            ;Check for C/R
                BEQ     SRCHRDY1        ;Branch to search engine
                CMP     #$1B            ;Check for ESC
                BEQ     TXT_EXT         ;Exit to borrowed RTS
                CMP     #$08            ;Check for B/S
                BNE     STBRA           ;If not, store character into buffer
                TXA                     ;Xfer count to A Reg
                BEQ     STLOOP          ;Branch to input if zero
                JSR     BSOUT           ;Else, send B/S to terminal
                DEX                     ;Decrement index/byte counter
                BRA     STLOOP          ;Branch back and continue
STBRA           STA     SRCHBUFF,X      ;Store character in buffer location
                JSR     B_CHROUT        ;Send character to terminal
                INX                     ;Increment counter
                CPX     #$10            ;Check count for 16
                BNE     STLOOP          ;Loop back for another character
                LDA     #$08            ;Get start address for $0800
                BRA     SRCHRDY1        ;Branch to search engine
;
;[H] LOCATE BYTE STRING command: Search memory for an entered byte string. Memory range
; scanned is $0400 through $FFFF. SRCHBYT subroutine: request 0 - 16 byte string from
; terminal, byte followed by [RETURN]. [ESCAPE] aborts. HEX data will be stored in SRCHBUFF.
; minor update from Mike Barry, saves a byte.
SRCHBYT         SMB7    CMDFLAG         ;Set bit7 of command flag
                LDA     #$09            ;Get msg " find bin:"
                JSR     PROMPT          ;Send to terminal
                LDX     #$00            ;Initialize index
SBLOOP          PHX                     ;Save index on stack
                JSR     HEXIN2          ;Request HEX byte
                JSR     SPC             ;Send space to terminal
                PLX                     ;Restore index from stack
                LDY     BUFIDX          ;Get # of characters entered
                BEQ     SRCHRDY         ;Branch if no characters
                STA     SRCHBUFF,X      ;Else, store in buffer
                INX                     ;Increment index
                CPX     #$10            ;Check for 16 (max)
                BNE     SBLOOP          ;Loop back until done/full
SRCHRDY         LDA     #$04            ;Get start address for $0400
SRCHRDY1        STA     INDEXH          ;Store to Index high byte
                STZ     INDEXL          ;Zero Index low byte ($XX00)
                STX     IDX             ;Save input character count
                TXA                     ;Check buffer count (for zero)
                BEQ     NOWRAP          ;Exit if no bytes in buffer
;
;SENGINE subroutine: Scan memory range $XX00 through $FFFF for exact match to string contained
; in buffer SRCHBUFF (1 to 16 bytes/characters). Display address of first byte/character of
; each match found until the end of memory is reached.
SENGINE         LDA     #$0C            ;Else, get msg "Searching.."
                JSR     PROMPT          ;Send to terminal
SENGBR2         LDX     #$00            ;Initialize buffer index
SENGBR3         JSR     SENGBYT         ;Get the next byte from Index pointer
                CMP     SRCHBUFF,X      ;Compare to search buffer
                BEQ     SENGBR1         ;Branch for a match
                JSR     SINCPTR         ;Increment pointer, test for end of memory
                BRA     SENGBR2         ;Loop back to continue
SENGBR1         JSR     SINCPTR         ;Increment pointer, test for end of memory
                INX                     ;Increment buffer index
                CPX     IDX             ;Compare buffer index to address index
                BNE     SENGBR3         ;Loop back until done
                SEC                     ;Subtract buffer index from memory pointer; Set carry
                LDA     INDEXL          ;Get current address for match lo byte
                SBC     IDX             ;Subtract from buffer index
                STA     INDEXL          ;Save it back to lo address pointer
                LDA     INDEXH          ;Get current address for match hi byte
                SBC     #$00            ;Subtract carry flag
                STA     INDEXH          ;Save it back to hi address pointer
                LDA     #$0B            ;Get msg "found"
                JSR     PROMPT          ;Send to terminal
                LDA     #':'            ;Get Ascii colon
                JSR     B_CHROUT        ;Send to console
                JSR     PRINDEX         ;Print Index address
                LDA     #$0D            ;Get msg "(n)ext? "
                JSR     PROMPT          ;Send to terminal
                JSR     RDCHAR          ;Get input from terminal
                CMP     #$4E            ;Check for "(n)ext"
                BNE     NOWRAP          ;Exit if not requesting next
                JSR     SINCPTR         ;Increment address pointer, test for end of memory
                BRA     SENGBR2         ;Branch back and continue till done
;
;Search Engine GetByte routine: This routine gets the byte value from the current Index pointer
; location. It also checks the Index location FIRST. The I/O page is excluded from the actual data
; search to prevent corrupting any I/O devices which are sensitive to any READ operations outside
; the BIOS which supports it. An example is the NXP UART family, of which the SCC2691 is used here.
; Current I/O Page Range is $FE00 - $FE9F
; NOTE: $FEA0 - $FEFF used for vector/config data - allows searching here
SENGBYT         LDA     INDEXH          ;Get High byte address for current Index
                CMP     #$FE            ;Check for Base I/O page
                BEQ     CHK_UPR         ;If yes, check for I/O range
SENRTBYT        LDA     (INDEXL)        ;Else Get byte from current pointer
                RTS                     ;Return to caller
CHK_UPR         LDA     INDEXL          ;Get Low byte address for current Index
                CMP     #$A0            ;Check for end of I/O addresses
                BCS     SENRTBYT        ;Return ROM data if range is $FEA0 or higher
                LDA     #$FE            ;Get $FE as seed byte instead of I/O device read
NOWRAP          RTS                     ;Return to caller
;
;Increment memory address pointer. If pointer high byte = 00 (end of searchable ROM memory),
; send "not found" to terminal then return to Monitor
SINCPTR         JSR     INCINDEX        ;Increment Index pointer
                LDA     INDEXH          ;Check for wrap to $0000
                BNE     NOWRAP          ;If not, return
                PLA                     ;Else, Pull return address from stack
                PLA                     ;and exit with msg
                LDA     #$0A            ;Get msg "not found"
                JMP     PROMPT          ;Send msg to terminal and return
;
;[I] command: TEXT ENTRY enter ASCII text beginning at a specified address
TEXT            JSR     SETUP           ;Send "I" command, handle setup
EDJMP1          JSR     CROUT           ;Send CR,LF to terminal
                STA     TEMP2L          ;Save current edit address
                STY     TEMP2H          ;Save high byte
EDJMP2          JSR     B_CHRIN         ;Request a keystroke from terminal
                CMP     #$1B            ;Check for end text entry
                BEQ     EDITDUN         ;Branch and close out if yes
                CMP     #$0D            ;Else, check for Return key
                BNE     ENOTRET         ;Branch if not
                STA     (INDEXL)        ;Save CR to current Index pointer
                JSR     INCINDEX        ;Increment edit memory address pointer
                LDA     #$0A            ;Get a LF character
                STA     (INDEXL)        ;Store it in memory
                JSR     INCINDEX        ;Increment edit memory address pointer
                LDA     INDEXL          ;Get Start of next line
                LDY     INDEXH          ;and the high byte
                BRA     EDJMP1          ;Loop back to continue
ENOTRET         CMP     #$08            ;Check for backspace character
                BEQ     EDBKSPC         ;Branch if yes
                STA     (INDEXL)        ;Else, save to current Index pointer
                JSR     B_CHROUT        ;Send keystroke to terminal
                JSR     INCINDEX        ;Increment edit memory address pointer
                BRA     EDJMP2          ;Loop back to EDJMP2
;
;Handle Backspace, don't allow past starting address
EDBKSPC         LDA     INDEXL          ;Get current index low byte
                CMP     TEMP2L          ;Compare to initial start address
                BNE     EDDOBKS         ;If not equal, perform backspace
                LDA     INDEXH          ;Get current index high byte
                CMP     TEMP2H          ;Compare to initial start address
                BEQ     EDJMP2          ;If same, branch to input loop
EDDOBKS         JSR     BSOUT           ;Send backspace to terminal
                JSR     DECINDEX        ;Decrement edit memory address pointer
                LDA     #$00            ;Get a null character
                STA     (INDEXL)        ;Store in place of character
                BRA     EDJMP2          ;LOOP back to EDJMP2
EDITDUN         JSR     CR2             ;Send 2 CR,LF to terminal
                JMP     PRINDEX         ;Print INDEX value and return
;
;**************************************************************************************************
;*                              Processor Register Operations                                     *
;**************************************************************************************************
;
;[P] Processor Status command: Display then change PS preset/result
PRG             LDA     #$0E            ;Get MSG # for Processor Status Register
                BRA     REG_UPT         ;Finish Register update
;
;[S] Stack Pointer command: Display then change SP preset/result
SRG             LDA     #$0F            ;Get MSG # for Stack Register
                BRA     REG_UPT         ;Finish Register update
;
;[Y] Y-Register command: Display then change Y-Reg preset/result
YRG             LDA     #$10            ;Get MSG # for Y Reg
                BRA     REG_UPT         ;Finish Register update
;
;[X] X-Register command: Display then change X-Reg preset/result
XRG             LDA     #$11            ;Get MSG # for X Reg
                BRA     REG_UPT         ;Finish Register update
;
;[A] A-Register command: Display then change A-Reg preset/result
ARG             LDA     #$12            ;Get MSG # for A Reg
;
REG_UPT         PHA                     ;Save MSG # to stack
                PHA                     ;Save MSG # to stack again
                JSR     PROMPT          ;Print Register message
                PLX                     ;Get Index to Registers
                LDA     PREG-$0E,X      ;Read Register (A,X,Y,S,P) preset/result
                JSR     PRBYTE          ;Display HEX value of Register
                JSR     SPC             ;Send [SPACE] to terminal
                JSR     HEXIN2          ;Get up to 2 HEX characters
                PLX                     ;Get MSG # from stack
                STA     PREG-$0E,X      ;Write Register (A,X,Y,S,P) preset/result
MNE_QUIT        RTS                     ;Return to caller
;
;[R] REGISTERS command: Display contents of all preset/result memory locations
PRSTAT          JSR     B_CHROUT        ;Send "R" to terminal
PRSTAT1         LDA     #$13            ;Get Header msg
                JSR     PROMPT          ;Send to terminal
                LDA     PCL             ;Get PC Low byte
                LDY     PCH             ;Get PC High byte
                JSR     PRWORD          ;Print 16-bit word
                JSR     SPC             ;Send 1 space
;
                LDX     #$04            ;Set for count of 4
REGPLOOP        LDA     PREG,X          ;Start with A Reg variable
                JSR     PRBYTE          ;Print it
                JSR     SPC             ;Send 1 space
                DEX                     ;Decrement count
                BNE     REGPLOOP        ;Loop back till all 4 are sent
;
                LDA     PREG            ;Get Status Register preset
                LDX     #$08            ;Get the index count for 8 bits
SREG_LP         ASL     A               ;Shift bit into Carry
                PHA                     ;Save current (shifted) SR value
                LDA     #$30            ;Load an Ascii zero
                ADC     #$00            ;Add zero (with Carry)
                JSR     B_CHROUT        ;Print bit value (0 or 1)
                PLA                     ;Get current (shifted) SR value
                DEX                     ;Decrement bit count
                BNE     SREG_LP         ;Loop back until all 8 printed
                JMP     CROUT           ;Send CR/LF and return to caller
;
;**************************************************************************************************
;*                              Control Key Operations (Ctrl-?)                                   *
;**************************************************************************************************
;
;[CTRL-A] Start Assembler:
ASSEMBLER       LDA     #$2E            ;Get Intro message
                JSR     PROMPT          ;Send to console
                LDA     #$03            ;Get Msg 03 -" addr:"
                JSR     HEX4            ;Print msg and get address
MNE_RETRY
                JSR     CROUT           ;Send CR,LF to Console
                JSR     PRINDEX         ;Send starting address to Console
                JSR     SPC4            ;Send 4 spaces
;
; Now get an Instruction entry and put into SRCHBUFF.
; This allows for a full instruction line entry which is buffered. This routine also allows
; editing of the entry input and uses a C/R to exit to the next routine to start instruction
; decode.
; NOTE: SRCHBUFF is used by multiple routines, so it won't show the entered data if you leave
; the assembler and use the "D" (display memory) command. 
;
                LDX     #$00            ;Set input count to zero
MNE_LOOP        JSR     RDCHAR          ;Get input from terminal
                CMP     #$0D            ;Check for CR
                BEQ     MNE_CRUNCH      ;Branch to parse routine
                CMP     #$1B            ;Check for ESC
                BEQ     MNE_QUIT        ;Exit to borrowed RTS
                CMP     #$08            ;Check for Backspace
                BNE     MNE_BRA         ;If not, store character into buffer
                TXA                     ;Xfer count to A Reg
                BEQ     MNE_LOOP        ;Branch to input if zero
                JSR     BSOUT           ;Else, send Backspace to terminal
                DEX                     ;Decrement index/byte counter
                BRA     MNE_LOOP        ;Branch back and continue
MNE_BRA         STA     SRCHBUFF,X      ;Store character in buffer location
                JSR     B_CHROUT        ;Send character to terminal
                INX                     ;Increment counter
                CPX     #$0F            ;Check count for 15
                BNE     MNE_LOOP        ;Loop back for another character
                JSR     BEEP            ;Send Beep to Console (buffer overflow)
                BRA     MNE_RETRY       ;Branch back and try again
;
MNE_CRUNCH
                STX     SRCHBUFF+15     ;Save Input count at end of buffer
;
; Just for test purposes, we're storing the entered line at $0700
;
                STX     $070F           ;Save Input buffer count
                LDX     #$0E            ;Set count of 14
MNE_XFER        LDA     SRCHBUFF,X      ;Load input buffer
                STA     $0700,x         ;Save it to a temp area
                DEX                     ;Decrement count
                BPL     MNE_XFER        ;Branch back until done
;
                JMP     $0800           ;Jump to RAM development code
\
;[CTRL-D] Disassembler: Table-Driven Disassembler. Supports ALL W65C02 Opcodes and Address modes.
DISASSEMBLER    LDA     #$28            ;Intro Message
                JSR     PROMPT          ;Send to terminal
                LDA     #$03            ;Msg 03 -" addr:"
                JSR     HEX4            ;Print msg and get address
                JSR     CROUT           ;Send CR,LF to terminal
RPT_LIST        LDX     #$16            ;Set list count to 22
DIS_LOOP        PHX                     ;Push count to stack
                JSR     DIS_LINE        ;Disassemble 1 instruction
                PLX                     ;Pull count from stack
                DEX                     ;Decrement count
                BNE     DIS_LOOP        ;Loop back till list count is zero
LST_LOOP        JSR     B_CHRIN         ;Get input from terminal
                CMP     #$0D            ;Check for Return key
                BEQ     RPT_LIST        ;If yes, repeat list
                CMP     #$1B            ;Check for Escape
                BEQ     EXT_LIST        ;If yes, exit
                CMP     #$20            ;Check for space
                BEQ     LIST_ONE        ;If yes, disassemble 1 line
                JSR     BEEP            ;Else, beep for error
                BRA     LST_LOOP        ;Loop back again
LIST_ONE        JSR     DIS_LINE        ;Else, Disassemble one line
                BRA     LST_LOOP        ;Branch back and continue
;
;DISASSEMBLE LINE: disassemble 1 instruction from working address
DIS_LINE        STZ     TEMP2           ;Clear all flag bits
                JSR     PRINDEX         ;Print working address
                JSR     SPC2            ;Send 2 spaces to terminal
                LDA     (INDEXL)        ;Read opcode from working memory pointer
                STA     OPXMDM          ;Save opcode
                JSR     PRB_SPC2        ;Print byte, 2 spaces
                LSR     A               ;Divide by 2 / shift low order bit into carry flag
                TAX                     ;Xfer Opcode /2 to X Reg
                LDA     HDLR_IDX,X      ;Get Pointer to handler table
                BCS     USE_RGHT        ;If carry set use low nibble (odd)
                LSR     A               ;Else shift upper nibble to lower nibble (even)
                LSR     A
                LSR     A
                LSR     A
USE_RGHT        AND     #$0F            ;Mask off high nibble
                ASL     A               ;Multiply by 2 for index
                TAX                     ;Use handler pointer to index handler table
                JSR     DODISL          ;Call disassembler handler
                JSR     CROUT           ;Send CR,LF to terminal
;
;INCNDX routine: increment working address pointer then read it
INCNDX          JSR     INCINDEX        ;Increment working address pointer
                LDA     (INDEXL)        ;Read from working memory address
EXT_LIST        RTS                     ;Done, return to caller/exit
;
DODISL          JMP     (HDLR_TAB,X)    ;Execute address mode handler
;
;THREE BYTE routine: display operand bytes then mnemonic for three-byte instruction
; TWO BYTE routine: display operand byte then mnemonic for two-byte instruction
TRI_BYTE        SMB7    TEMP2           ;Set Flag bit for 3-byte instruction
TWO_BYTE        JSR     GET_NEXT        ;Read, display operand byte
                STA     CRCLO           ;Save operand byte in CRCLO
                BBR7    TEMP2,2BYTSPC   ;Branch for 2-byte is clear
                JSR     GET_NEXT        ;Read, display operand high byte
                STA     CRCHI           ;Save operand high byte in CRCHI
                BRA     3BYTSPC         ;Send 2 spaces, send Mnemonic, return
;
;IMPLIED disassembler handler: single byte instructions: implied mode
; (note: ACC_MODE handler calls this)
IMPLIED         JSR     SPC4            ;Send 4 spaces
2BYTSPC         JSR     SPC4            ;Send 4 spaces
3BYTSPC         JSR     SPC2            ;Send 2 spaces
;
;PRT_MNEM subroutine: send 3 character mnemonic to terminal
; Mnemonic indexed by opcode byte. Sends "???" if byte is not a valid opcode
PRT_MNEM        LDY     OPXMDM          ;Get current Opcode as index
                LDX     MNE_PTAB,Y      ;Get opcode pointer from table
                LDA     DIS_NMEM,X      ;Get left byte
                STA     PTRL            ;Store it to pointer
                LDA     DIS_NMEM+1,X    ;Get right byte
                STA     PTRH            ;Store it to pointer
                LDX     #$03            ;Set count for 3 characters
NEXT_NME        LDA     #$00            ;Zero A Reg
                LDY     #$05            ;Set count for 5 bits per character
LOOP_NME        ASL     PTRH            ;Shift right byte into carry
                ROL     PTRL            ;Rotate left byte into A Reg
                ROL     A               ;Rotate into A Reg
                DEY                     ;Decrement bit count
                BNE     LOOP_NME        ;Loop back till 5 bits in A Reg
                ADC     #$3F            ;Add $3F to convert to Ascii
                JSR     B_CHROUT        ;Send the character to terminal
                DEX                     ;Decrement character count
                BNE     NEXT_NME        ;Loop back till 3 characters sent
                BRA     BR_SPC2         ;Send 2 spaces to terminal, return
;
;GET_NEXT subroutine: increment/read working address
; Display byte, send 2 spaces to terminal (displays operand byte(s))
GET_NEXT        JSR     INCNDX          ;Increment working index
PRB_SPC2        JSR     PRBYTE          ;Display Byte from working index
BR_SPC2         JMP     SPC2            ;Send 2 spaces to terminal and return
;
;Disassembler handlers:
;
;LF_BRKT subroutine: send "(" to terminal
LF_BRKT         LDA     #$28            ;Get "("
                BRA     BR_COUT         ;Send to terminal and return
;
;ZP_IMMEDIATE: two byte instructions: zero-page immediate mode
ZP_IMED         JSR     TWO_BYTE        ;Display operand byte, then mnemonic
                LDA     #$23            ;Get "#" character
                JSR     B_CHROUT        ;Send to terminal
                BRA     PRT1_OP         ;Display operand byte again, return
;
;ACC_MODE: single byte A Reg mode instructions: implied mode
ACC_MODE        JSR     IMPLIED         ;Send 10 spaces to terminal then display mnemonic
                LDA     #$41            ;Get "A" character
BR_COUT         JMP     B_CHROUT        ;Send it and return
;
;ABSOLUTE: three byte instructions: absolute mode
ABSOLUTE        JSR     TRI_BYTE        ;Display operand bytes, then mnemonic
;
;Print 2 Operands: display operand bytes of a three-byte instruction
PRT2_OP         JSR     DOLLAR          ;Send "$" to terminal
                LDA     CRCHI           ;Load operand high byte
                JSR     PRBYTE          ;Send to terminal
BR_PRBTE        LDA     CRCLO           ;Load operand low byte
                JMP     PRBYTE          ;Send to terminal and return
;
;ZP_ABS: two byte instructions: zero-page absolute
ZP_ABS          JSR     TWO_BYTE        ;Display operand byte, then mnemonic
;
;Print 1 Operand byte: display operand byte of a two-byte instruction
PRT1_OP         JSR     DOLLAR          ;Send "$" to terminal
                BRA     BR_PRBTE        ;Branch to complete
;
;INDIRECT: two or three byte instructions: indirect modes
INDIRECT        LDA     OPXMDM          ;Read saved opcode byte
                CMP     #$6C            ;Check for JMP(INDIRECT)
                BNE     ZP_IND          ;Branch if not
;
                JSR     TRI_BYTE        ;Display operand bytes, then mnemonic
                JSR     LF_BRKT         ;Send "(" to terminal
                JSR     PRT2_OP         ;Display operand bytes again
                BRA     RT_BRKT         ;Send ")" to terminal, return
;
;Following group is used multiple times, space savings
DSPLY3          JSR     TWO_BYTE        ;Display operand byte, then mnemonic
                JSR     LF_BRKT         ;Send "(" to terminal
                BRA     PRT1_OP         ;Display operand byte again, return
;
;this is for a two byte instruction: zero page indirect mode
ZP_IND          JSR     DSPLY3          ;Do the 3 routines
;
;RT_BRKT subroutine: send ")" to terminal
RT_BRKT         LDA     #$29            ;Get ")"
                BRA     BR_COUT         ;Send to terminal and return
;
;ZP_ABS_X: two byte instructions: zero-page absolute indexed by X mode
ZP_ABS_X        JSR     ZP_ABS          ;Display operand byte, mnemonic, operand byte
;
;Print Comma,X: send ",X" to terminal
COM_X           LDA     #$2C            ;Get ","
                JSR     B_CHROUT        ;Send to terminal
                LDA     #$58            ;Get "X"
                BRA     BR_COUT         ;Send to terminal, return
;
;ZP_ABS_Y: two byte instructions: zero-page absolute indexed by Y mode
ZP_ABS_Y        JSR     ZP_ABS          ;Display operand byte, mnemonic, operand byte
;
;Print Comma,Y: send ",Y" to terminal
COM_Y           LDA     #$2C            ;Get ","
                JSR     B_CHROUT        ;Send to terminal
                LDA     #$59            ;Get "Y"
                BRA     BR_COUT         ;Send to terminal, return
;
;ABS_Y: three byte instructions: absolute indexed by Y mode
;ABS_X: three byte instructions: absolute indexed by X mode
ABS_Y           SMB6    TEMP2
ABS_X           JSR     TRI_BYTE        ;Display operand bytes, then mnemonic
                JSR     PRT2_OP         ;Display operand bytes again
                BBS6    TEMP2,COM_Y
                BRA     COM_X           ;Send ",X" to terminal, return
;
;ZP_IND_X: two byte instructions: zero-page indirect pre-indexed by X mode
ZP_IND_X        JSR     DSPLY3          ;Do the 3 routines
                JSR     COM_X           ;Send ",X" to terminal
                BRA     RT_BRKT         ;Send ")" to terminal, return
;
;ZP_IND_Y: two byte instructions: zero-page indirect post-indexed by Y mode
ZP_IND_Y        JSR     DSPLY3          ;Do the 3 routines
                JSR     RT_BRKT         ;Send ")" to terminal
                BRA     COM_Y           ;Send ",Y" to terminal, return
;
;IND_ABS_X: three byte instruction: JMP (INDIRECT,X) 16 bit indirect
IND_ABS_X       JSR     TRI_BYTE        ;Display operand bytes, then mnemonic
                JSR     LF_BRKT         ;Send "(" to terminal
                JSR     PRT2_OP         ;Display operand bytes again
                JSR     COM_X           ;Send ",X" to terminal
                BRA     RT_BRKT         ;Send ")" to terminal,done w/INDABSX handler, return
;
;ZP_XMB: two byte instructions: zero page set/clear memory bit
ZP_XMB          JSR     SRMB            ;Display operand/mnemonic, isolate bit selector from opcode
                CMP     #$08            ;Check if 0-7 or 8-F
                BCC     SRBIT           ;Just add $30 (0-7)
                SBC     #$08            ;Subtract $08 - convert $8-$F to $0-$7
SRBIT           CLC                     ;Convert bit selector value to an ASCII decimal digit
                ADC     #$30            ;Add "0" to bit selector value
                JSR     B_CHROUT        ;Send digit to terminal
                JSR     SPC             ;Send a space to terminal
                BRA     PRT1_OP         ;Display operand byte again then return
;
;ZP_BBX: three byte instruction: branch on zero-page bit set/clear
ZP_BBX          JSR     SRMB2           ;Display operand/mnemonic, isolate bit selector from opcode
                CMP     #$08            ;Check if $0-$7 or $8-$F
                BCC     SRBIT2          ;Just add $30 ($0-$7)
                SBC     #$08            ;Subtract $08 - convert $8-$F to $0-$7
SRBIT2          JSR     SRBIT           ;Convert and display bit selector digit
                LDA     CRCHI           ;Move second operand to first operand position:
                STA     CRCLO           ;CRCLO = branch offset
                JSR     SPC             ;Send a space to terminal
                BRA     BBX_REL         ;Display branch target address then return
;
;RELATIVE BRANCH: two byte relative branch mode BBX_REL: three byte relative branch mode
; Both calculate then display relative branch target address
;
; Update 12th February 2021: Fix offset page for Branch. High byte address would not
; update properly and could show the wrong page.
REL_BRA         JSR     TWO_BYTE        ;Display operand byte, then mnemonic
BBX_REL         JSR     DOLLAR          ;Send "$" to terminal
                JSR     INCINDEX        ;Increment address, ref for branch offset
                LDA     CRCLO           ;Get branch operand value
                BMI     BRA_MINUS       ;Check for $80 or higher (branch is + / -)
                CLC                     ;Clear carry for add
                ADC     INDEXL          ;Add to Index lo
                PHA                     ;Save result to Stack
                LDA     INDEXH          ;Get Index Hi
                ADC     #$00            ;Add result from Carry flag to A Reg
                TAY                     ;Xfer Hi address to Y Reg
                PLA                     ;Get Lo Address from Stack
                BRA     REL_EXT         ;Print offset, cleanup, return
BRA_MINUS       EOR     #$FF            ;Get 1's complement of offset
                INC     A               ;Increment by 1
                STA     TEMP3           ;Save result
                SEC                     ;Set carry for subtract
                LDA     INDEXL          ;Get address Low byte
                SBC     TEMP3           ;Subtract branch offset
                PHA                     ;Save result to Stack
                LDA     INDEXH          ;Get address High byte
                SBC     #$00            ;Subtract carry flag
                TAY                     ;Xfer Hi address to Y Reg
                PLA                     ;Get Lo address from Stack
REL_EXT         JSR     PRWORD          ;Send address to terminal
                JMP     DECINDEX        ;Decrement working address, return
;
;SRMB2 subroutine: display 2 operand bytes, mnemonic, isolate bit selector from opcode
; SRMB subroutine: display 1 operand byte, mnemonic, isolate bit selector from opcode
SRMB2           LDA     (INDEXL)        ;Read from working index
                PHA                     ;Save byte to stack
                JSR     TRI_BYTE        ;Display operand bytes and mnemonic
                BRA     SRM             ;Skip down
SRMB            LDA     (INDEXL)        ;Read from working index
                PHA                     ;Save byte on STACK
                JSR     TWO_BYTE        ;Display operand byte and mnemonic
SRM             JSR     BSOUT2T         ;Send 2 Backspaces
                PLA                     ;Restore byte from stack
                LSR     A               ;Shift high nibble to low nibble
                LSR     A
                LSR     A
                LSR     A
                RTS                     ;Done SRMB2/SRMB, return
;
;[CNTRL-E] EEPROM Edit
; Allows editing of a single byte location within the EEPROM starting at $8000.
; Note that this routines tests for target addresses at $8000 or above, but does NOT
; test for I/O address ranges. One should be cautious about editing the EEPROM directly
; to ensure it doesn't become unusable by changing things wrongly.
;
; NOTE: If the PLD memory configuration is changed to increase RAM and decrease EEPROM,
;       the unlock code will not work correctly, as the minimum addressable EEPROM is
;       22KB. This is the case with the current configuration used here... 56KB of RAM
;       and 8KB of EEPROM.
;
EEDIT           LDA     #<TEMP2         ;Get address offset for TEMP2
                STA     SRCL            ;Store in Source address Low
                STZ     SRCH            ;Zero Source address High (Page Zero)
;
;Xfer byte write code to RAM for execution
                JSR     XFER_BYTE_WRT   ;Xfer byte write code to Page Zero
;
                LDA     #$2A            ;Get EEPROM edit msg
TRY_AGAIN       JSR     PROMPT          ;Send to console
;
CMP_OK2         JSR     CONTINUE        ;Prompt User for Y/N
                JSR     CROUT           ;Send CR/LF to console
;
                LDA     #$03            ;Get " addr:" msg
                JSR     HEX4            ;Display msg and get address
;
; Note: address in INDEXL/INDEXH and A/Y Regs
                STA     TGTL            ;Store in Target location Low
                STY     TGTH            ;Store in Target location High
                CPY     #$80            ;Check for ROM start or higher
                BCC     NOT_ROM         ;Address is not in EEPROM
;
                JSR     SPC2            ;Send 2 spaces
                LDA     (INDEXL)        ;Get memory data
                JSR     PRBYTE          ;Send to console
                JSR     BSOUT3T         ;Backspace 3 times
                JSR     HEXIN2          ;Get new data
;
; Note: new data is in A Reg
                STA     TEMP2           ;Store in Temp location
;
                JSR     BURN_BYTE       ;Update EEPROM Data
                LDA     (SRCL)          ;Get Source byte
                CMP     (TGTL)          ;Compare to Target in EEPROM
                BEQ     CMP_OK2         ;Branch if okay
                LDA     #$1F            ;Else, get error msg for failed write
                BRA     PRMPTSC         ;Send to console and exit
;
NOT_ROM         LDA     #$2B            ;Get address range msg
                JSR     PROMPT          ;Send to console
                LDA     #$2C            ;Get EEPROM msg
                BRA     TRY_AGAIN       ;Branch back and try again
;
;[CNTRL-Q] Query command:
QUERY           LDA     #$30            ;Get Query Commands Message
                BRA     PRMPTSC         ;Send to console and return
;
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
